fbradasc/RCTX/doc/PIC/328323-42266788.jpg

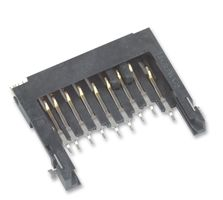
doc/PIC/328323-42266788.jpg
