fbradasc/RCTX/doc/EFR32M/Schematics/BRD4162A-A02-schematic.pdf

EFR32 Mighty Gecko Radio Board; 2.4 GHz 10 dBm, VDCDC to PAVDD

C | C
B | B
A | A
WSTK Connectors & Board ID | 4

# EFR32 Signal Assignments

Board Function | Page
| 1
| 2
| 3

# RF, Antenna & Power

# Title Page

# Revision History

Rev. | Description
A00 | Initial version.

# Updated EFR32 chip revision and 32 kHz

crystal part number.

A02 Fixing EFR32 pin names; Updated PCB revision.

A01

# Revision History

Rev. | Description
A00 | Initial version.

# Updated EFR32 chip revision and 32 kHz

crystal part number.

A02 Fixing EFR32 pin names; Updated PCB revision.

A01

# Revision History

Rev. | Description
A00 | Initial version.

# Updated EFR32 chip revision and 32 kHz

crystal part number.

A02 Fixing EFR32 pin names; Updated PCB revision.

A01

Size

Designed:

Revision

Sheet
of

Approved:

Sheet Created Date | Sheet Modified Date

## Document number

## Schematic Title

Design Created Date:

BOM Doc No:

## Page Title

BRD4162A | A02
Friday, January 20, 2017 | 1 | 4

A3

TAB | <OrgAddr2>

# EFR32MG12 2.4 GHz Radio Board

### <Cage Code>

Monday, April 02, 2012 | Monday, April 02, 2012

# SCHEMATIC1

# <Schematic Path>

# Title Page

Designed:

Approved:

## Schematic Title

## Page Title

Friday, January 20, 2017 | 1 | 4
TAB | <OrgAddr2>

# EFR32MG12 2.4 GHz Radio Board

Monday, April 02, 2012 | Monday, April 02, 2012

# SCHEMATIC1

# <Schematic Path>

# Title Page

Designed:

Approved:

## Schematic Title

## Page Title

Friday, January 20, 2017 | 1 | 4
TAB | <OrgAddr2>

# EFR32MG12 2.4 GHz Radio Board

Monday, April 02, 2012 | Monday, April 02, 2012

# SCHEMATIC1

# <Schematic Path>

# Title Page

PCB1

PCB4162A

# Antenna & Radio Interface

## High Frequency

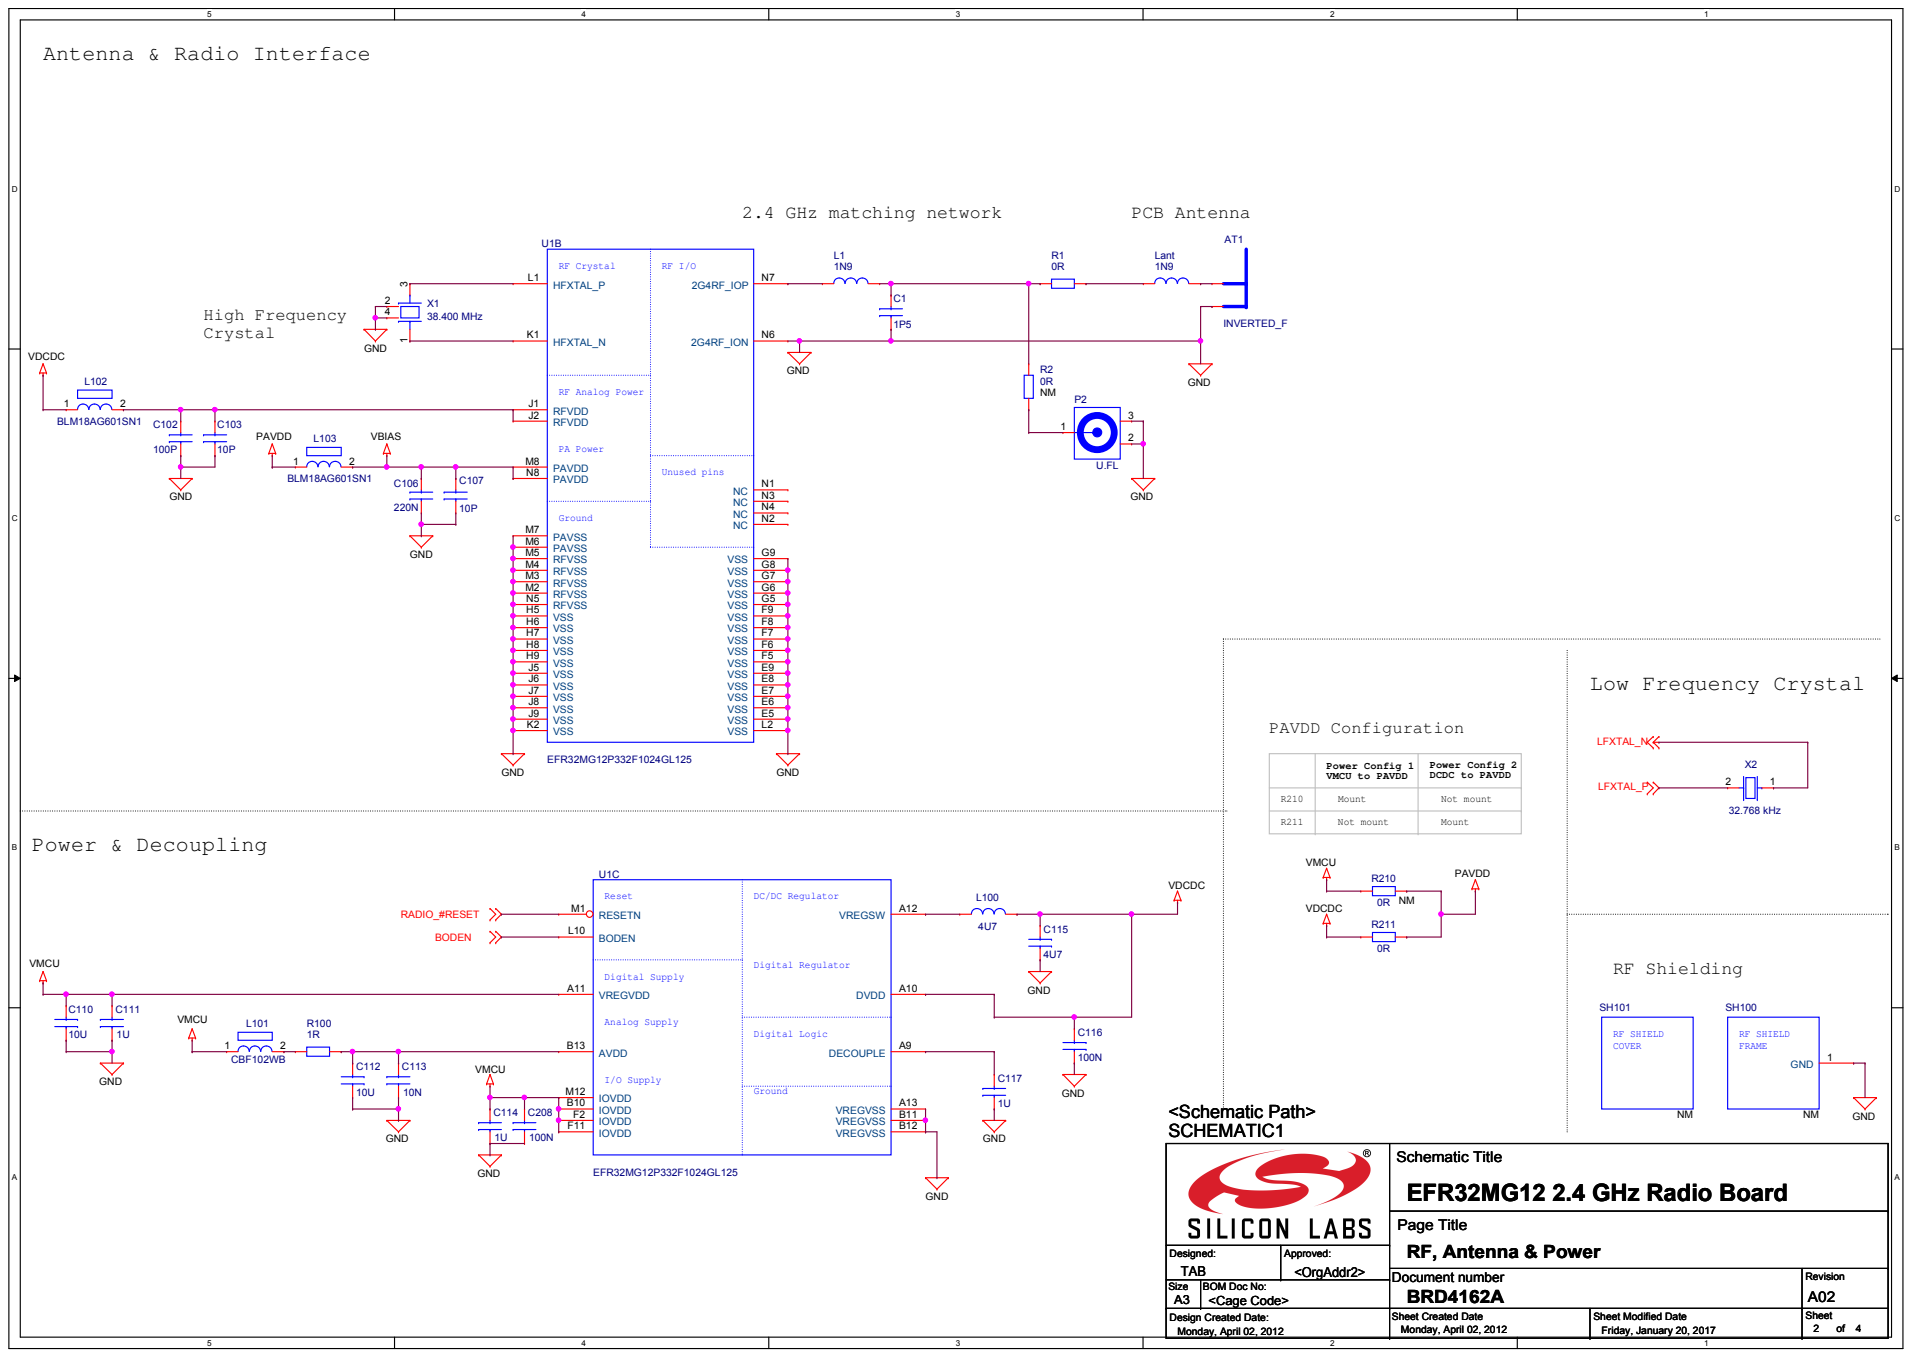
[picture p24: page 2]

# EFR32 I/O Port Pins EFR32 Pin Mapping

### EFR32 Pin EFR32 Peripheral

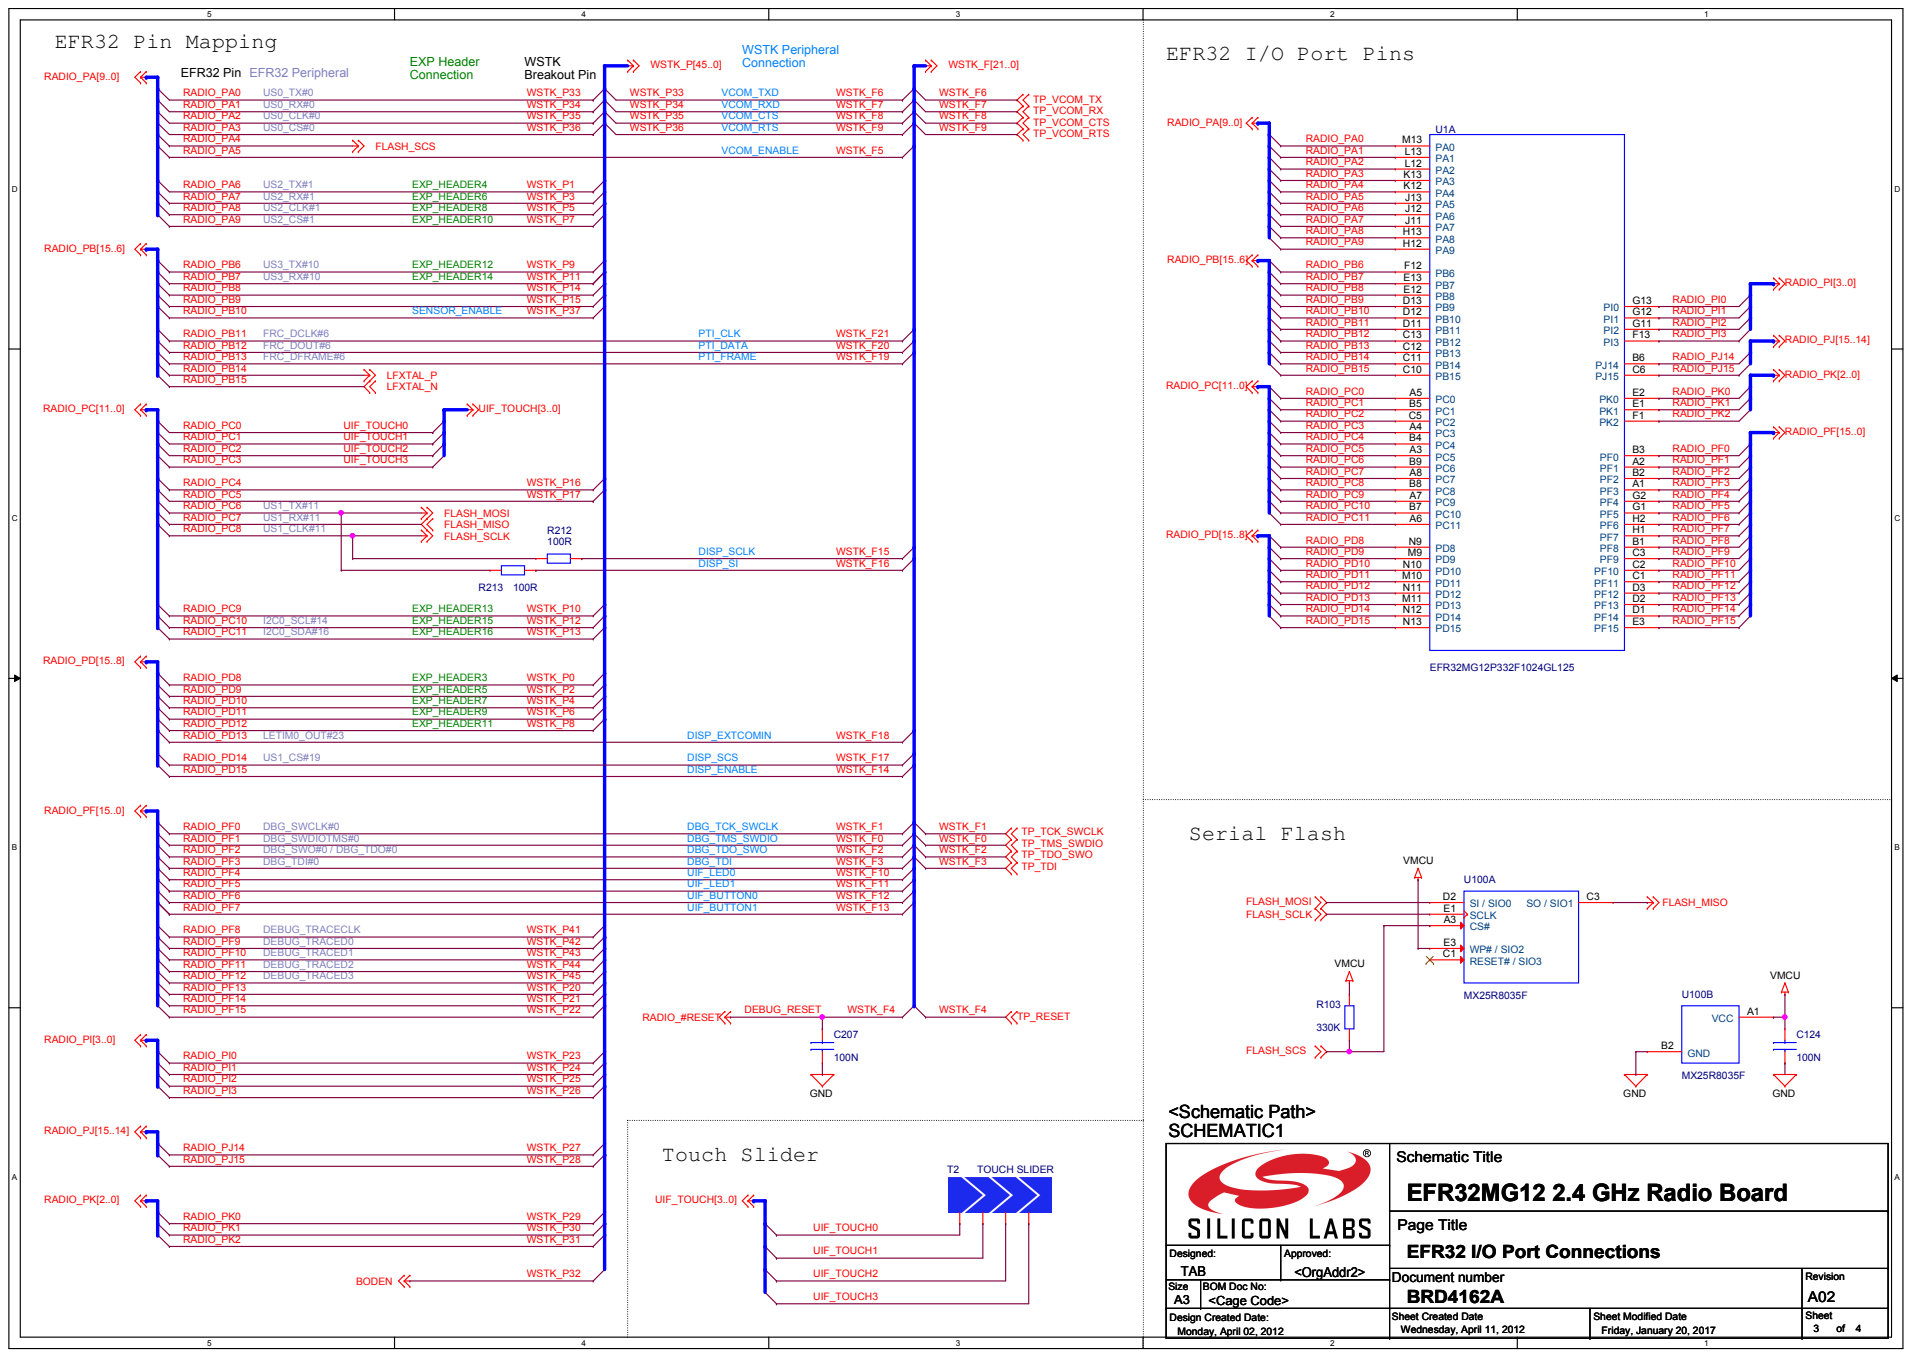
[picture p25: page 3]

# WSTK Connectors

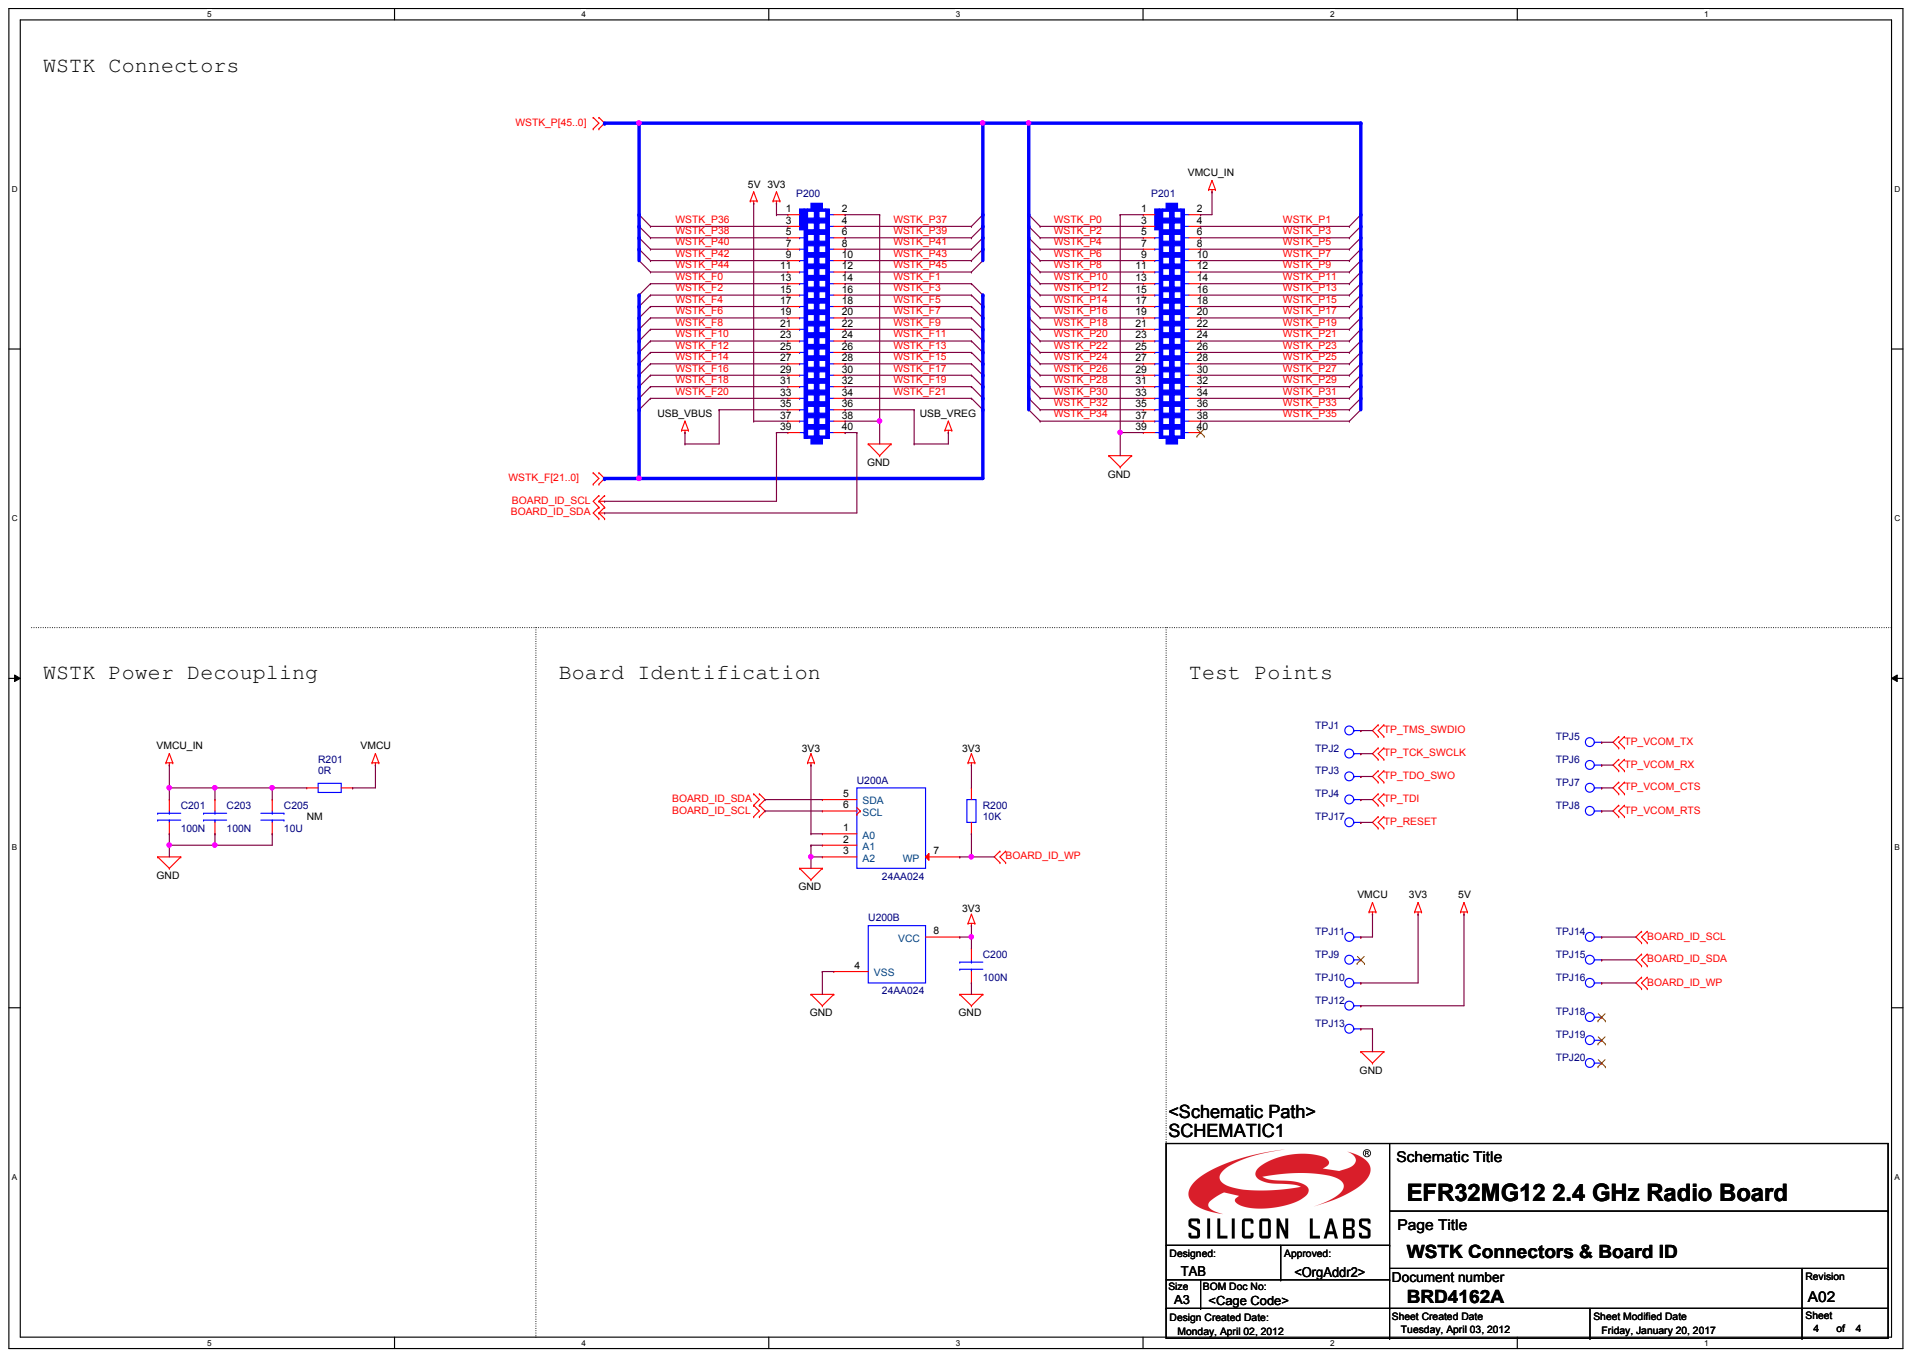
[picture p26: page 4]

Page Title
WSTK Connectors & Board ID
