fbradasc/RCTX/doc/EFR32M/Schematics/BRD4163A-A02-schematic.pdf

EFR32 Mighty Gecko Radio Board

C | C
B | B
A | A
WSTK Connectors & Board ID | 4

# EFR32 Signal Assignments

Board Function | Page
| 1
| 2
| 3

# RF, Antenna & Power

# Title Page

# Revision History

Rev. | Description
A00 | Initial version.

# Updated EFR32 chip revision and 32 kHz

crystal part number.

A02 Fixing EFR32 pin names; Updated PCB revision.

A01

# Revision History

Rev. | Description
A00 | Initial version.

# Updated EFR32 chip revision and 32 kHz

crystal part number.

A02 Fixing EFR32 pin names; Updated PCB revision.

A01

# Revision History

Rev. | Description
A00 | Initial version.

# Updated EFR32 chip revision and 32 kHz

crystal part number.

A02 Fixing EFR32 pin names; Updated PCB revision.

A01

# 2.4 GHz / 868 MHz 10 dBm, VDCDC to PAVDD

Size

Designed:

Revision

Sheet
of

Approved:

Sheet Created Date | Sheet Modified Date

## Document number

## Schematic Title

Design Created Date:

BOM Doc No:

## Page Title

BRD4163A | A02
Friday, January 20, 2017 | 1 | 4

A3

TAB | <OrgAddr2>

# EFR32MG12 Dual Band 2400/868 MHz Radio Board

### <Cage Code>

Monday, April 02, 2012 | Monday, April 02, 2012

# SCHEMATIC1

# <Schematic Path>

# Title Page

Designed:

Approved:

## Schematic Title

## Page Title

Friday, January 20, 2017 | 1 | 4
TAB | <OrgAddr2>

# EFR32MG12 Dual Band 2400/868 MHz Radio Board

Monday, April 02, 2012 | Monday, April 02, 2012

# SCHEMATIC1

# <Schematic Path>

# Title Page

Designed:

Approved:

## Schematic Title

## Page Title

Friday, January 20, 2017 | 1 | 4
TAB | <OrgAddr2>

# EFR32MG12 Dual Band 2400/868 MHz Radio Board

Monday, April 02, 2012 | Monday, April 02, 2012

# SCHEMATIC1

# <Schematic Path>

# Title Page

PCB1

PCB4163A

# Antenna & Radio Interface

## High Frequency

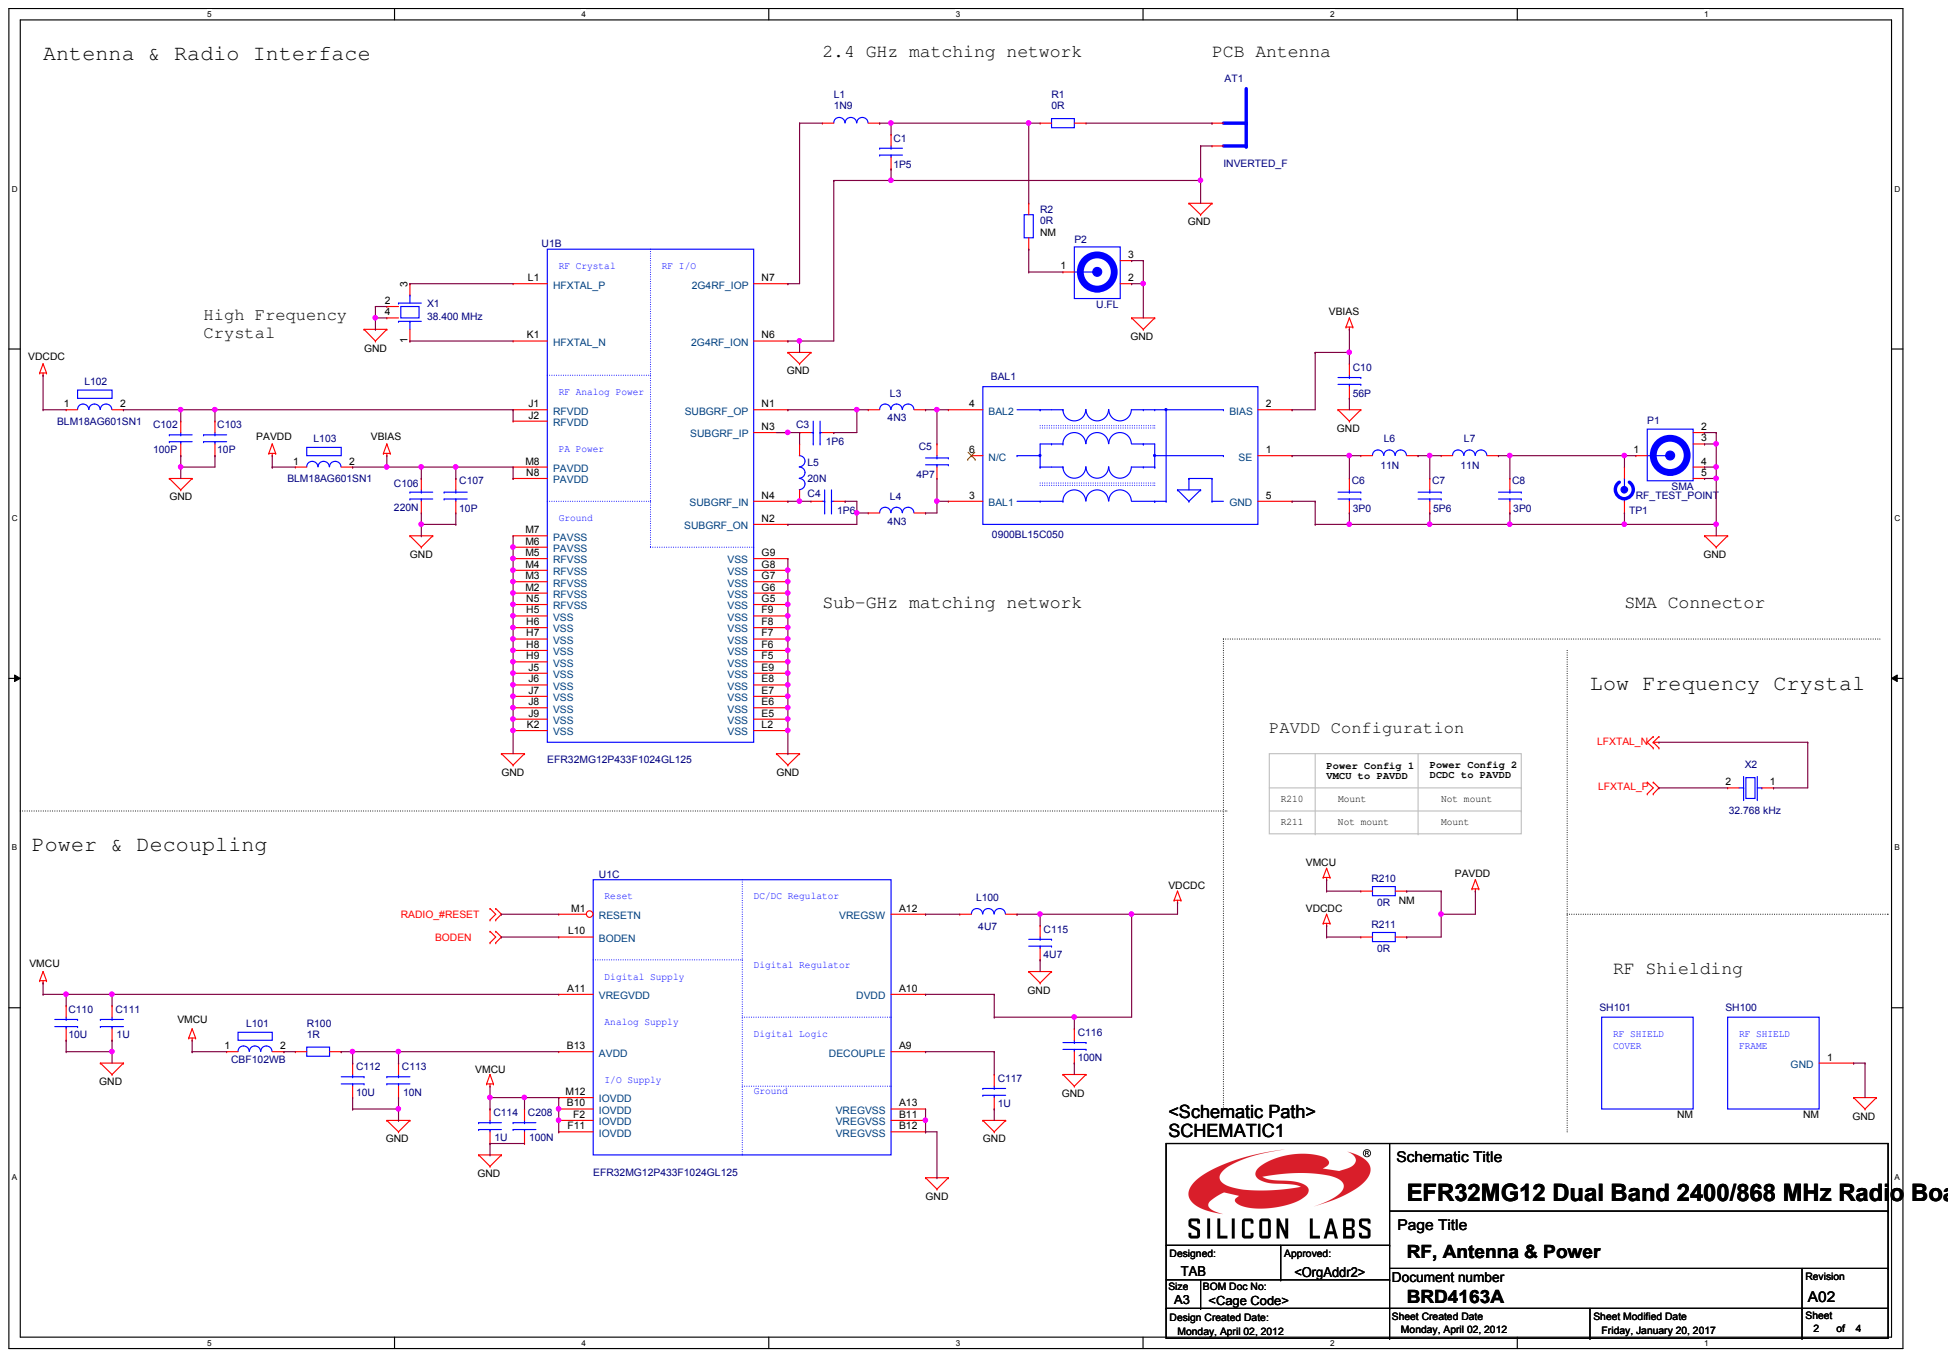
[picture p37: page 2]

Sub-GHz matching network

Schematic Title
EFR32MG12 Dual Band 2400/868 MHz Radio Board

# EFR32 I/O Port Pins EFR32 Pin Mapping

### EFR32 Pin EFR32 Peripheral

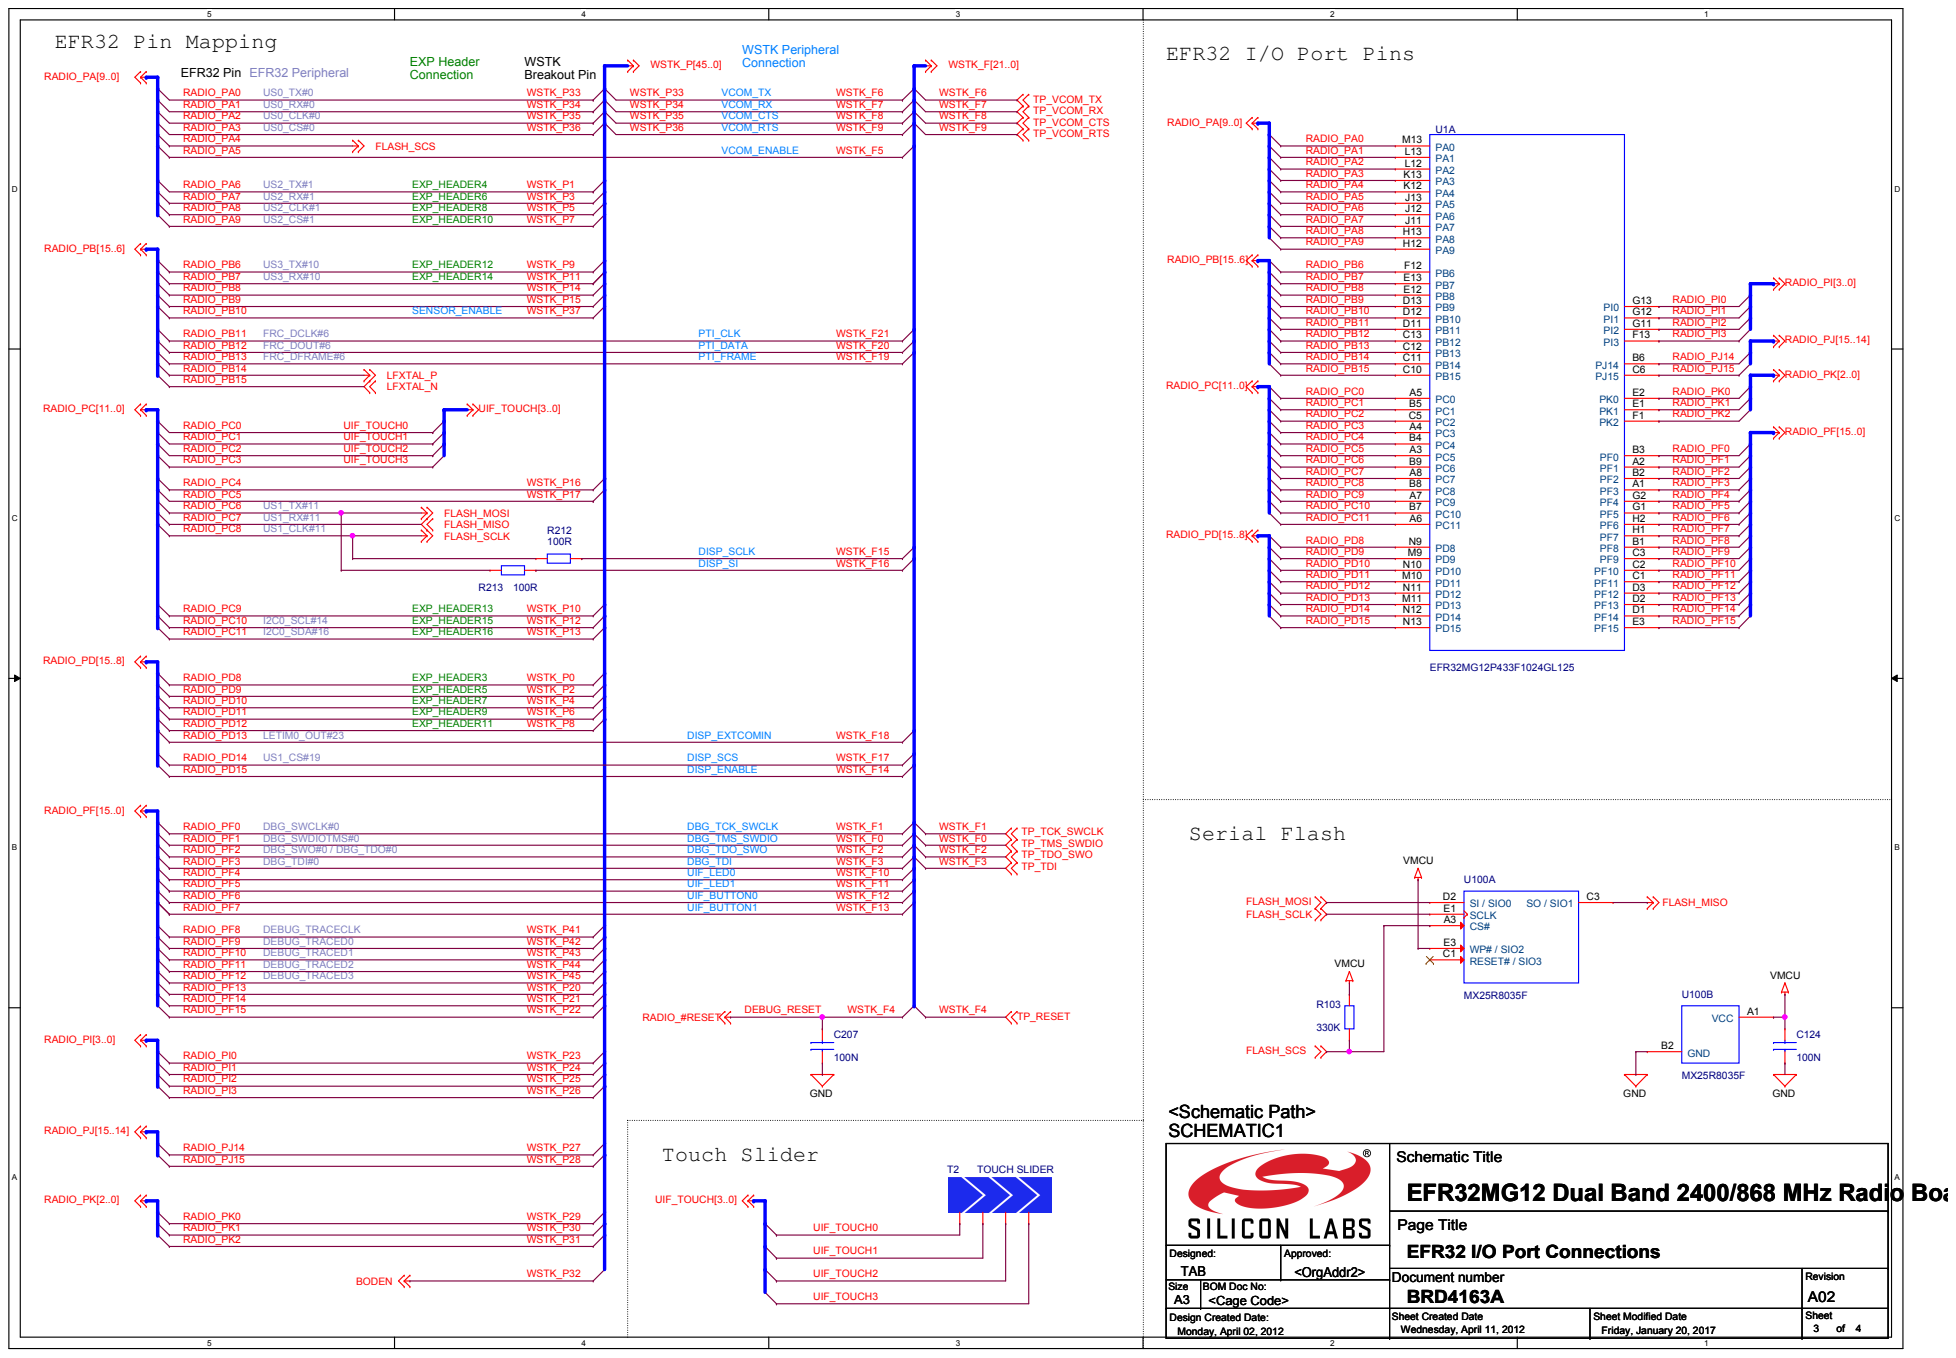
[picture p38: page 3]

Schematic Title
EFR32MG12 Dual Band 2400/868 MHz Radio Board

# WSTK Connectors

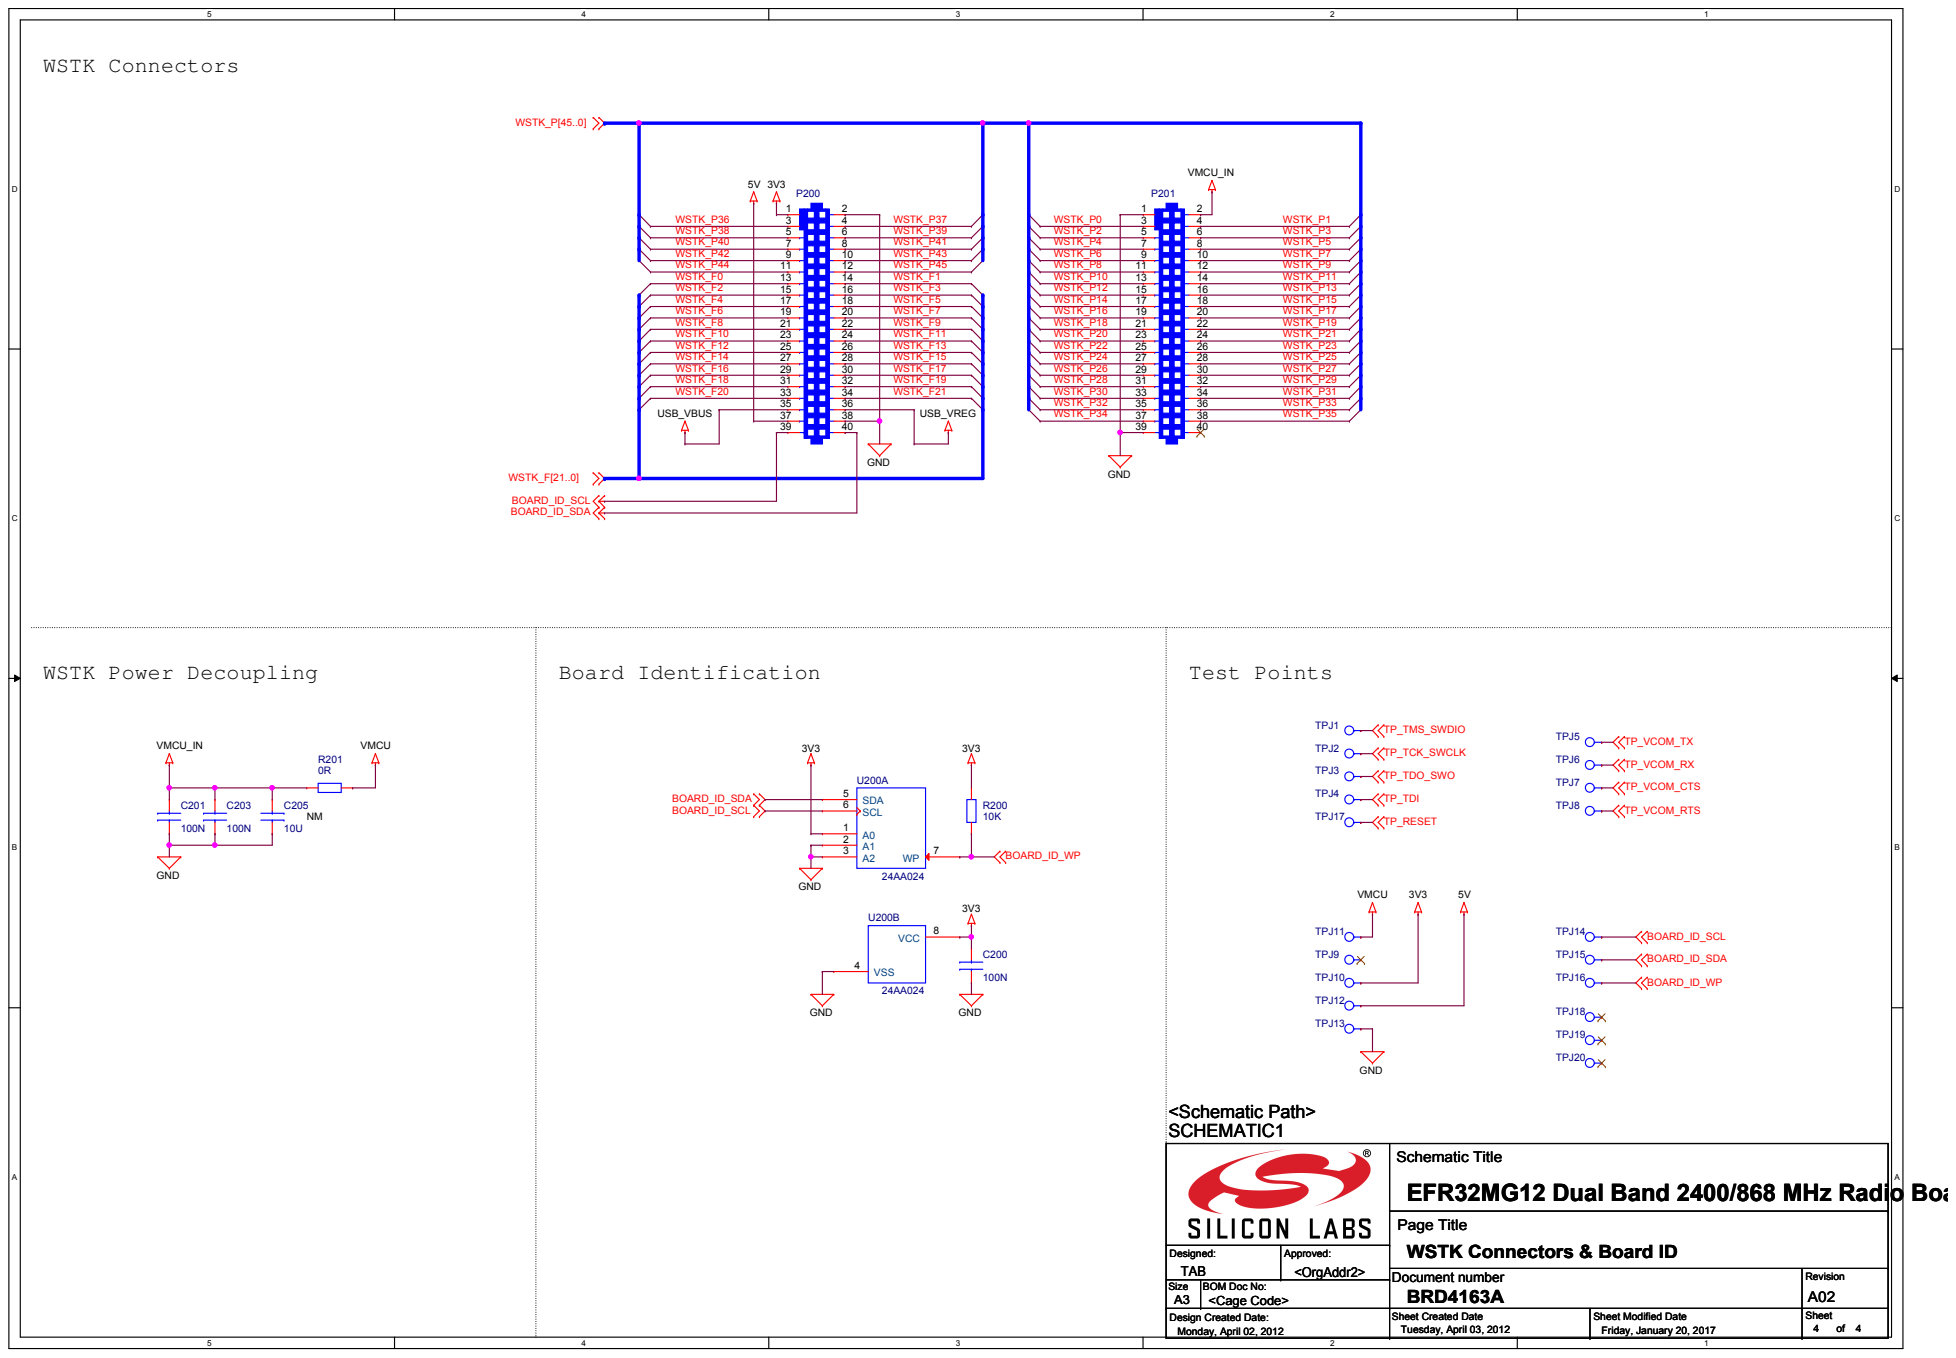
[picture p39: page 4]

Schematic Title
EFR32MG12 Dual Band 2400/868 MHz Radio Board

Page Title
WSTK Connectors & Board ID
