fbradasc/RCTX/doc/EFR32M/Schematics/BRD4164A-A01-schematic.pdf

EFR32 Mighty Gecko Radio Board; 2.4 GHz / 915 MHz 19 dBm, VMCU to PAVDD

C | C
B | B
A | A
WSTK Connectors & Board ID | 4

# EFR32 Signal Assignments

Board Function | Page
| 1
| 2
| 3

# RF, Antenna & Power

# Title Page

# Revision History

Rev. | Description
A00 | Initial version.
A01 | Fixing EFR part number.

# Revision History

Rev. | Description
A00 | Initial version.
A01 | Fixing EFR part number.

# Revision History

Rev. | Description
A00 | Initial version.
A01 | Fixing EFR part number.

Size

Designed:

Revision

Sheet
of

Approved:

Sheet Created Date | Sheet Modified Date

## Document number

## Schematic Title

Design Created Date:

BOM Doc No:

## Page Title

BRD4164A | A01
Tuesday, October 25, 2016 | 1 | 4

A3

TAB | <OrgAddr2>

# EFR32MG12 Dual Band 2400/915 MHz Radio Board

### <Cage Code>

Monday, April 02, 2012 | Monday, April 02, 2012

# SCHEMATIC1

# <Schematic Path>

# Title Page

Designed:

Approved:

## Schematic Title

## Page Title

Tuesday, October 25, 2016 | 1 | 4
TAB | <OrgAddr2>

# EFR32MG12 Dual Band 2400/915 MHz Radio Board

Monday, April 02, 2012 | Monday, April 02, 2012

# SCHEMATIC1

# <Schematic Path>

# Title Page

Designed:

Approved:

## Schematic Title

## Page Title

Tuesday, October 25, 2016 | 1 | 4
TAB | <OrgAddr2>

# EFR32MG12 Dual Band 2400/915 MHz Radio Board

Monday, April 02, 2012 | Monday, April 02, 2012

# SCHEMATIC1

# <Schematic Path>

# Title Page

PCB1

PCB4164A

# Antenna & Radio Interface

## High Frequency

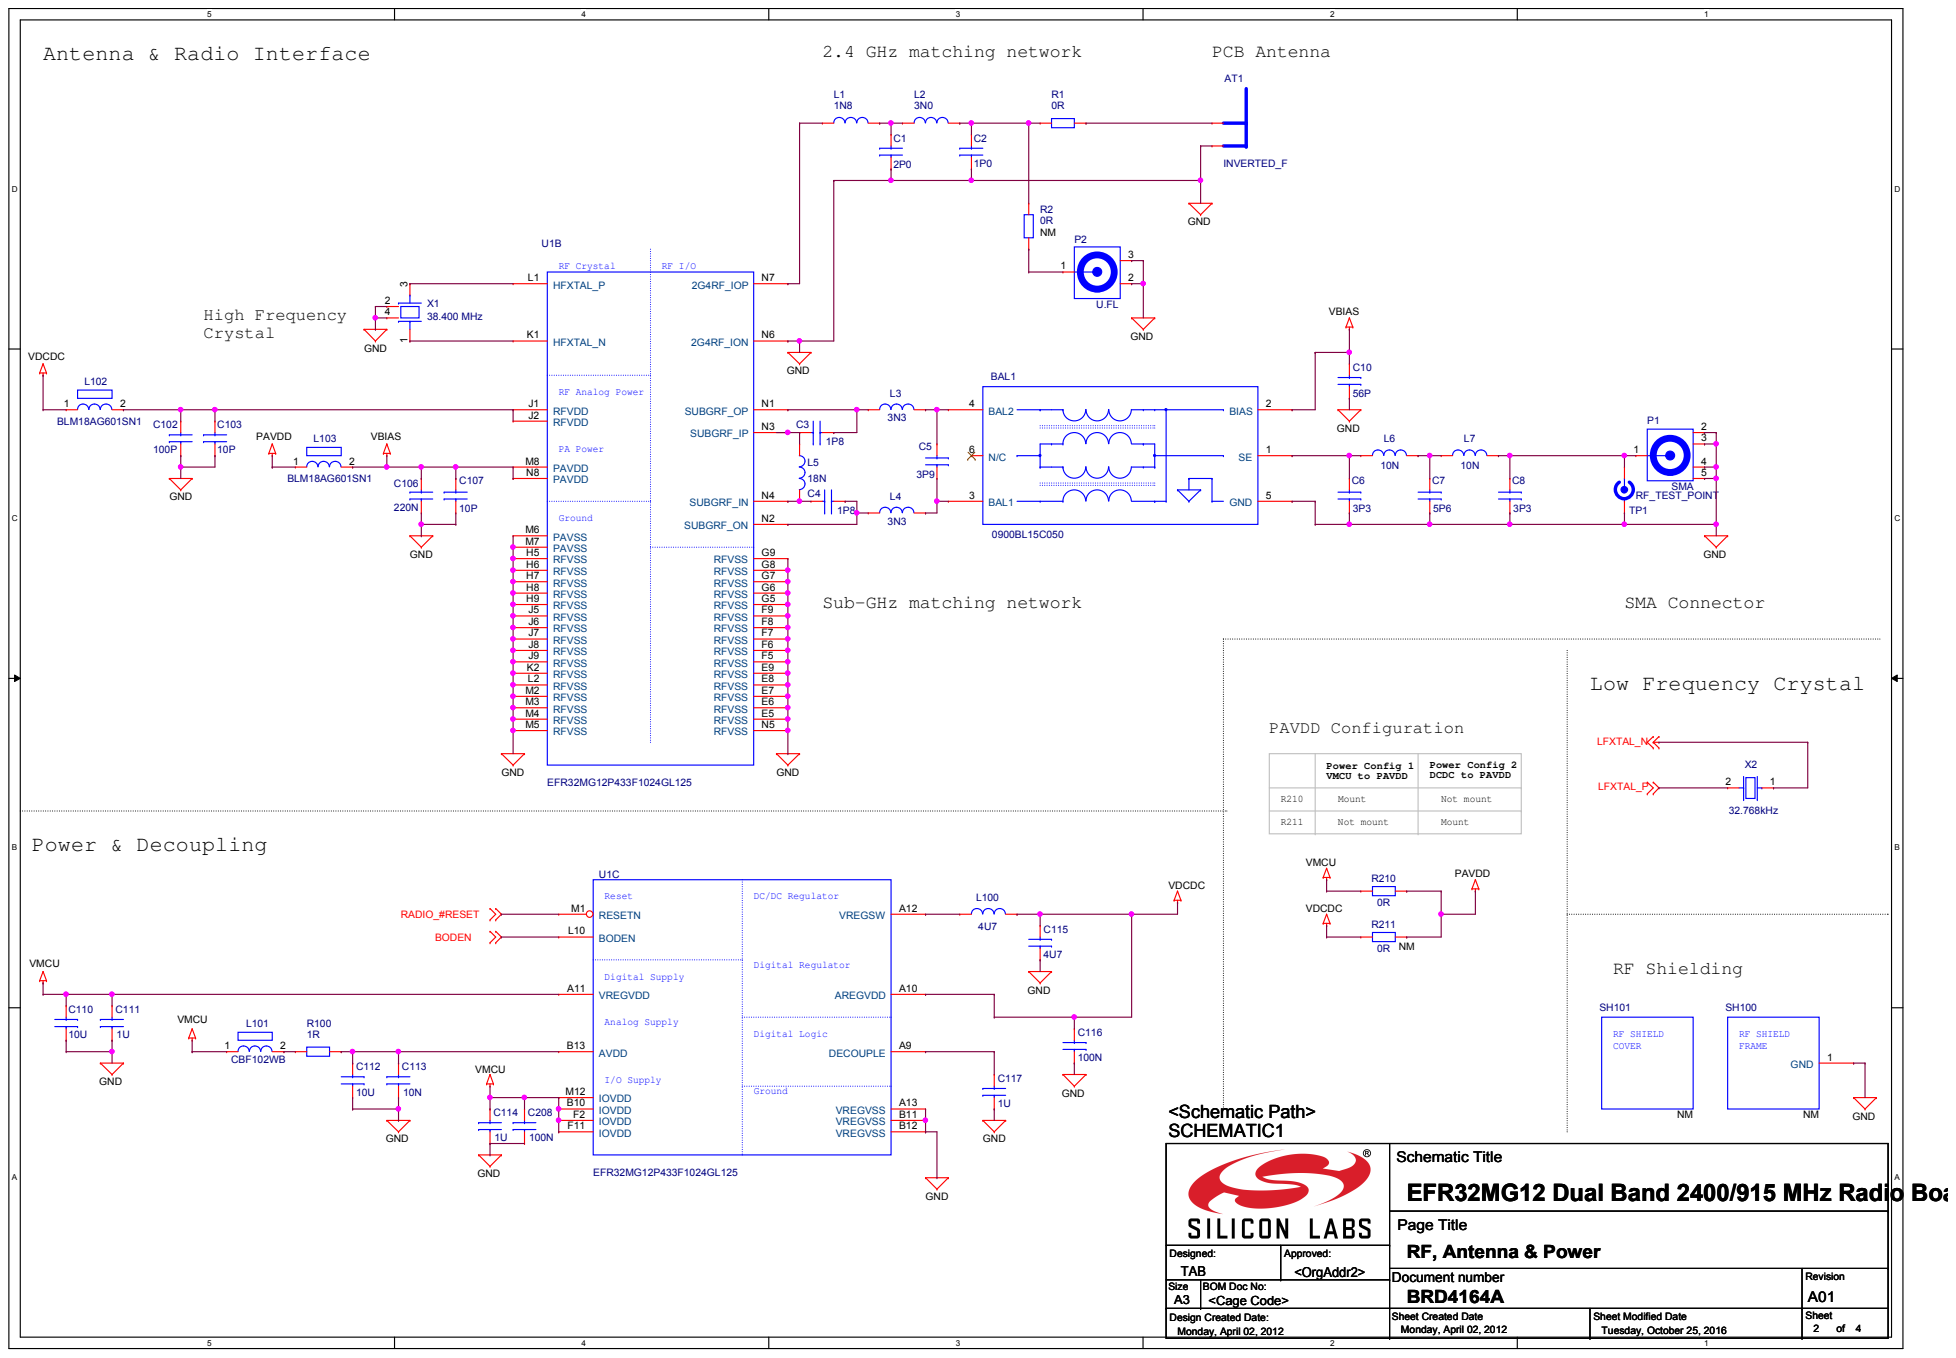
[picture p47: page 2]

Sub-GHz matching network

Schematic Title
EFR32MG12 Dual Band 2400/915 MHz Radio Board

# EFR32 I/O Port Pins EFR32 Pin Mapping

### EFR32 Pin EFR32 Peripheral

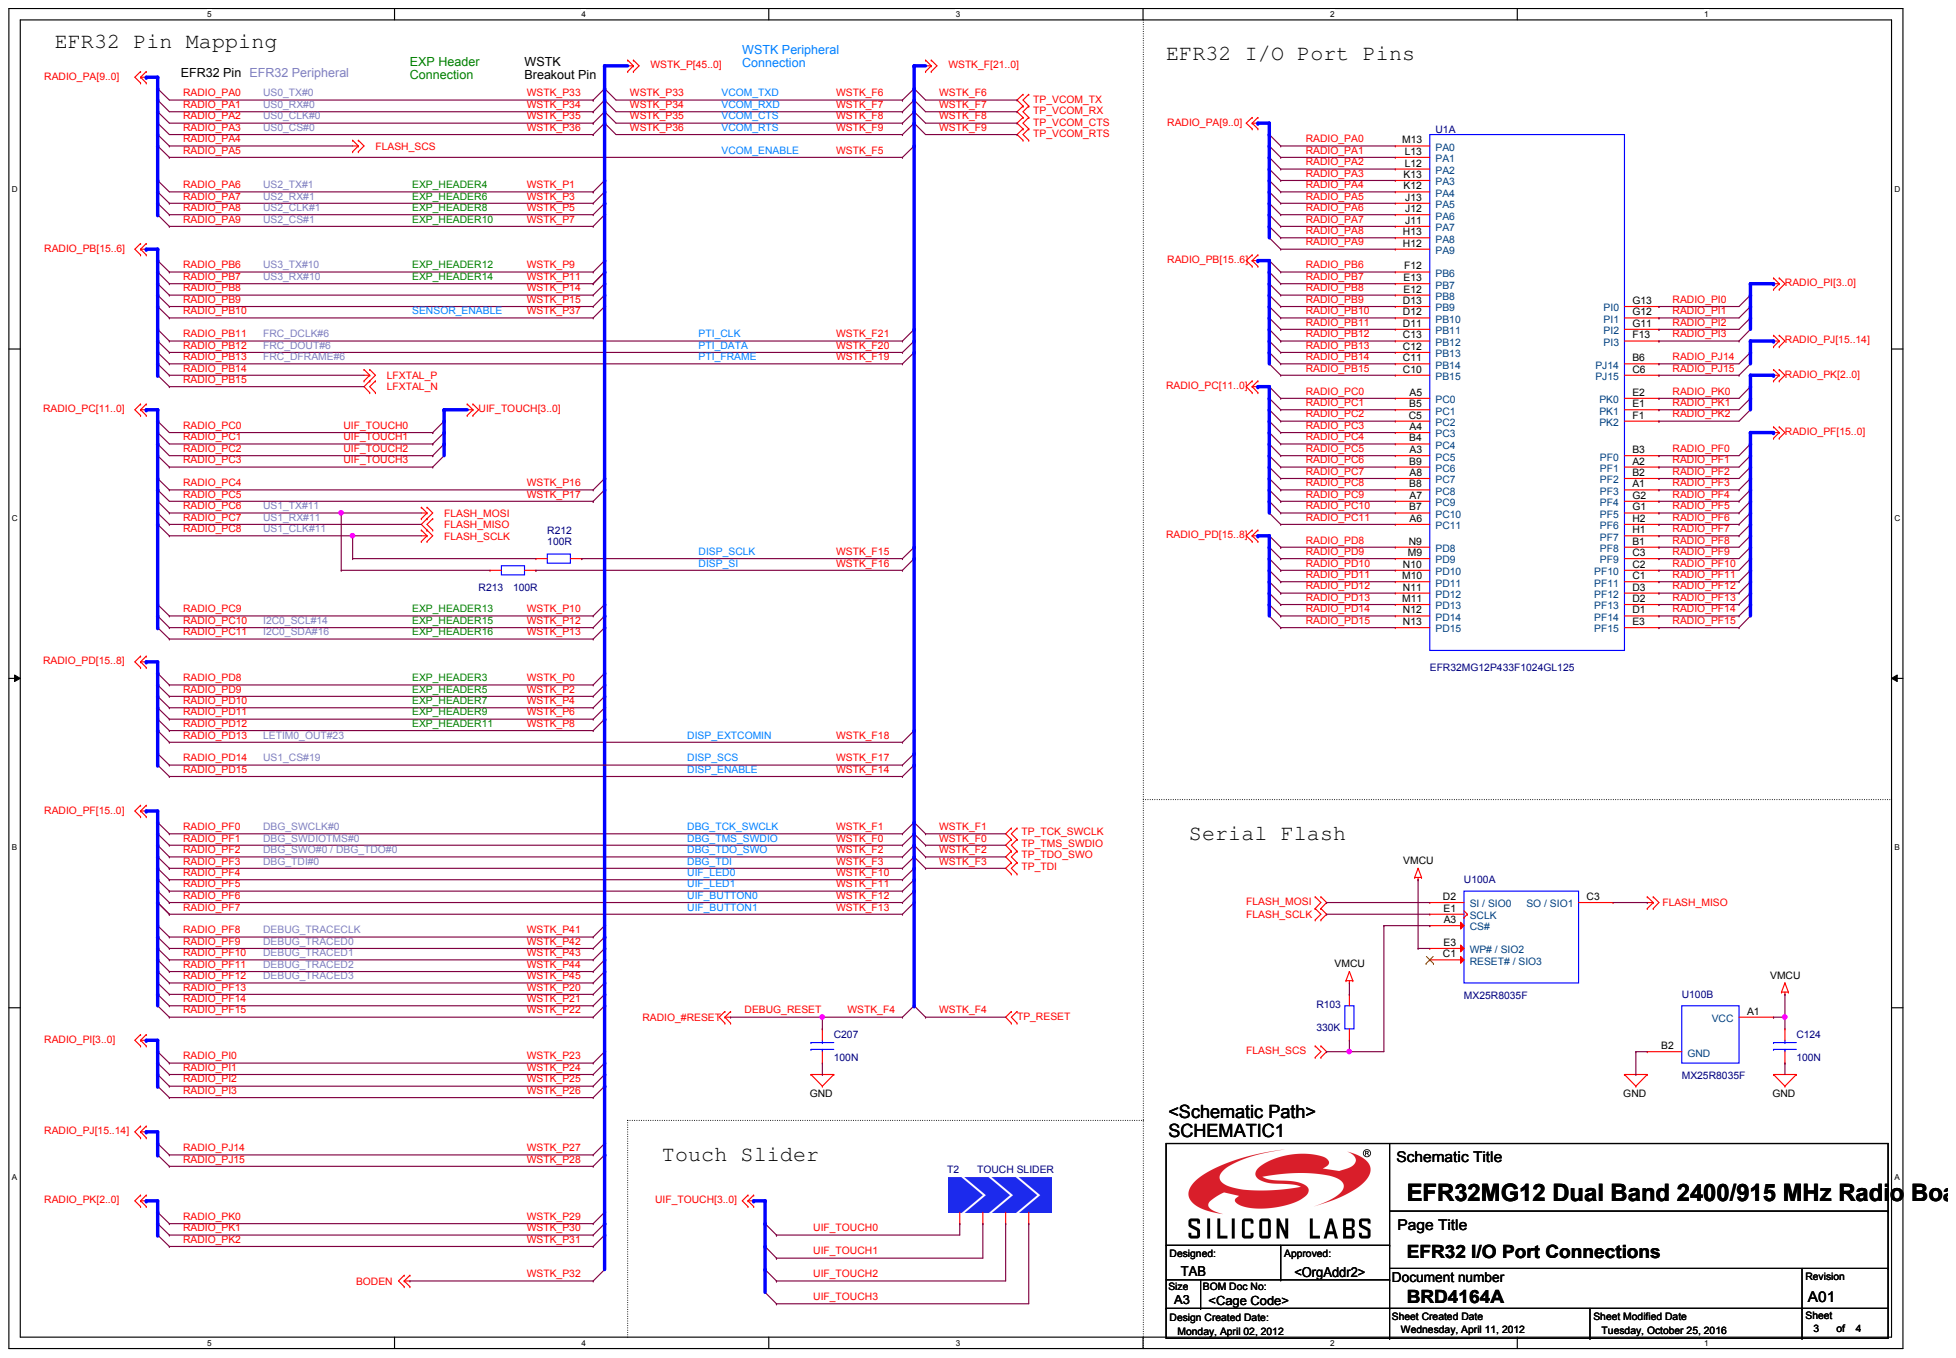
[picture p48: page 3]

Schematic Title
EFR32MG12 Dual Band 2400/915 MHz Radio Board

# WSTK Connectors

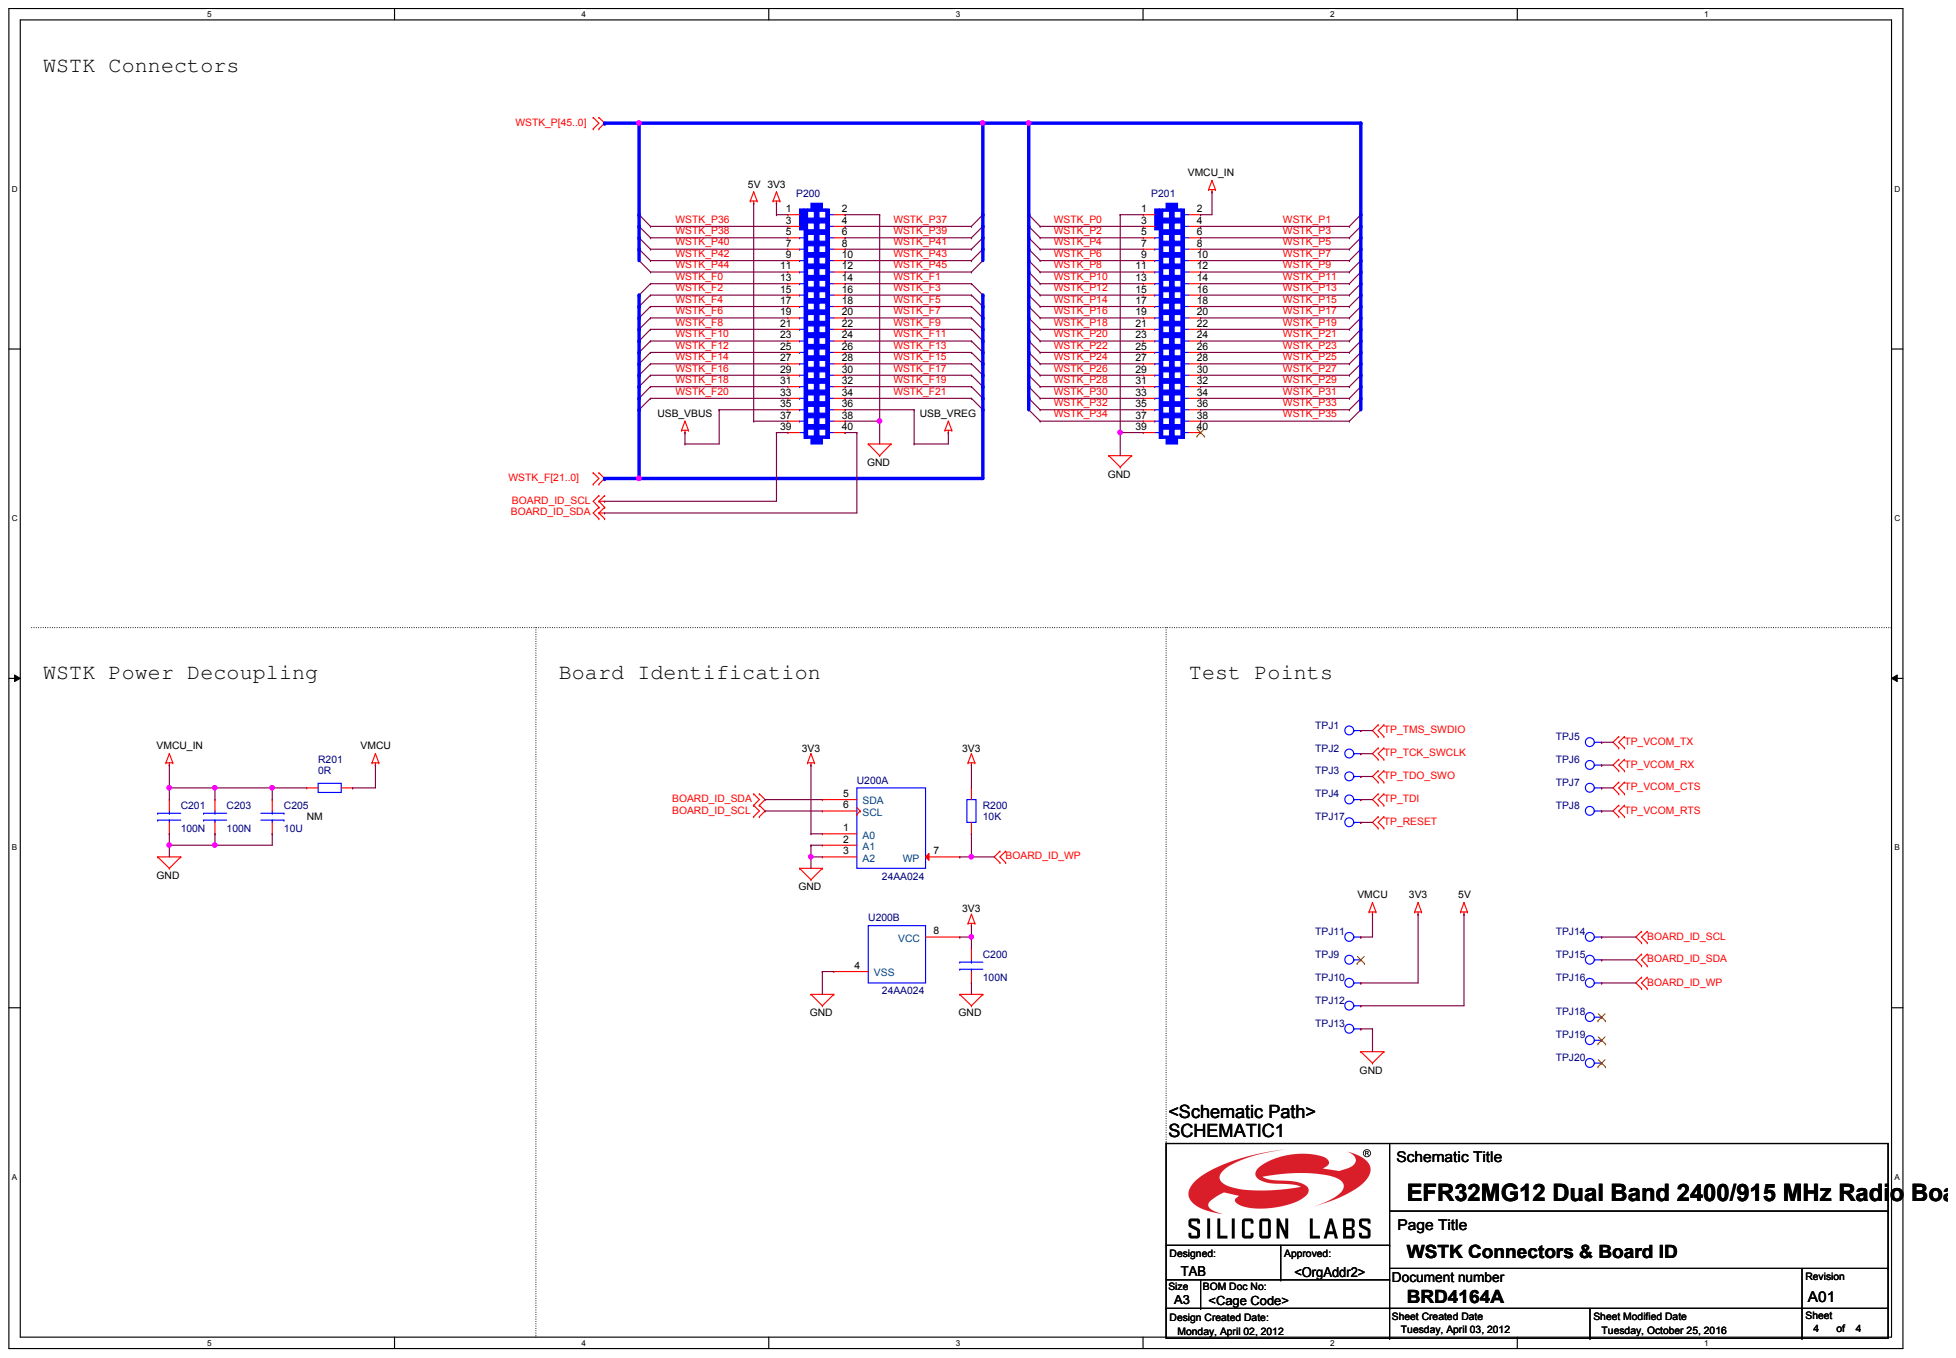
[picture p49: page 4]

Schematic Title
EFR32MG12 Dual Band 2400/915 MHz Radio Board

Page Title
WSTK Connectors & Board ID
