fbradasc/RCTX/doc/EFR32M/Schematics/BRD4166A-D00-schematic.pdf

Thunderboard Sense

C | C
B | B
A | A
Board Function | Page
| 1
| 2
| 3

# EFR32 RF, Power & IO

# Title Page

MEMS Microphone & RGB LEDs | 4

# EFR32 connections & interfaces

# Rev. Description

# Revision History

SPI & I2C Sensors | 5
Debug MCU | 6
Debug Misc. & Power | 7

# EFR32MG12P332F1024GL125

A00 Initial prototype version.

# Updated EFR32 and debugger IC

revisions.

# Replaced analog microphone with an

I2S-based digital one.

B00

# Changed microphone to Knowles SPH0645LM4H-B

B01

# Updated microphone and SPI Flash pinout. Changed to Invensense

microphone and 9-axis IMU.

C00

C01 | Updated hall effect sensor (Si7210) revision.
D00 | Changed back to Invensense 6-axis IMU.

Size

Designed:

Revision

Sheet
of

Approved:

Sheet Created Date | Sheet Modified Date

## Document number

## Schematic Title

Design Created Date:

BOM Doc No:

## Page Title

BRD4166A | D00
Monday, September 25, 2017 | 1 | 7

A3

DDB | JNO

# Thunderboard Sense

### <Cage Code>

Wednesday, November 30, 2016 | Wednesday, November 30, 2016

# SCHEMATIC1

# Title Page

Designed:
Approved:

## Schematic Title

## Page Title

Monday, September 25, 2017 | 1 | 7
DDB | JNO

# Thunderboard Sense

# SCHEMATIC1

# Title Page

Designed:
Approved:

## Schematic Title

## Page Title

Monday, September 25, 2017 | 1 | 7
DDB | JNO

# Thunderboard Sense

# SCHEMATIC1

# Title Page

PCB1

PCB4166

## 2.4 GHz matching network

# RF Section

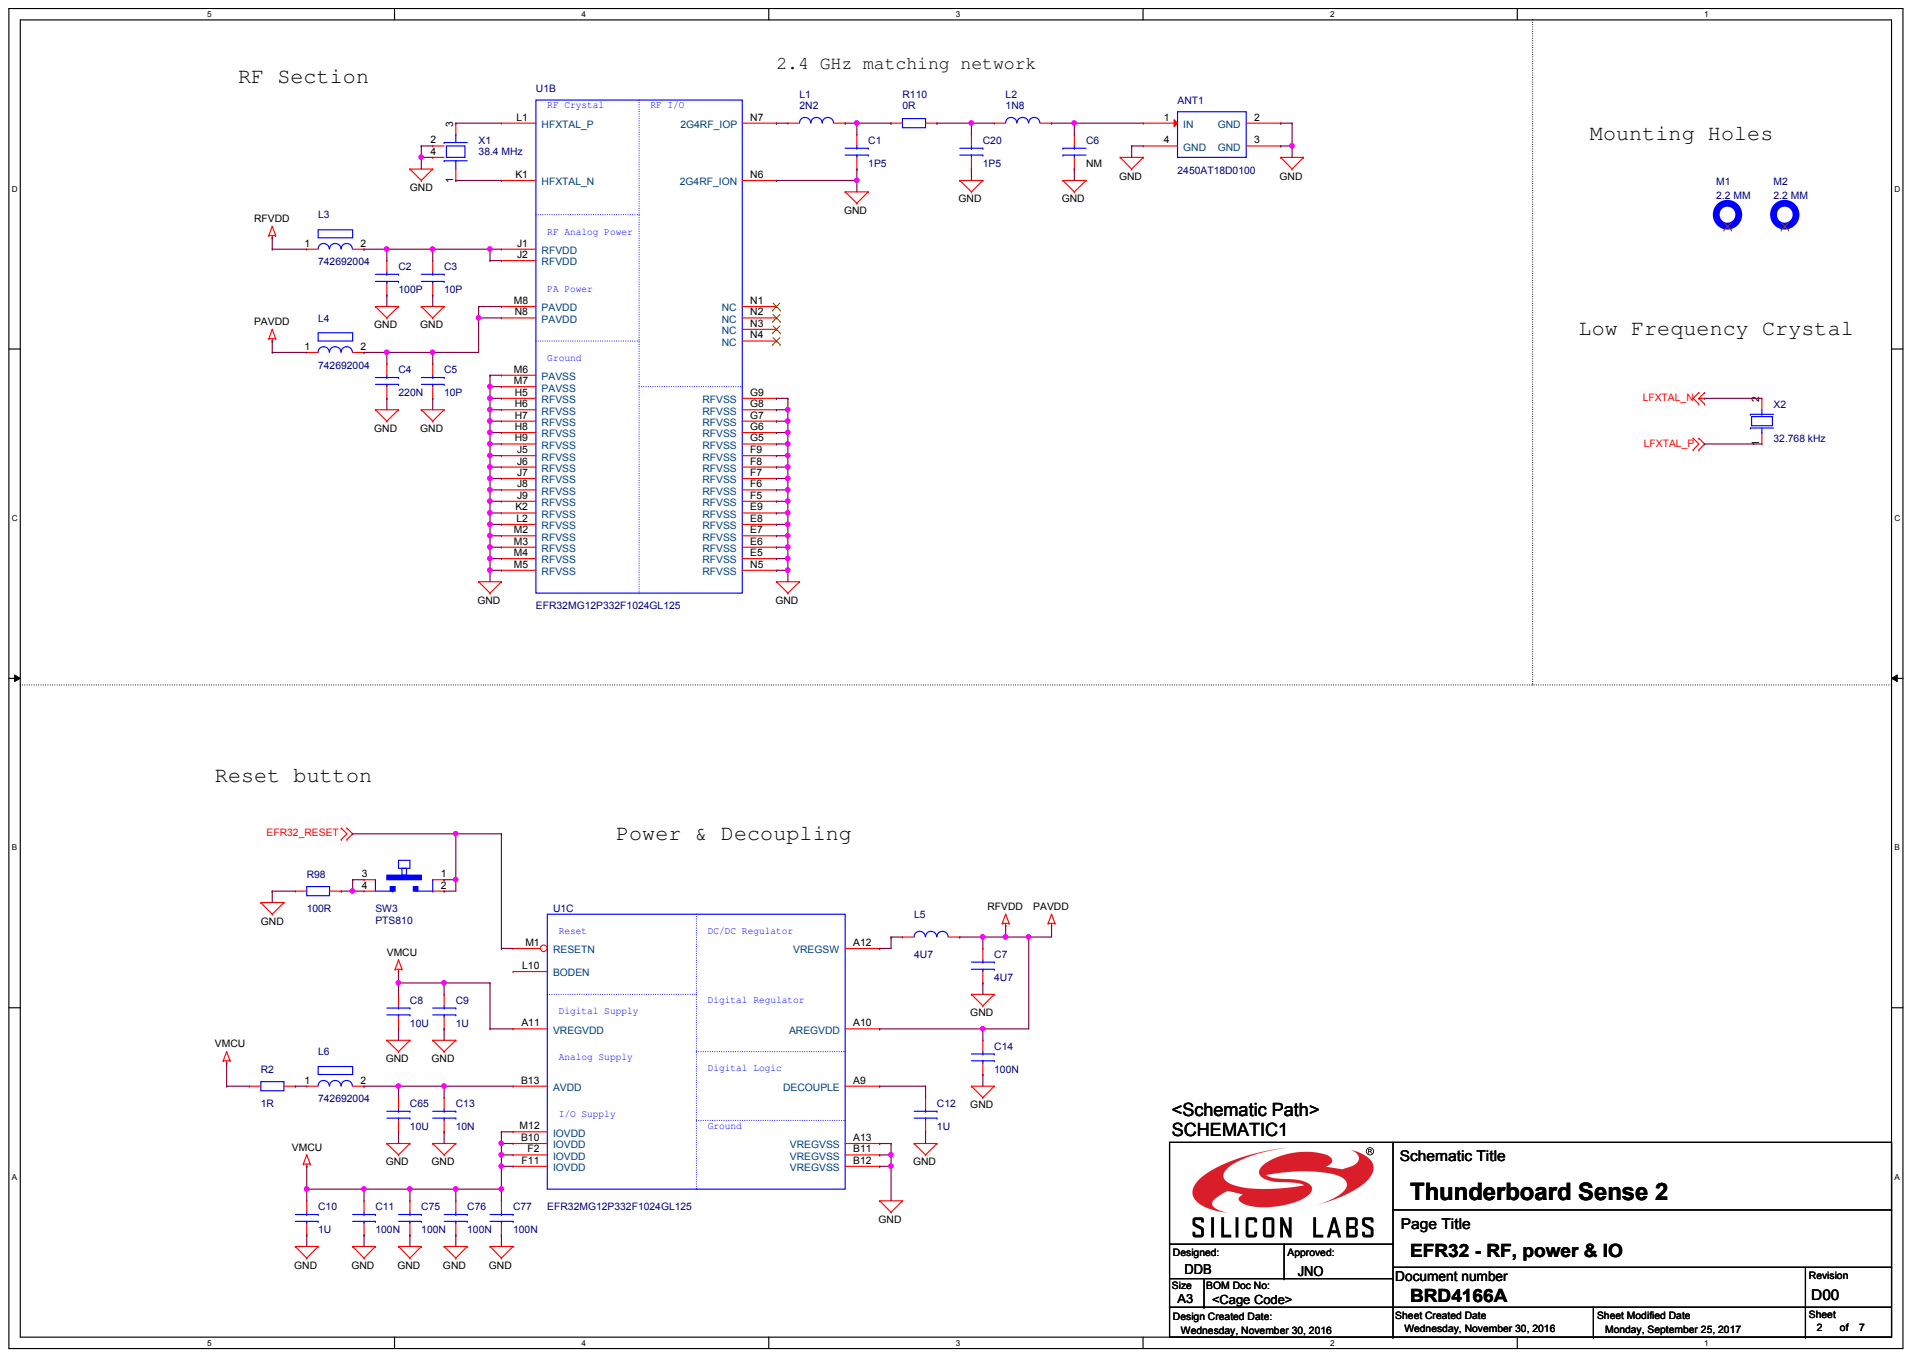
[picture p88: page 2]

# Breakout Pads - EXP Header

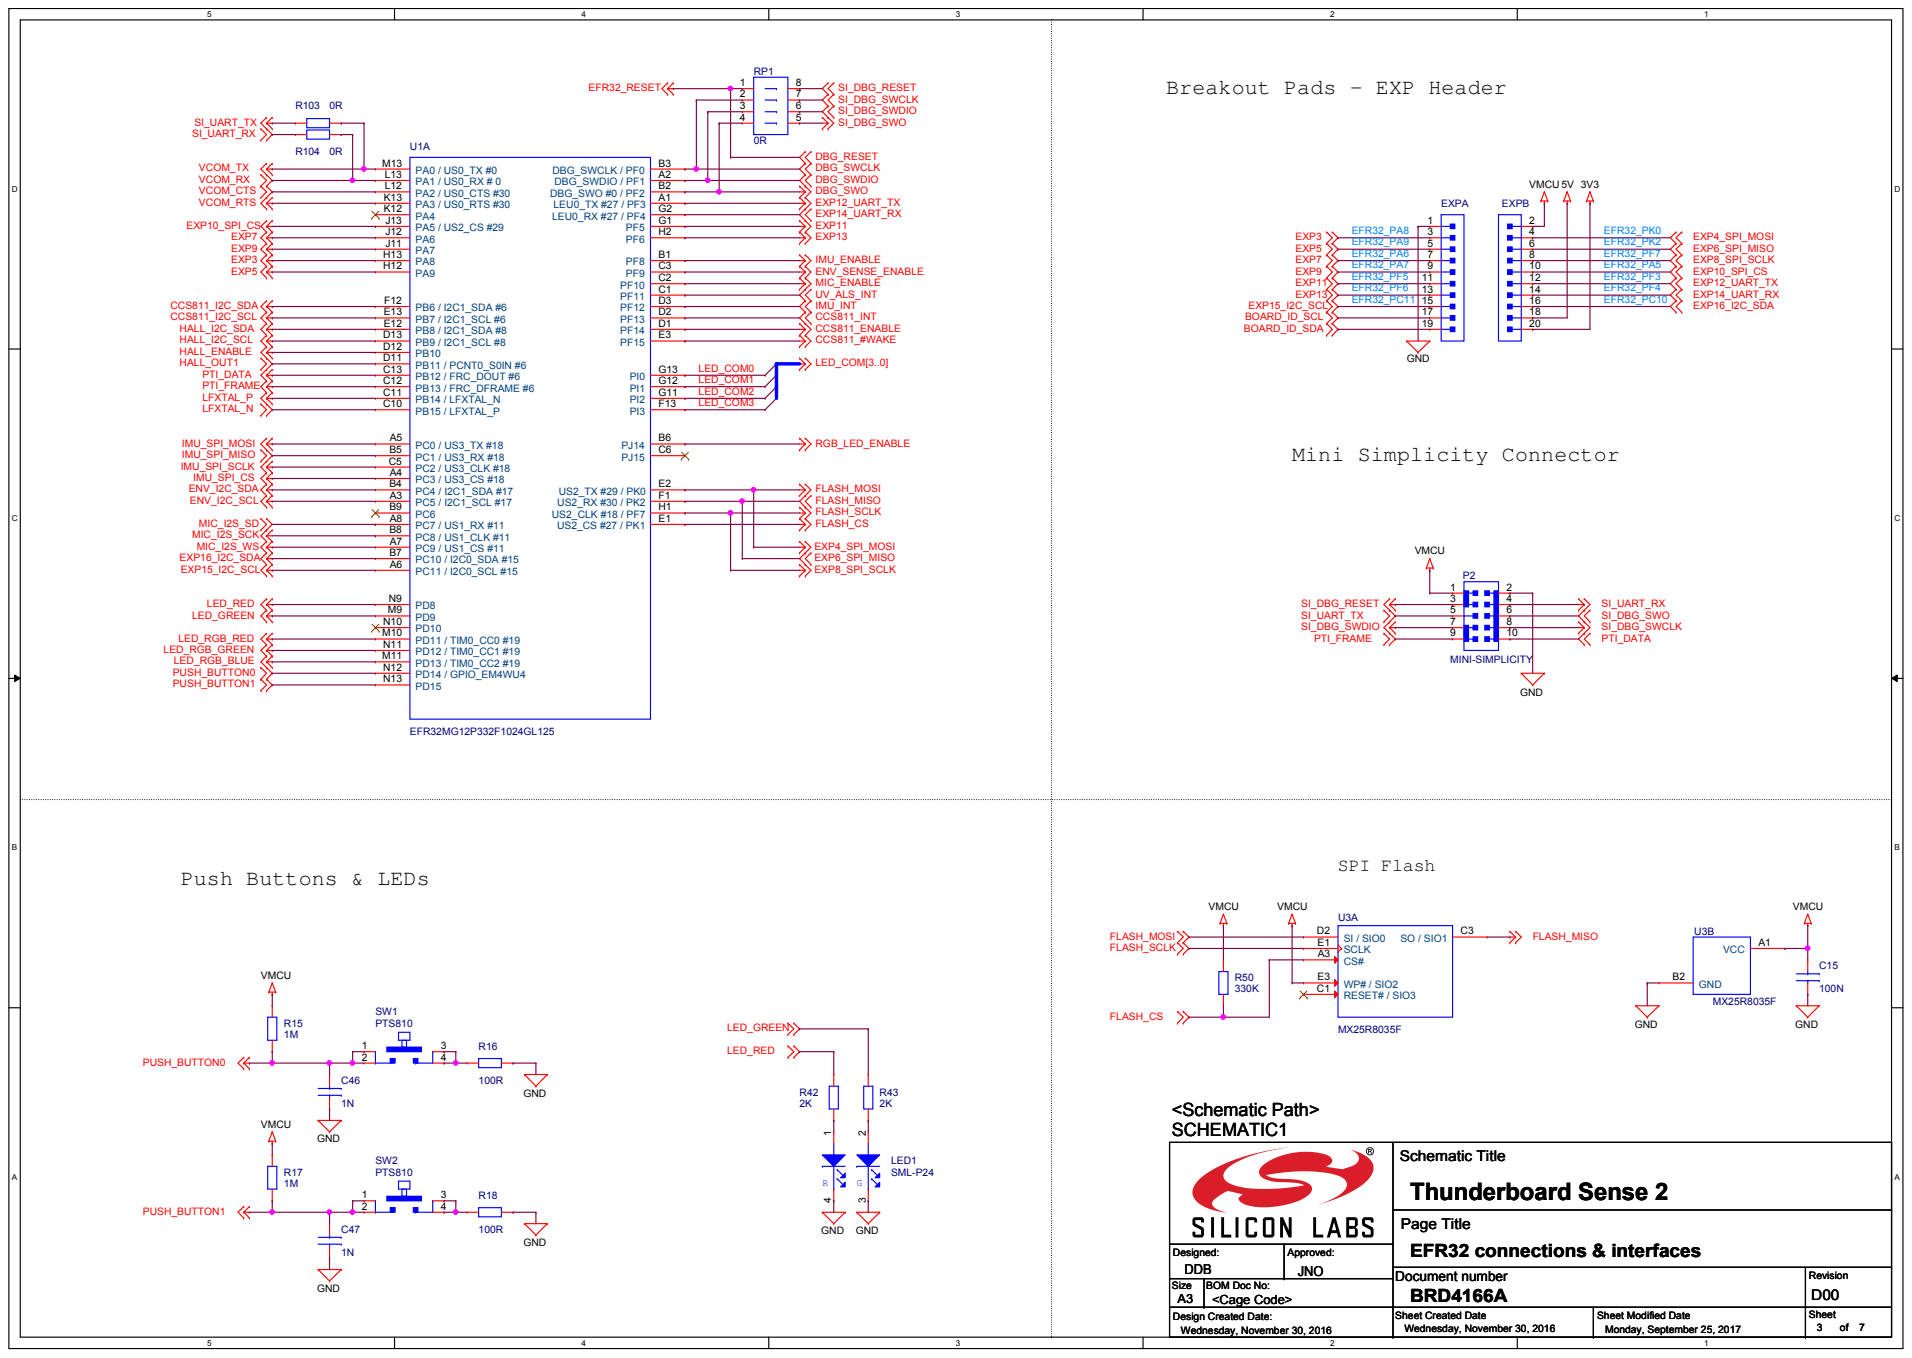
[picture p89: page 3]

B | GND | B

GND | GND

## MEMS Microphone

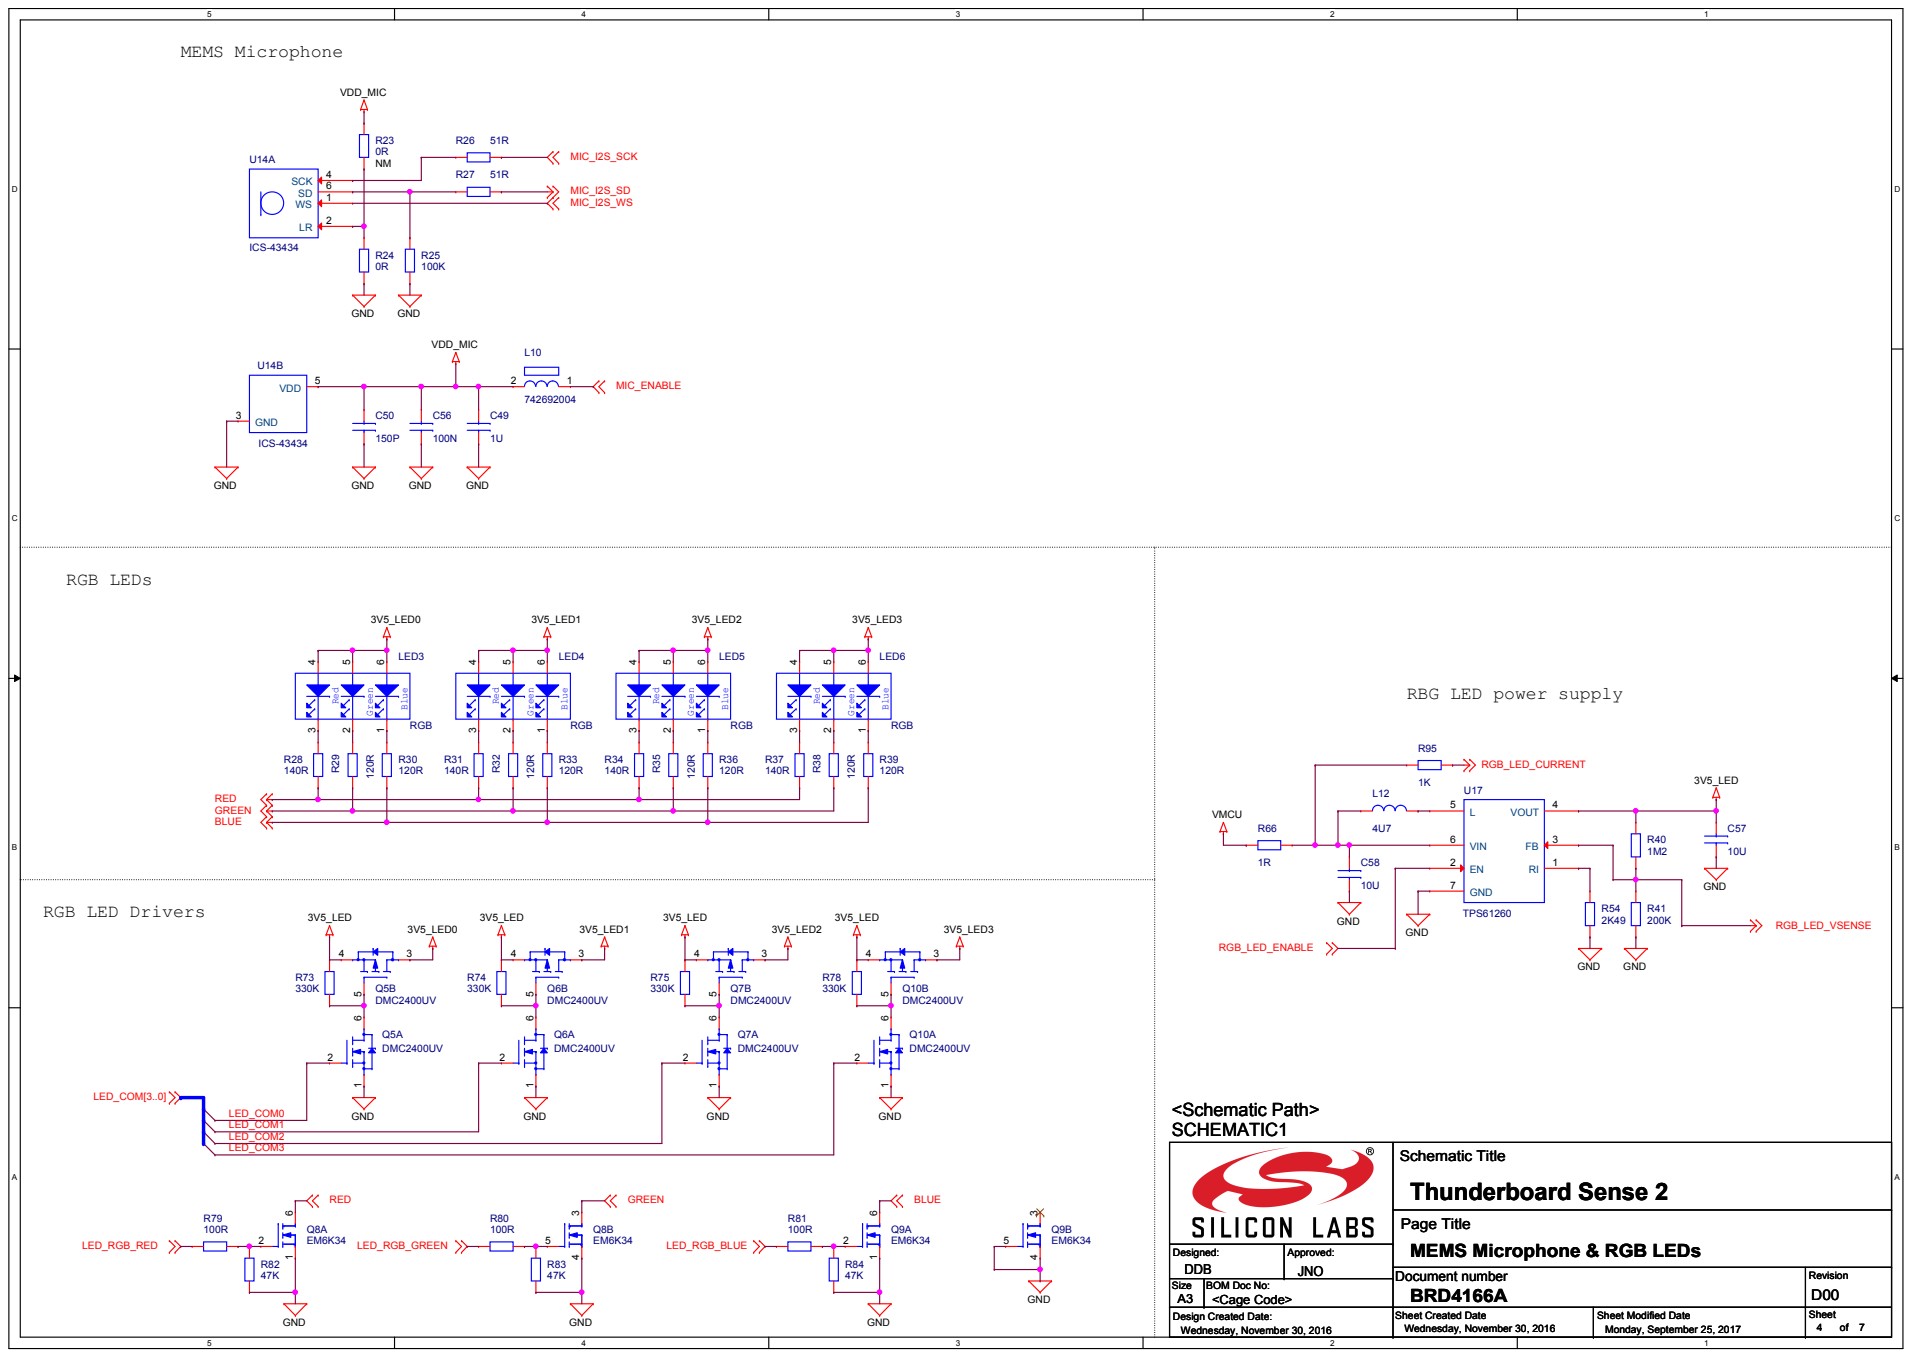
[picture p90: page 4]

RBG LED power supply

Page Title
MEMS Microphone & RGB LEDs

# Hall-effect Sensor

## RH/Temp Sensor

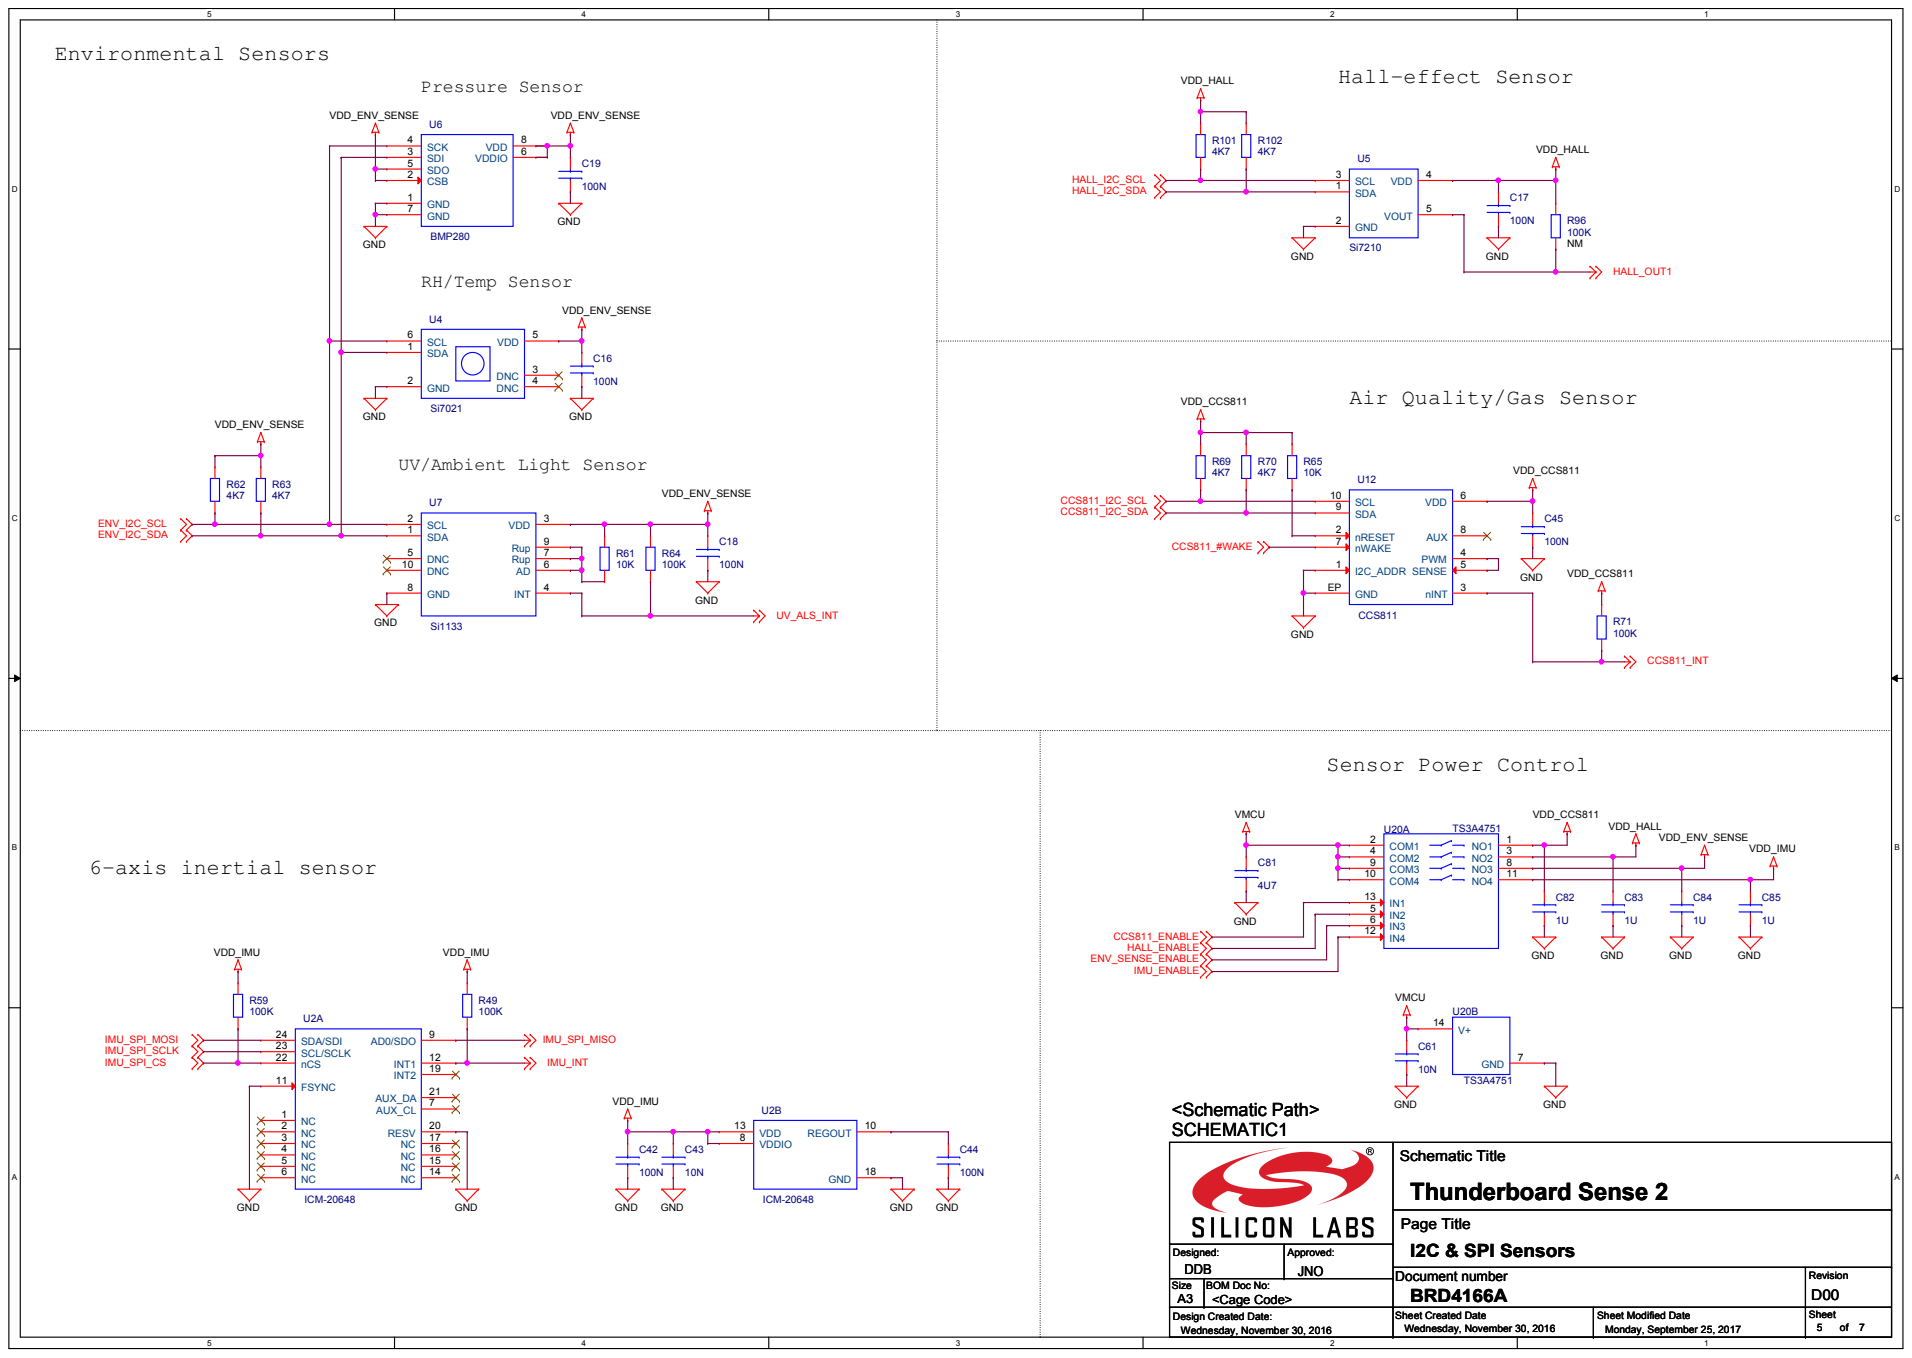
[picture p91: page 5]

Air Quality/Gas Sensor

UV/Ambient Light Sensor

## Debug MCU Connections

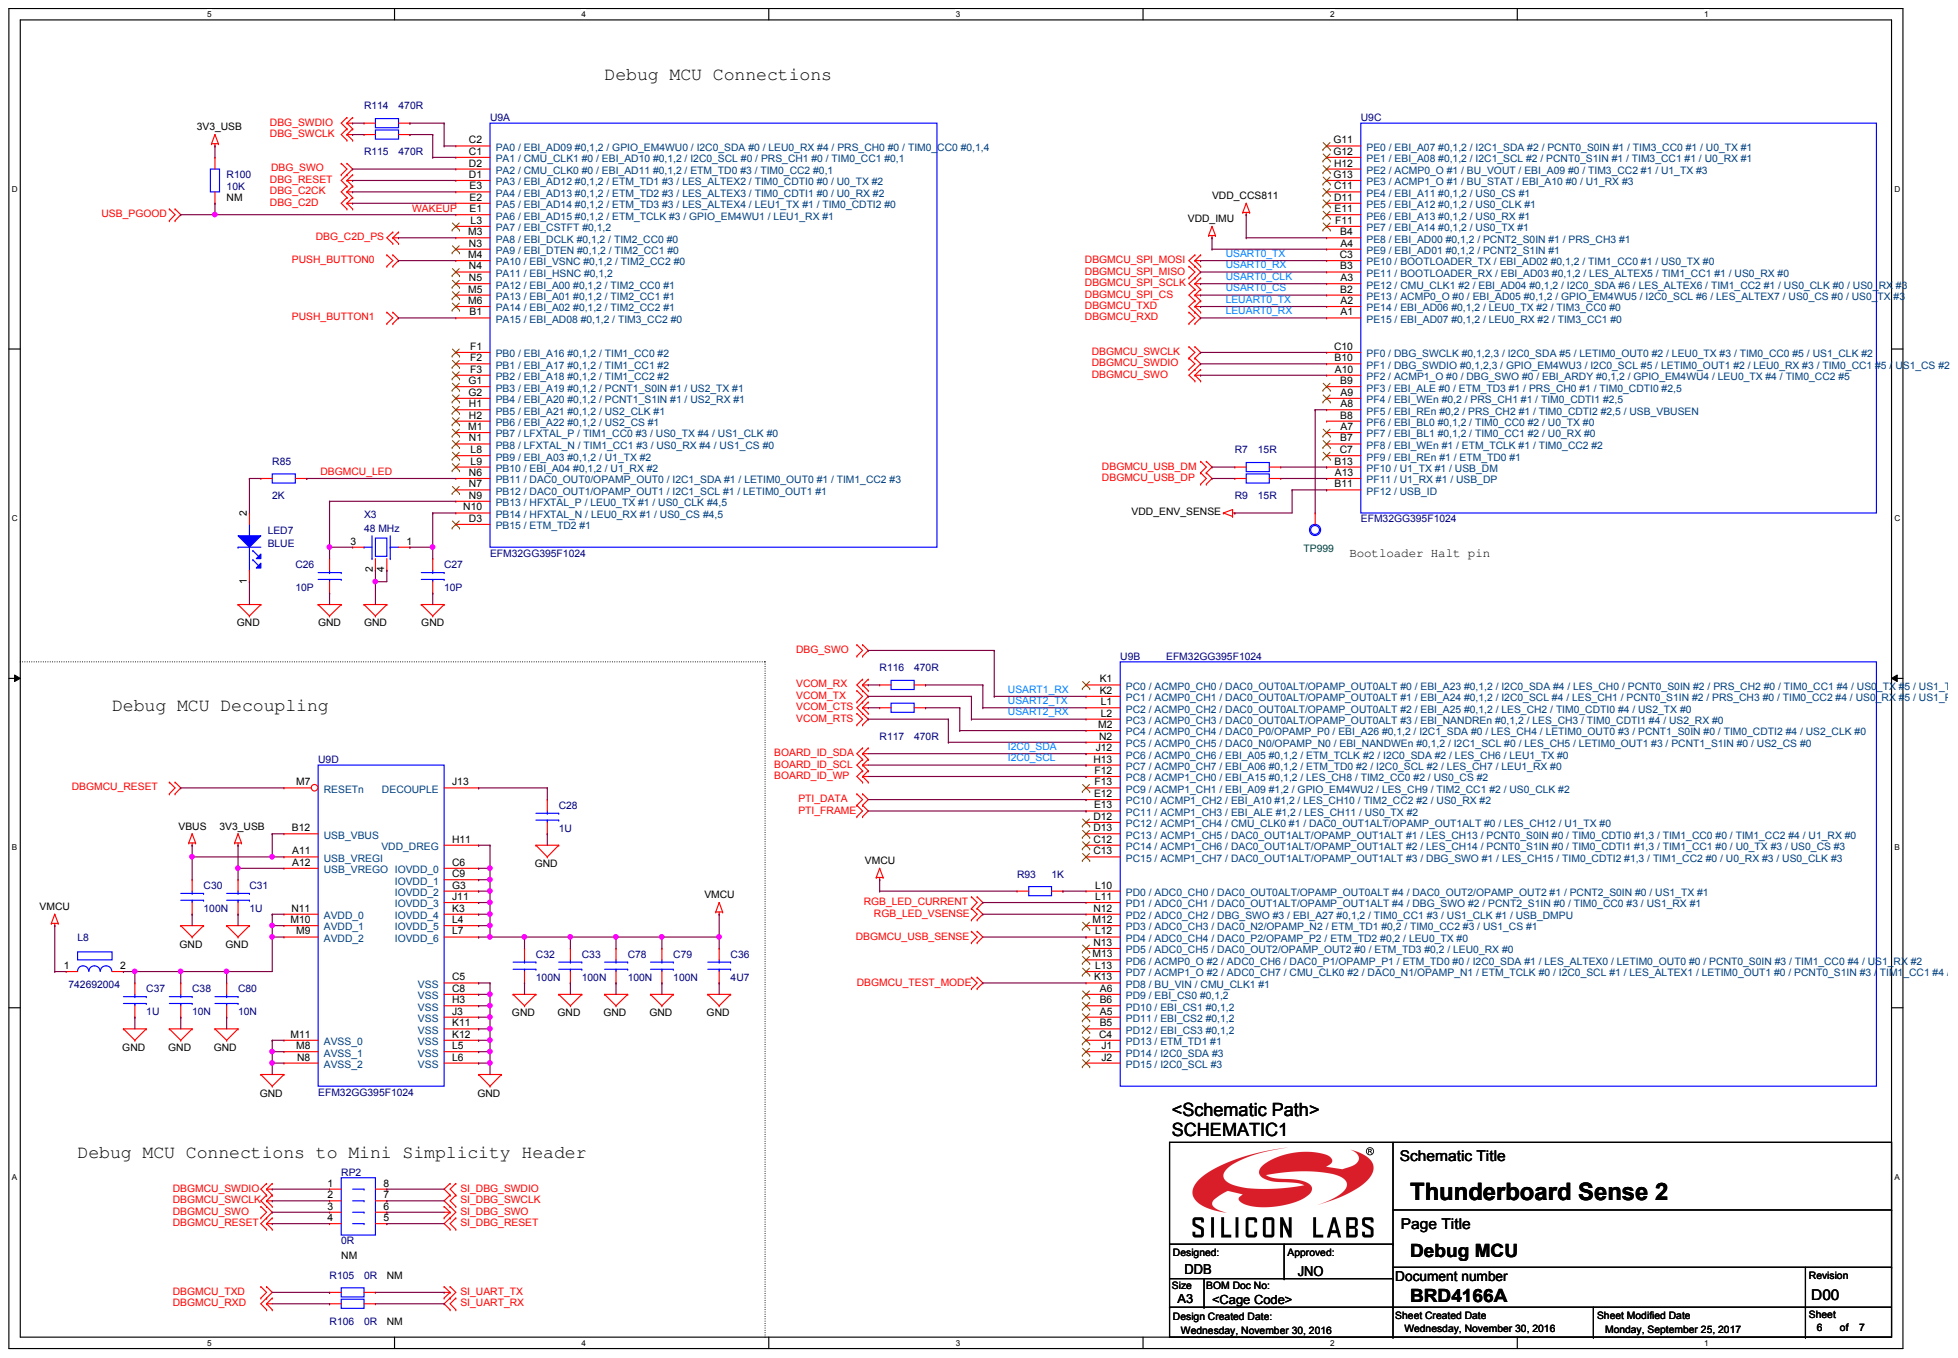
[picture p92: page 6]

Debug MCU Connections to Mini Simplicity Header

## USB Connector

### User can supply 3.6 - 5.5 on

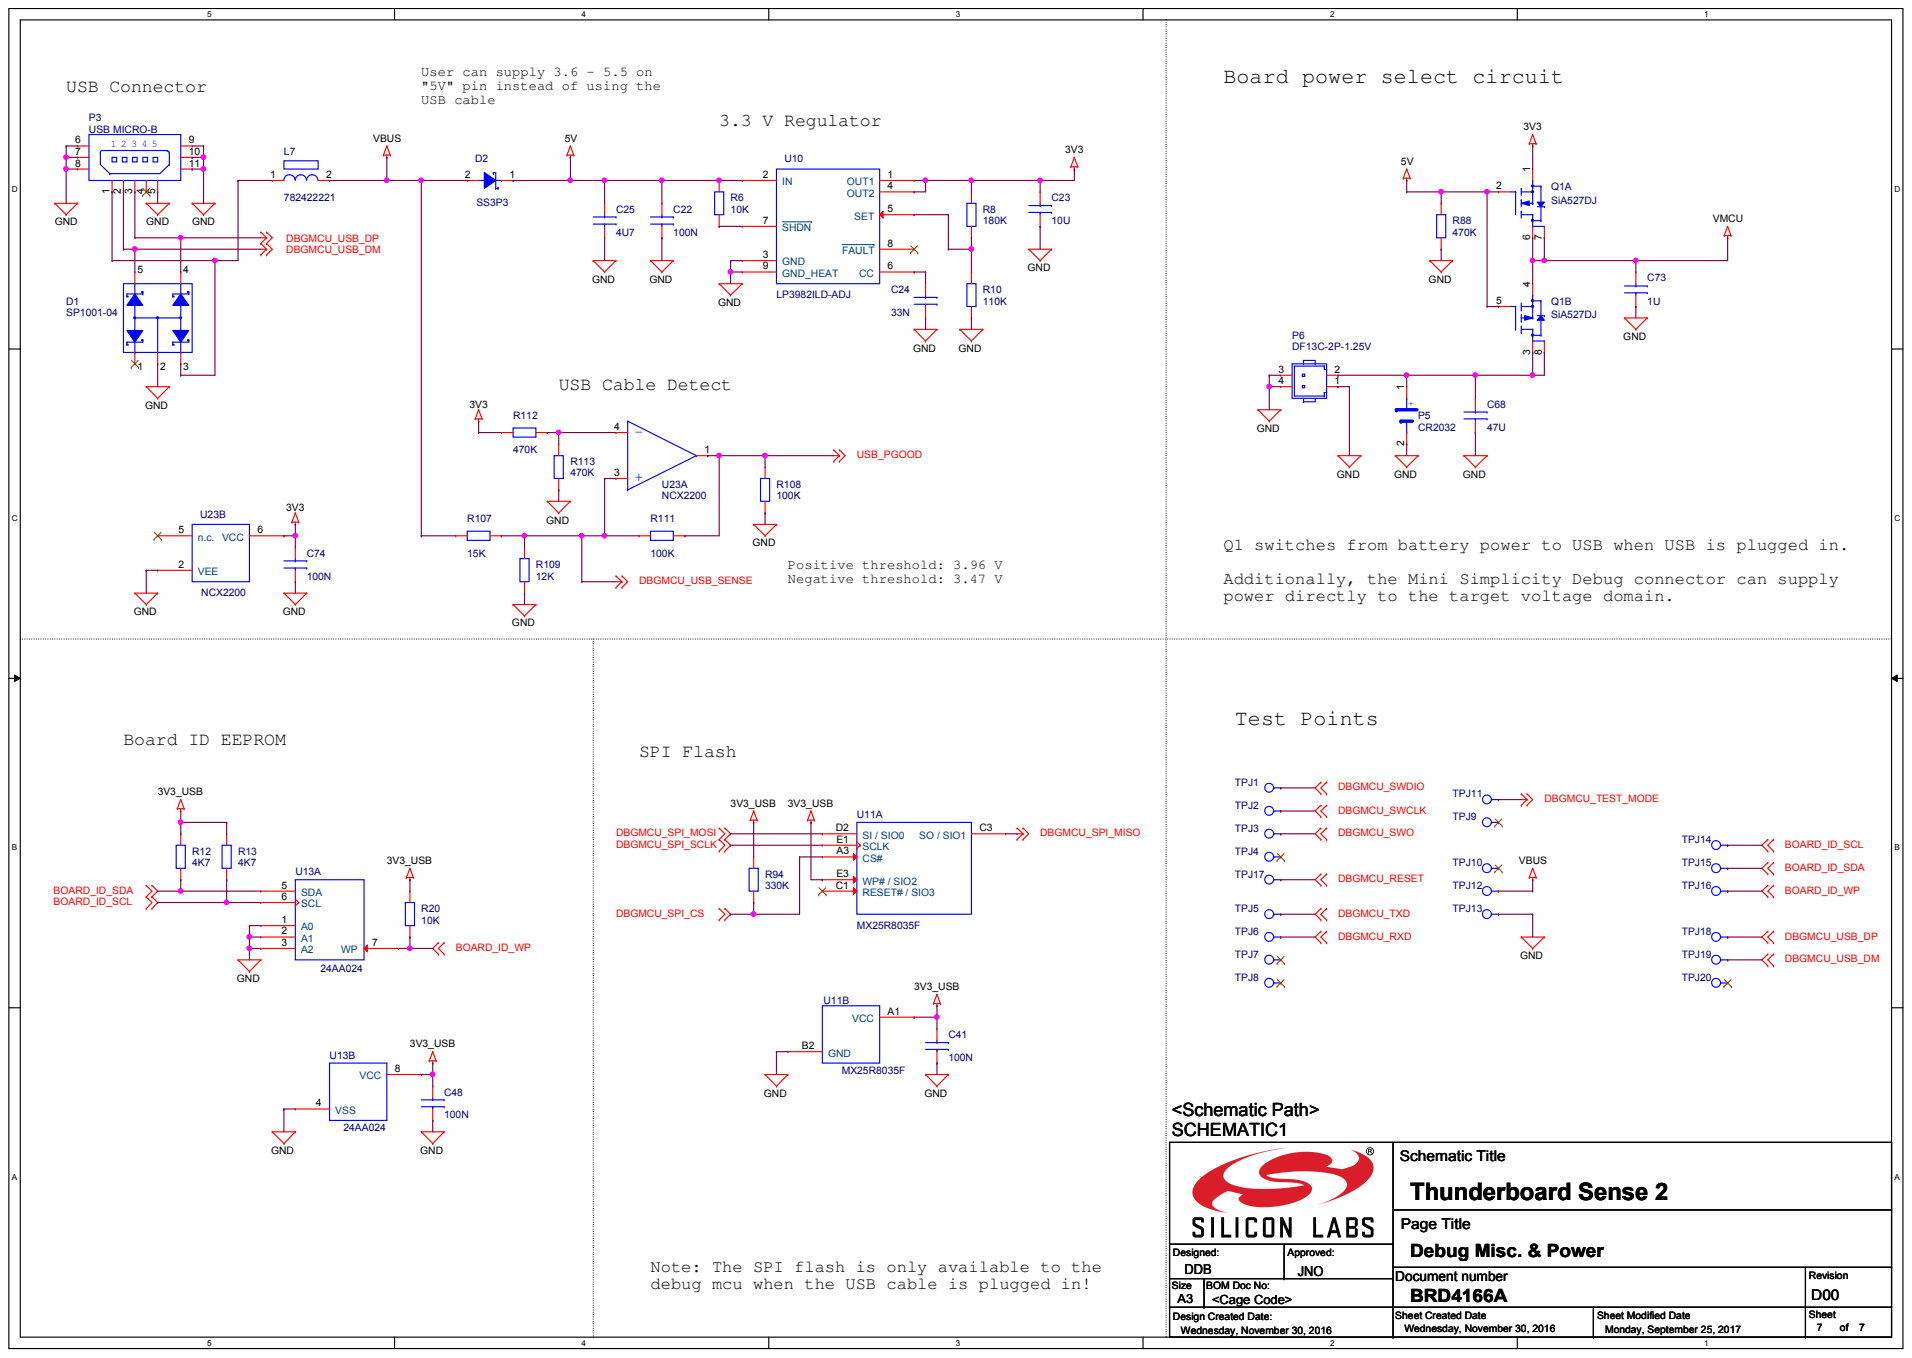
[picture p93: page 7]

"5V" pin instead of using the
USB cable

Board power select circuit

Q1 switches from battery power to USB when USB is plugged in.

Additionally, the Mini Simplicity Debug connector can supply
power directly to the target voltage domain.

Note: The SPI flash is only available to the
debug mcu when the USB cable is plugged in!
