fbradasc/RCTX/doc/EFR32M/Schematics/BRD4170A-A00-schematic.pdf

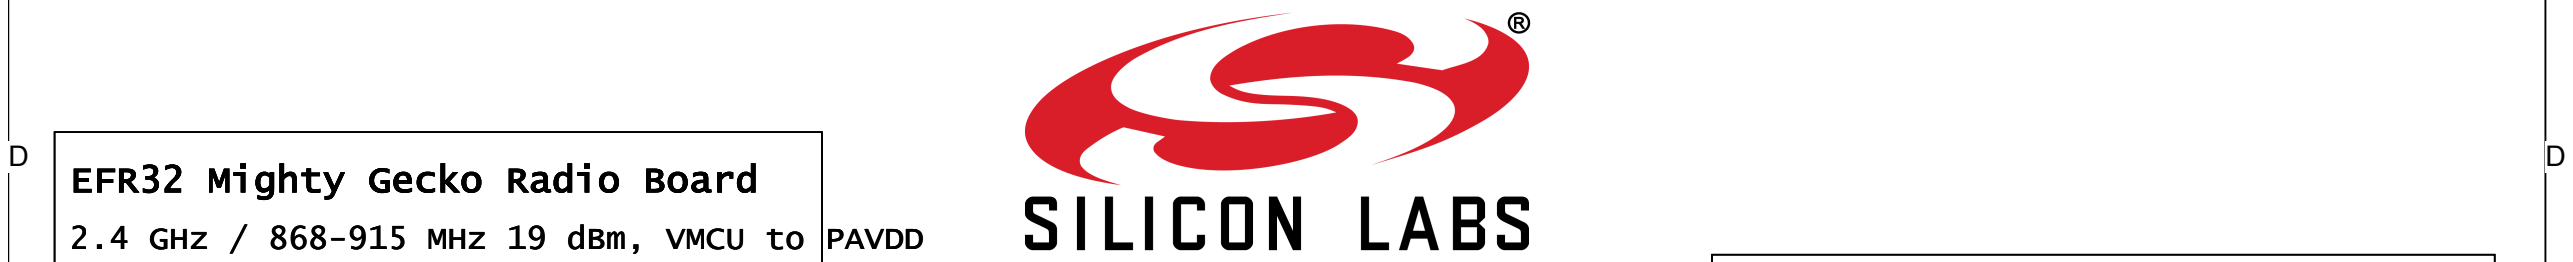
[picture p106: figure]
EFR32 Mighty Gecko Radio Board

C | C
B | B
A | A
WSTK Connectors & Board ID | 4

# EFR32 Signal Assignments

Board Function | Page
| 1
| 2
| 3

# RF, Antenna & Power

# Title Page

# Revision History

Rev. | Description
A00 | Initial revision.

# 2.4 GHz / 868-915 MHz 19 dBm, VMCU to PAVDD

Size

Designed:

Revision

Sheet
of

Approved:

Sheet Created Date | Sheet Modified Date

## Document number

## Schematic Title

Design Created Date:

BOM Doc No:

## Page Title

BRD4170A | A00
Friday, July 28, 2017 | 1 | 4

A3

TAB | DDB

# EFR32MG12 WSTK Radio Board

### <Cage Code>

Monday, April 02, 2012 | Monday, April 02, 2012

# SCHEMATIC1

# <Schematic Path>

# Title Page

Designed:

Approved:

## Schematic Title

## Page Title

Friday, July 28, 2017 | 1 | 4
TAB | DDB

# EFR32MG12 WSTK Radio Board

Monday, April 02, 2012 | Monday, April 02, 2012

# SCHEMATIC1

# <Schematic Path>

# Title Page

Designed:

Approved:

## Schematic Title

## Page Title

Friday, July 28, 2017 | 1 | 4
TAB | DDB

# EFR32MG12 WSTK Radio Board

Monday, April 02, 2012 | Monday, April 02, 2012

# SCHEMATIC1

# <Schematic Path>

# Title Page

PCB1

PCB4170A

# Antenna & Radio Interface

## High Frequency

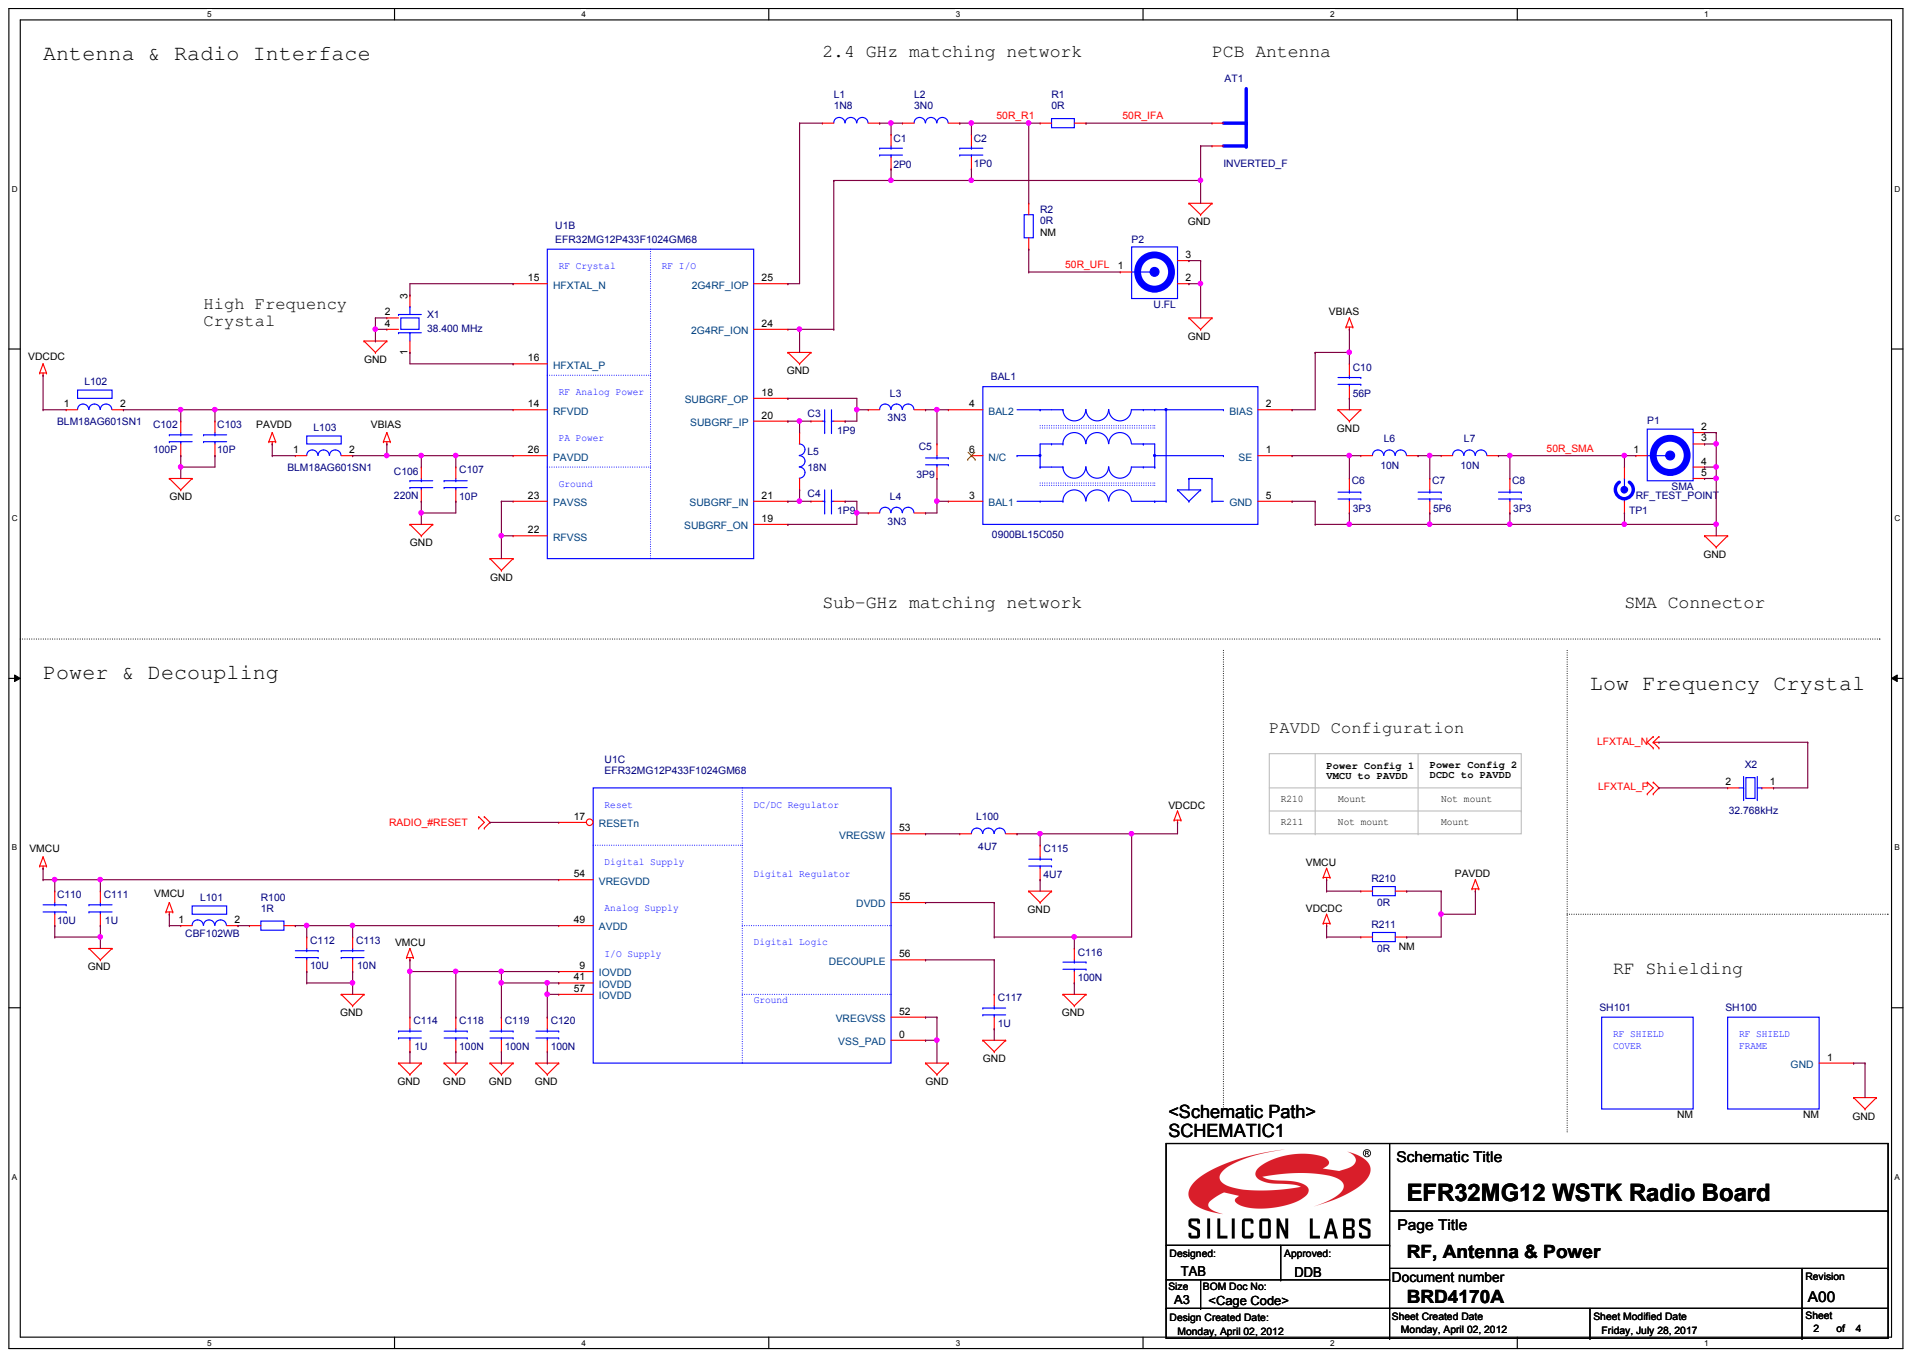
[picture p107: page 2]

Sub-GHz matching network

EFR32 Pin Mapping | EFR32 I/O Port Pins
EFR32 Pin | EFR32 Peripheral

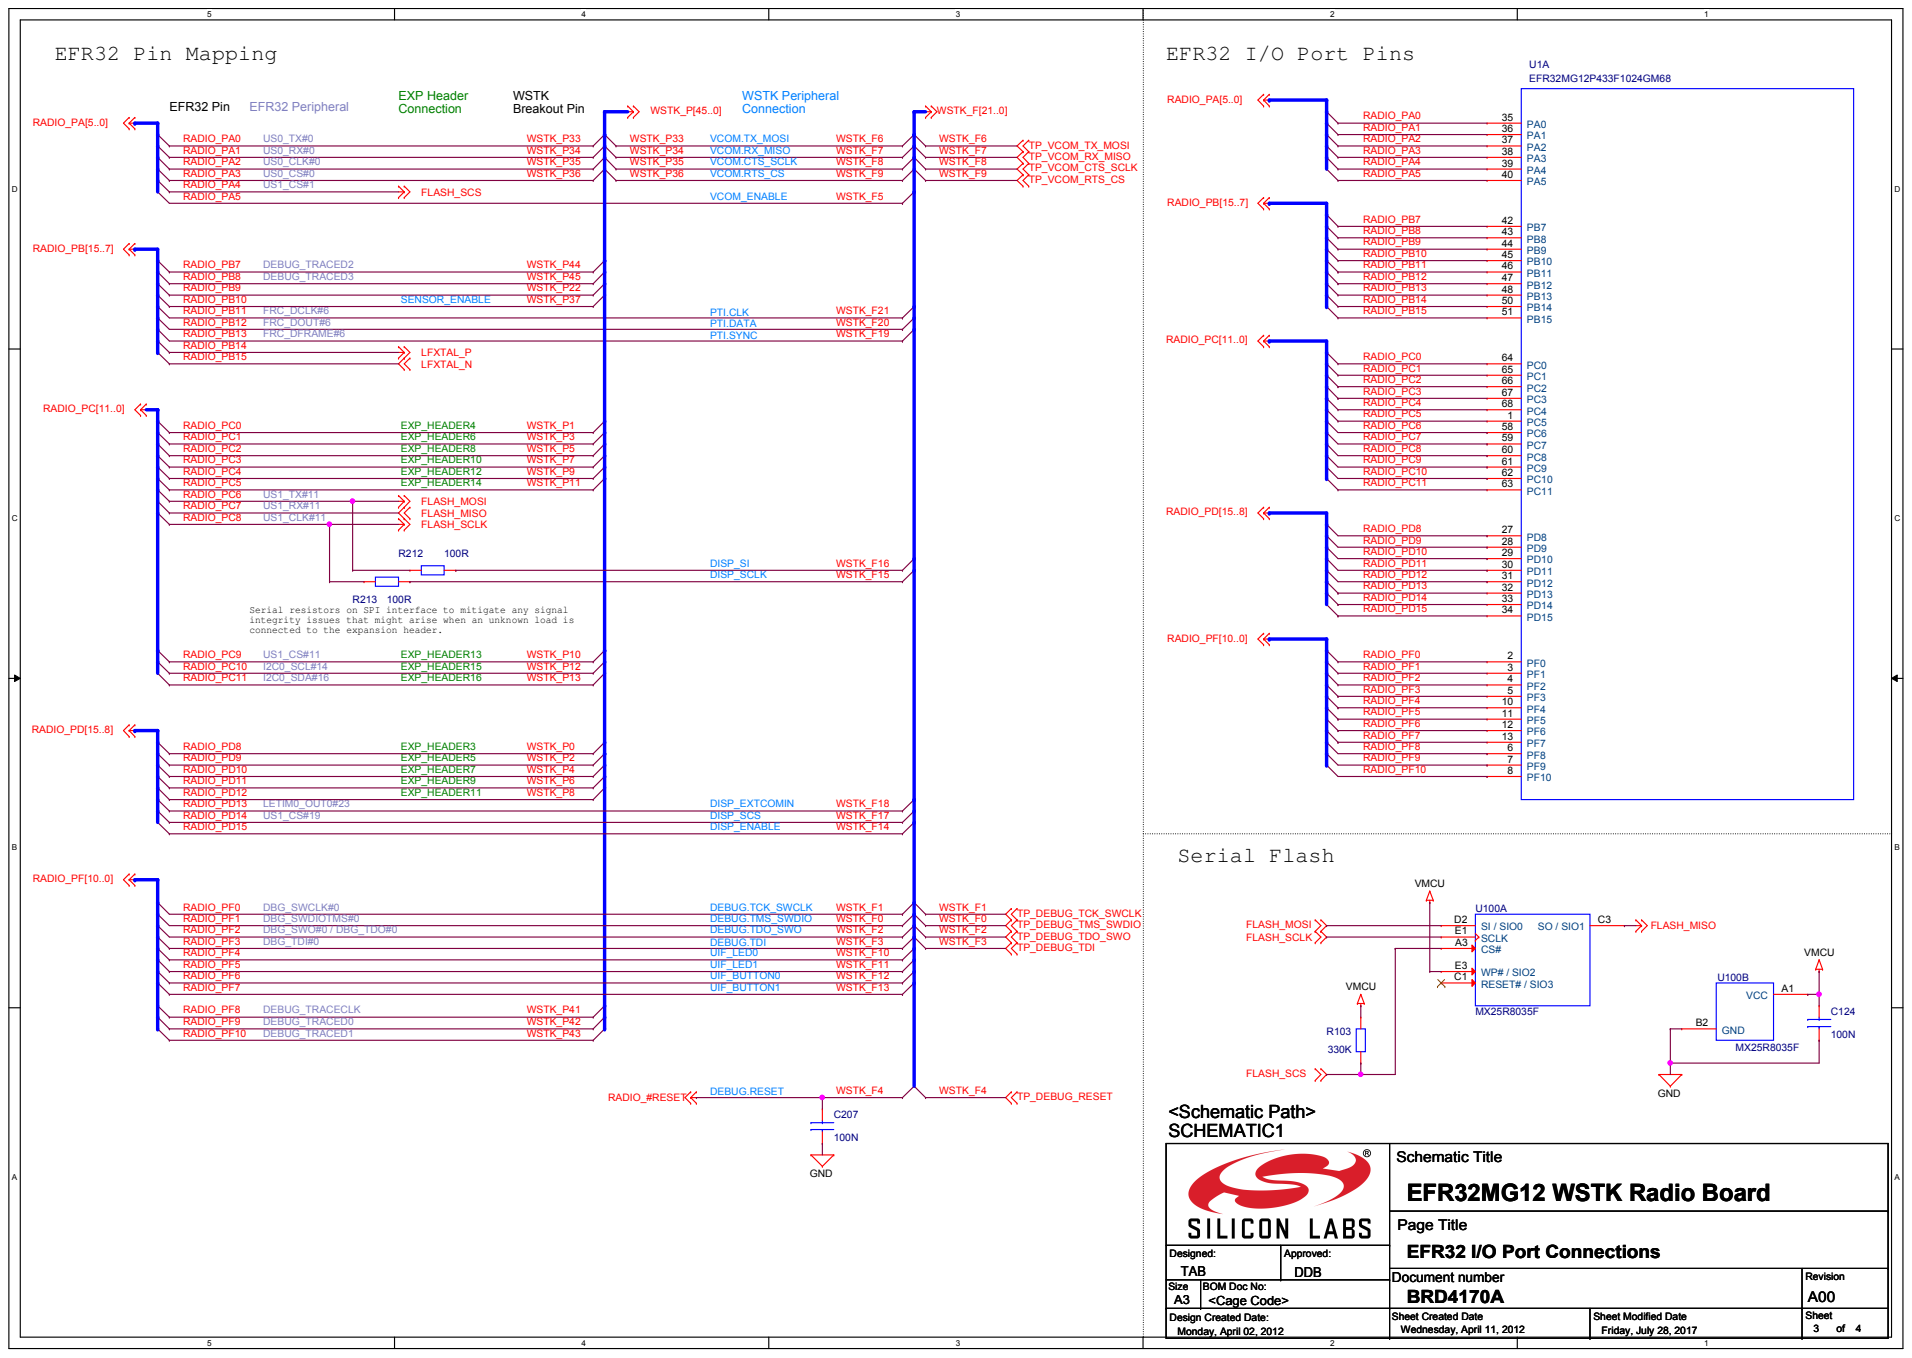
[picture p108: page 3]

Serial resistors on SPI interface to mitigate any signal
integrity issues that might arise when an unknown load is
connected to the expansion header.

# WSTK Connectors

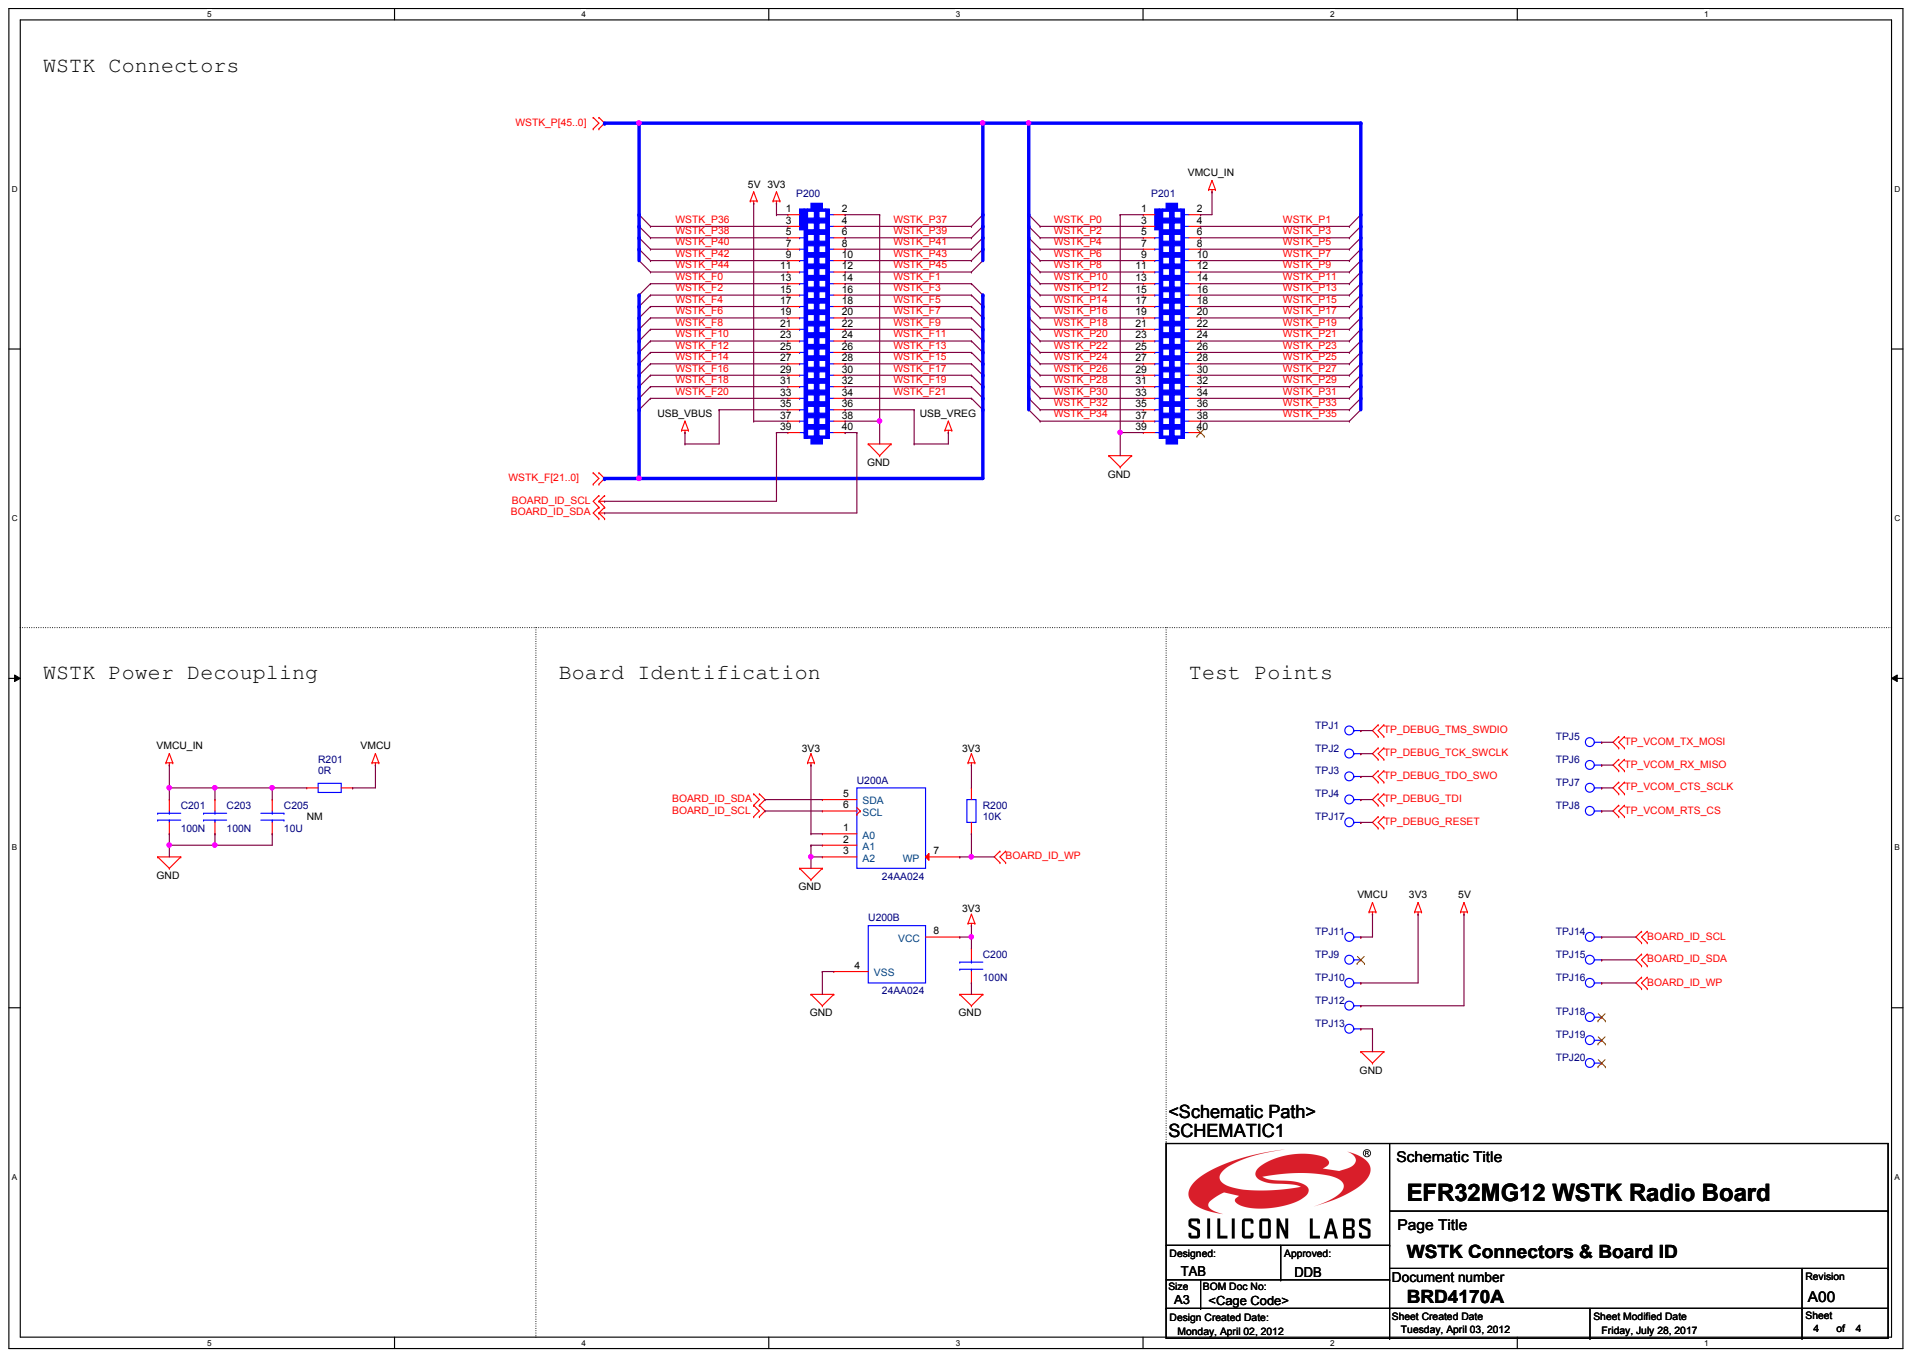
[picture p109: page 4]

Page Title
WSTK Connectors & Board ID
