fbradasc/RCTX/doc/EFR32M/Schematics/BRD4172B-A00-169MHz-schematic.pdf

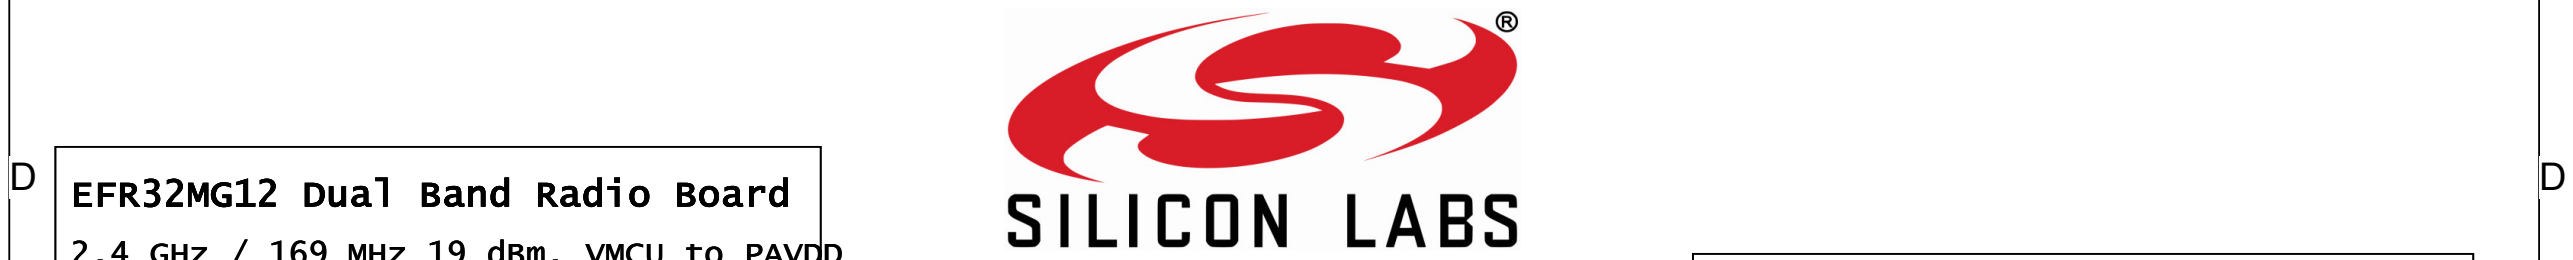
[picture p117: figure]
EFR32MG12 Dual Band Radio Board

C | C
B | B
A | A
WSTK Connectors & Board ID | 4

# EFR32 Signal Assignments

Board Function | Page
| 1
| 2
| 3

# RF, Antenna & Power

# Title Page

Size

Designed:

Revision

Sheet
of

Approved:

Sheet Created Date | Sheet Modified Date

## Document number

## Schematic Title

Design Created Date:

BOM Doc No:

## Page Title

BRD4172B | A00
Tuesday, March 13, 2018 | 1 | 4

A3

<OrgAddr1> | <OrgAddr2>

# EFR32MG12 Dual Band 2400/169 MHz Radio Board

### <Cage Code>

Friday, November 03, 2017 | Friday, November 03, 2017

# SCHEMATIC1

# Title Page

Designed:

Approved:

## Schematic Title

## Page Title

Tuesday, March 13, 2018 | 1 | 4
<OrgAddr1> | <OrgAddr2>

# EFR32MG12 Dual Band 2400/169 MHz Radio Board

# SCHEMATIC1

# Title Page

Designed:

Approved:

## Schematic Title

## Page Title

Tuesday, March 13, 2018 | 1 | 4
<OrgAddr1> | <OrgAddr2>

# EFR32MG12 Dual Band 2400/169 MHz Radio Board

# SCHEMATIC1

# Title Page

# 2.4 GHz / 169 MHz 19 dBm, VMCU to PAVDD

# Revision History

Rev. | Description
A00 | Initial revision.

PCB1

PCB4172B

# Antenna & Radio Interface

## High Frequency

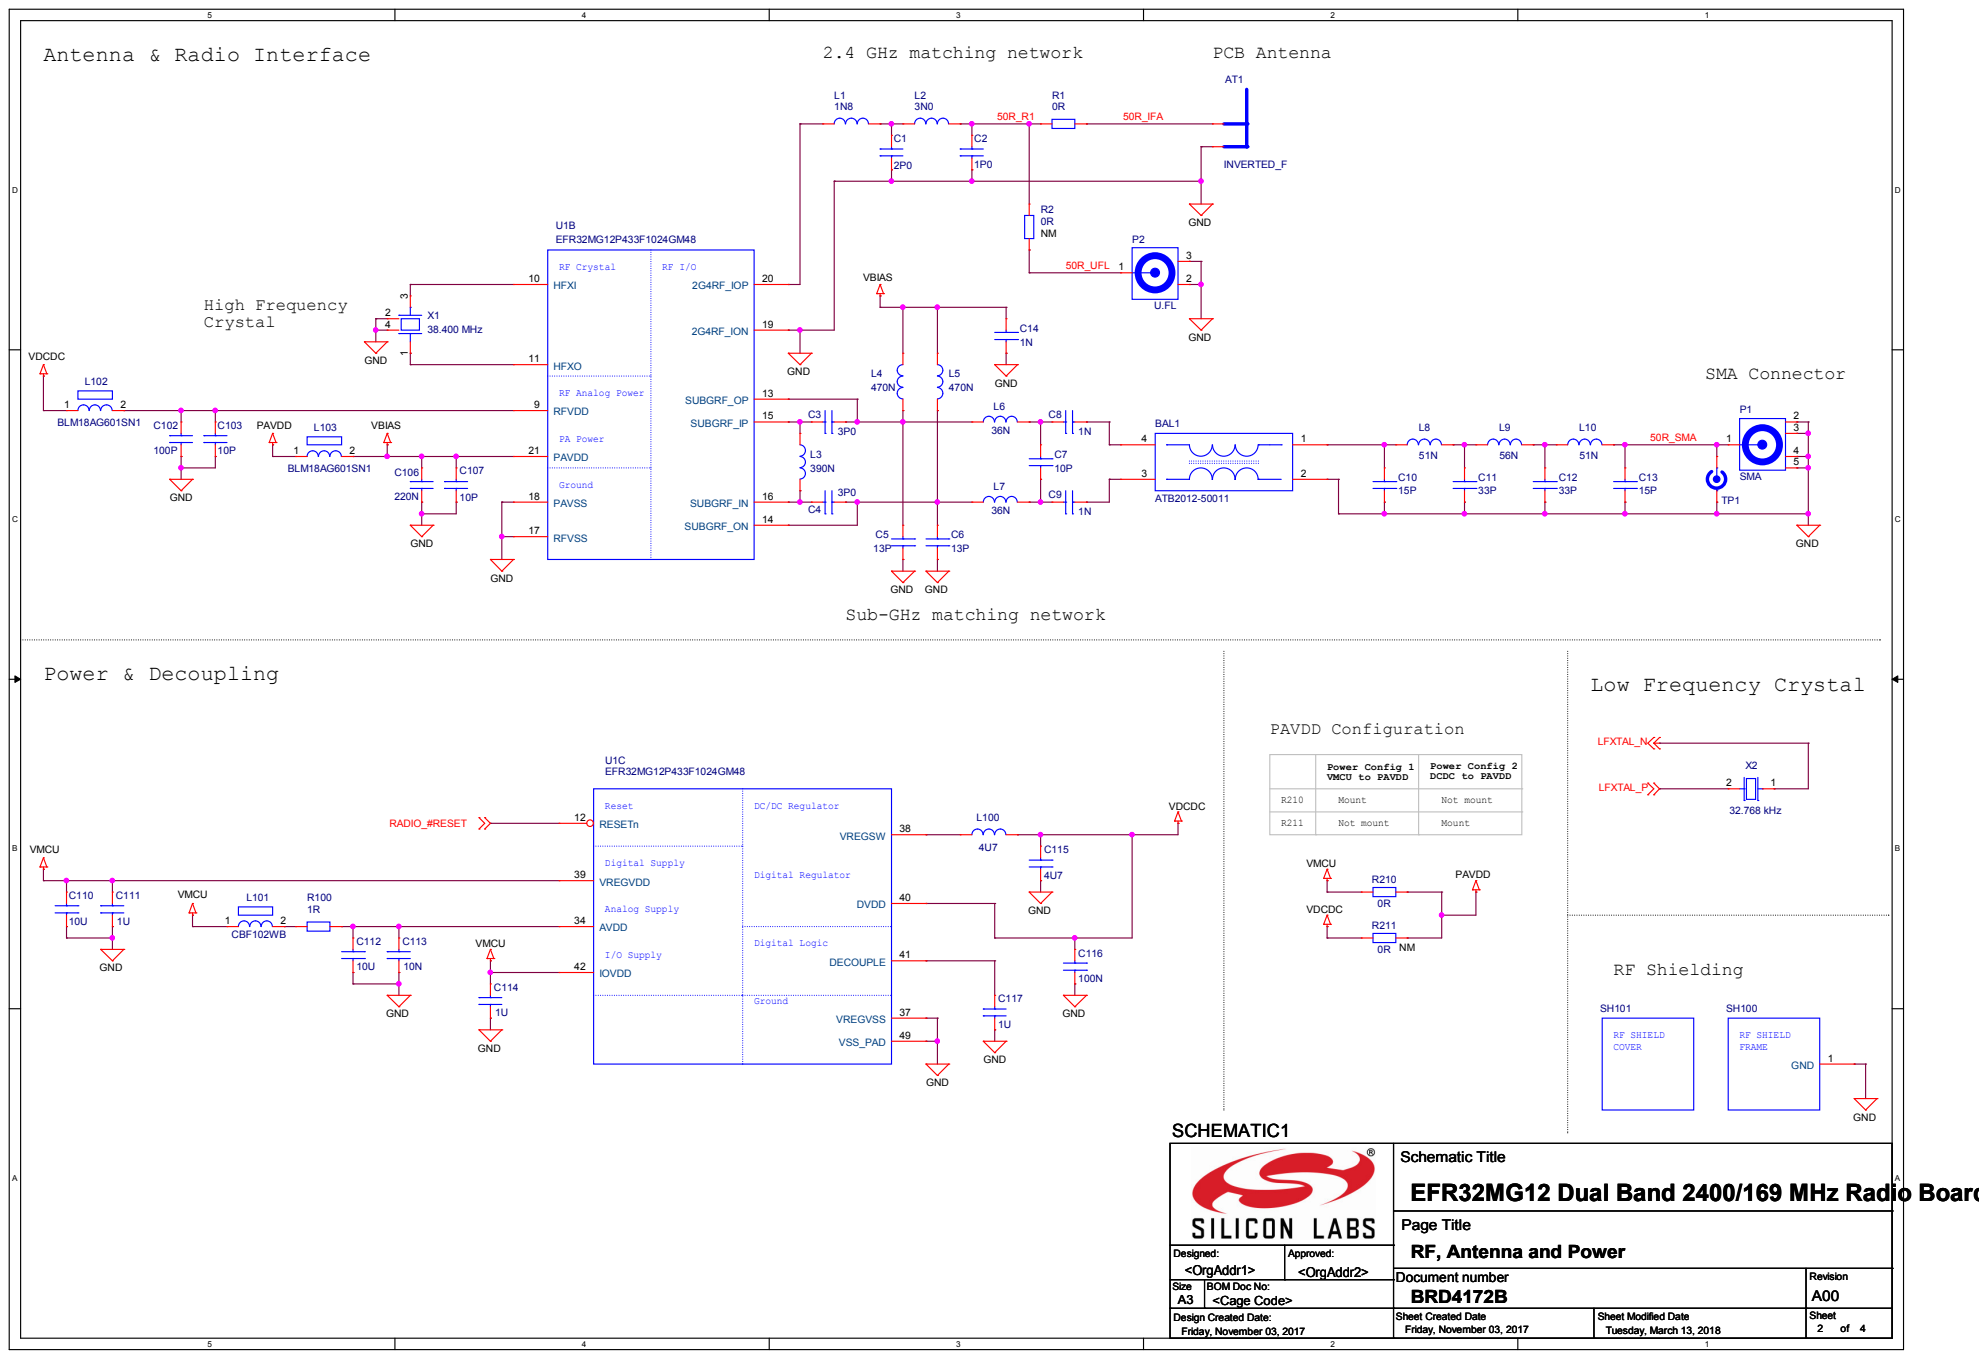
[picture p118: page 2]

Sub-GHz matching network

Schematic Title
EFR32MG12 Dual Band 2400/169 MHz Radio Board

Page Title
RF, Antenna and Power

# Pin Mapping

# I/O Port Pins

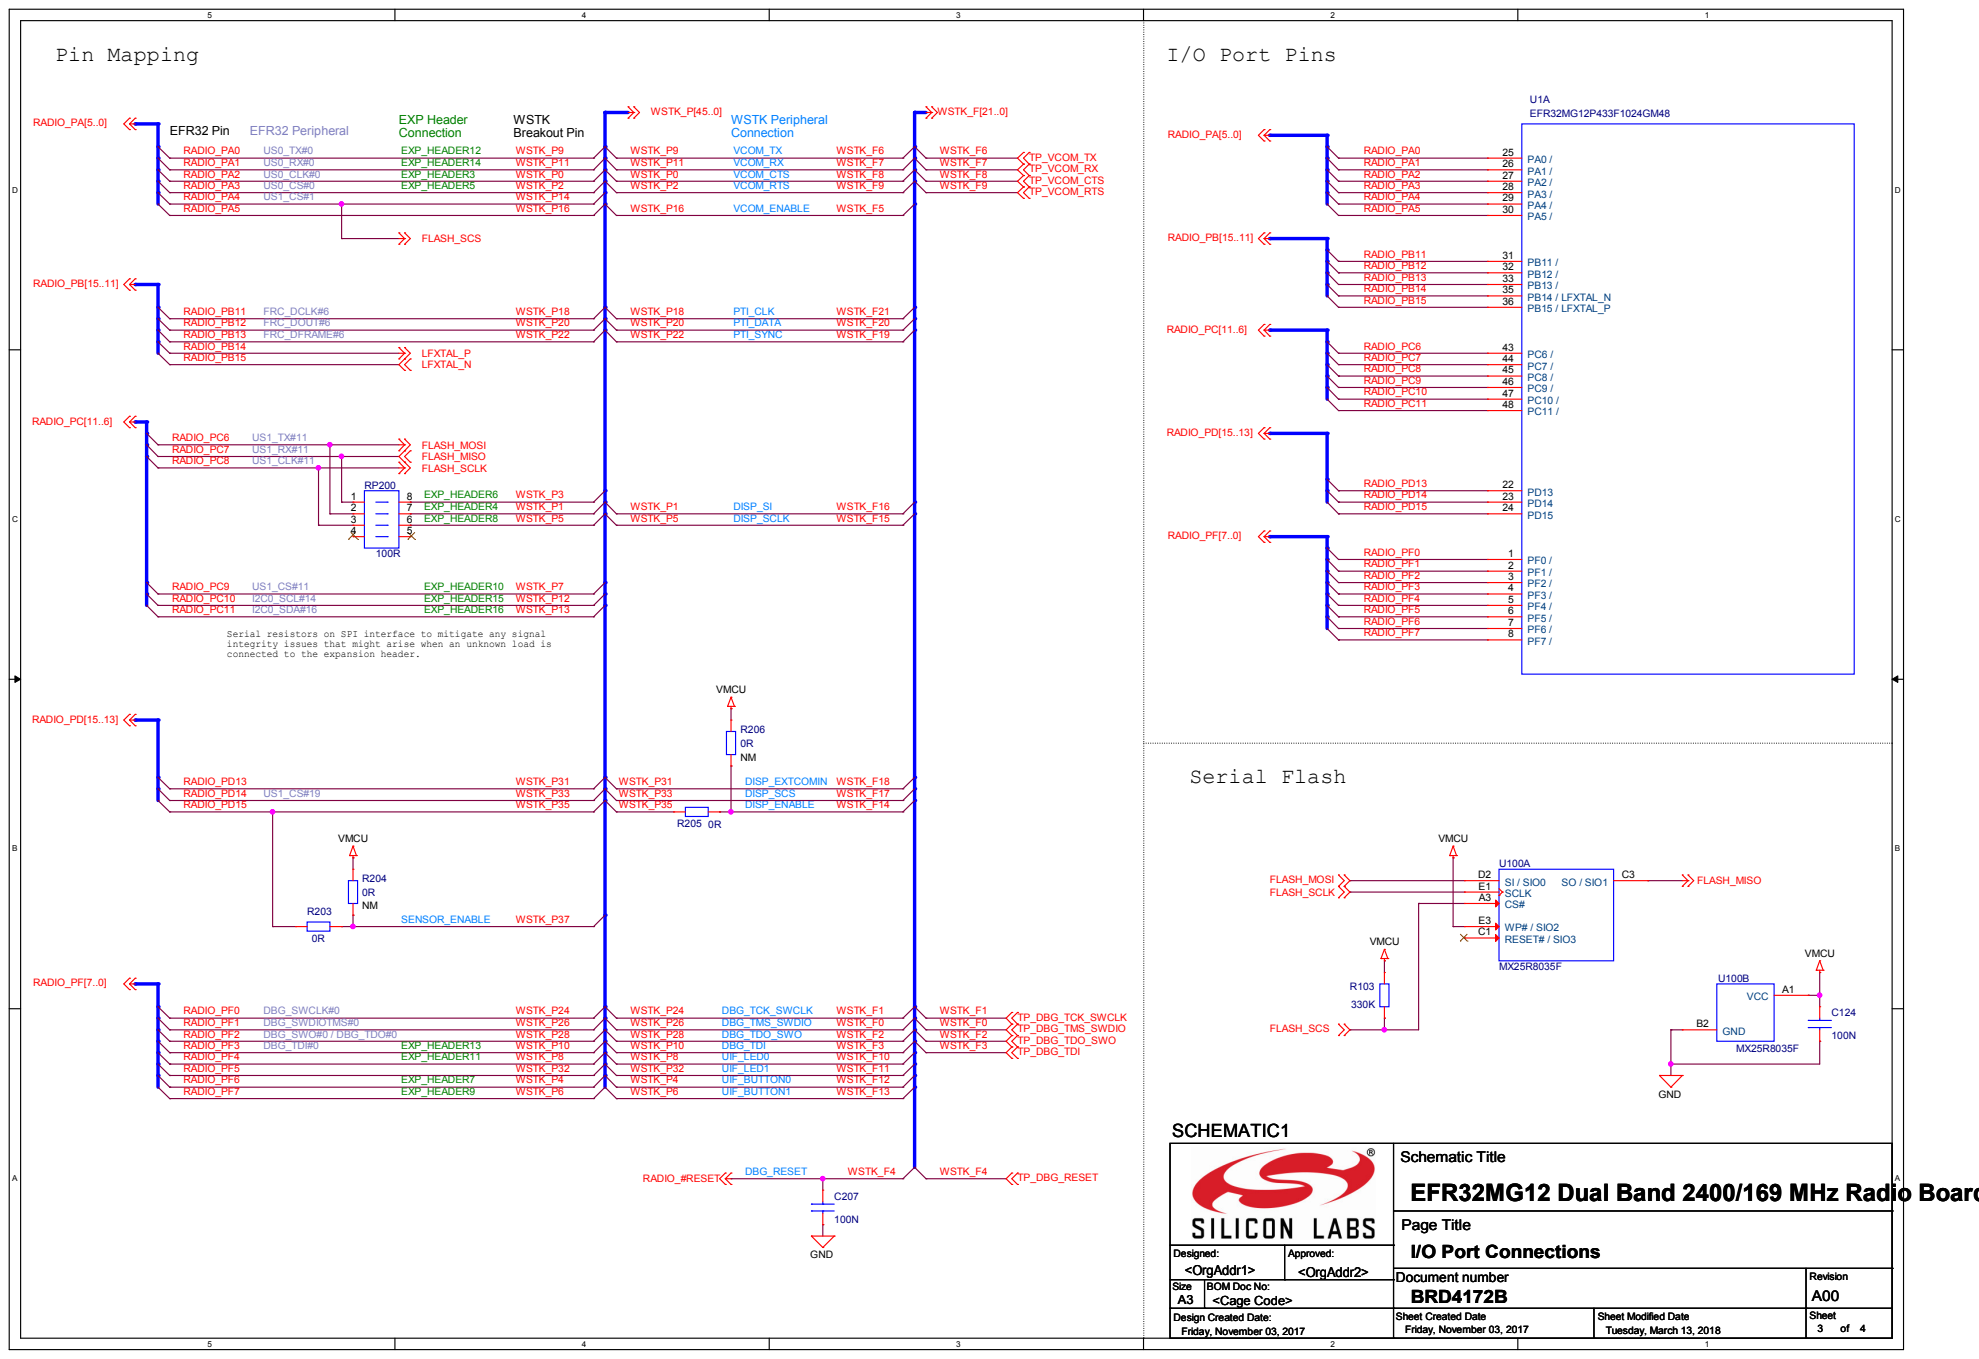
[picture p119: page 3]

Serial resistors on SPI interface to mitigate any signal
integrity issues that might arise when an unknown load is
connected to the expansion header.

Schematic Title
EFR32MG12 Dual Band 2400/169 MHz Radio Board

# WSTK Connectors

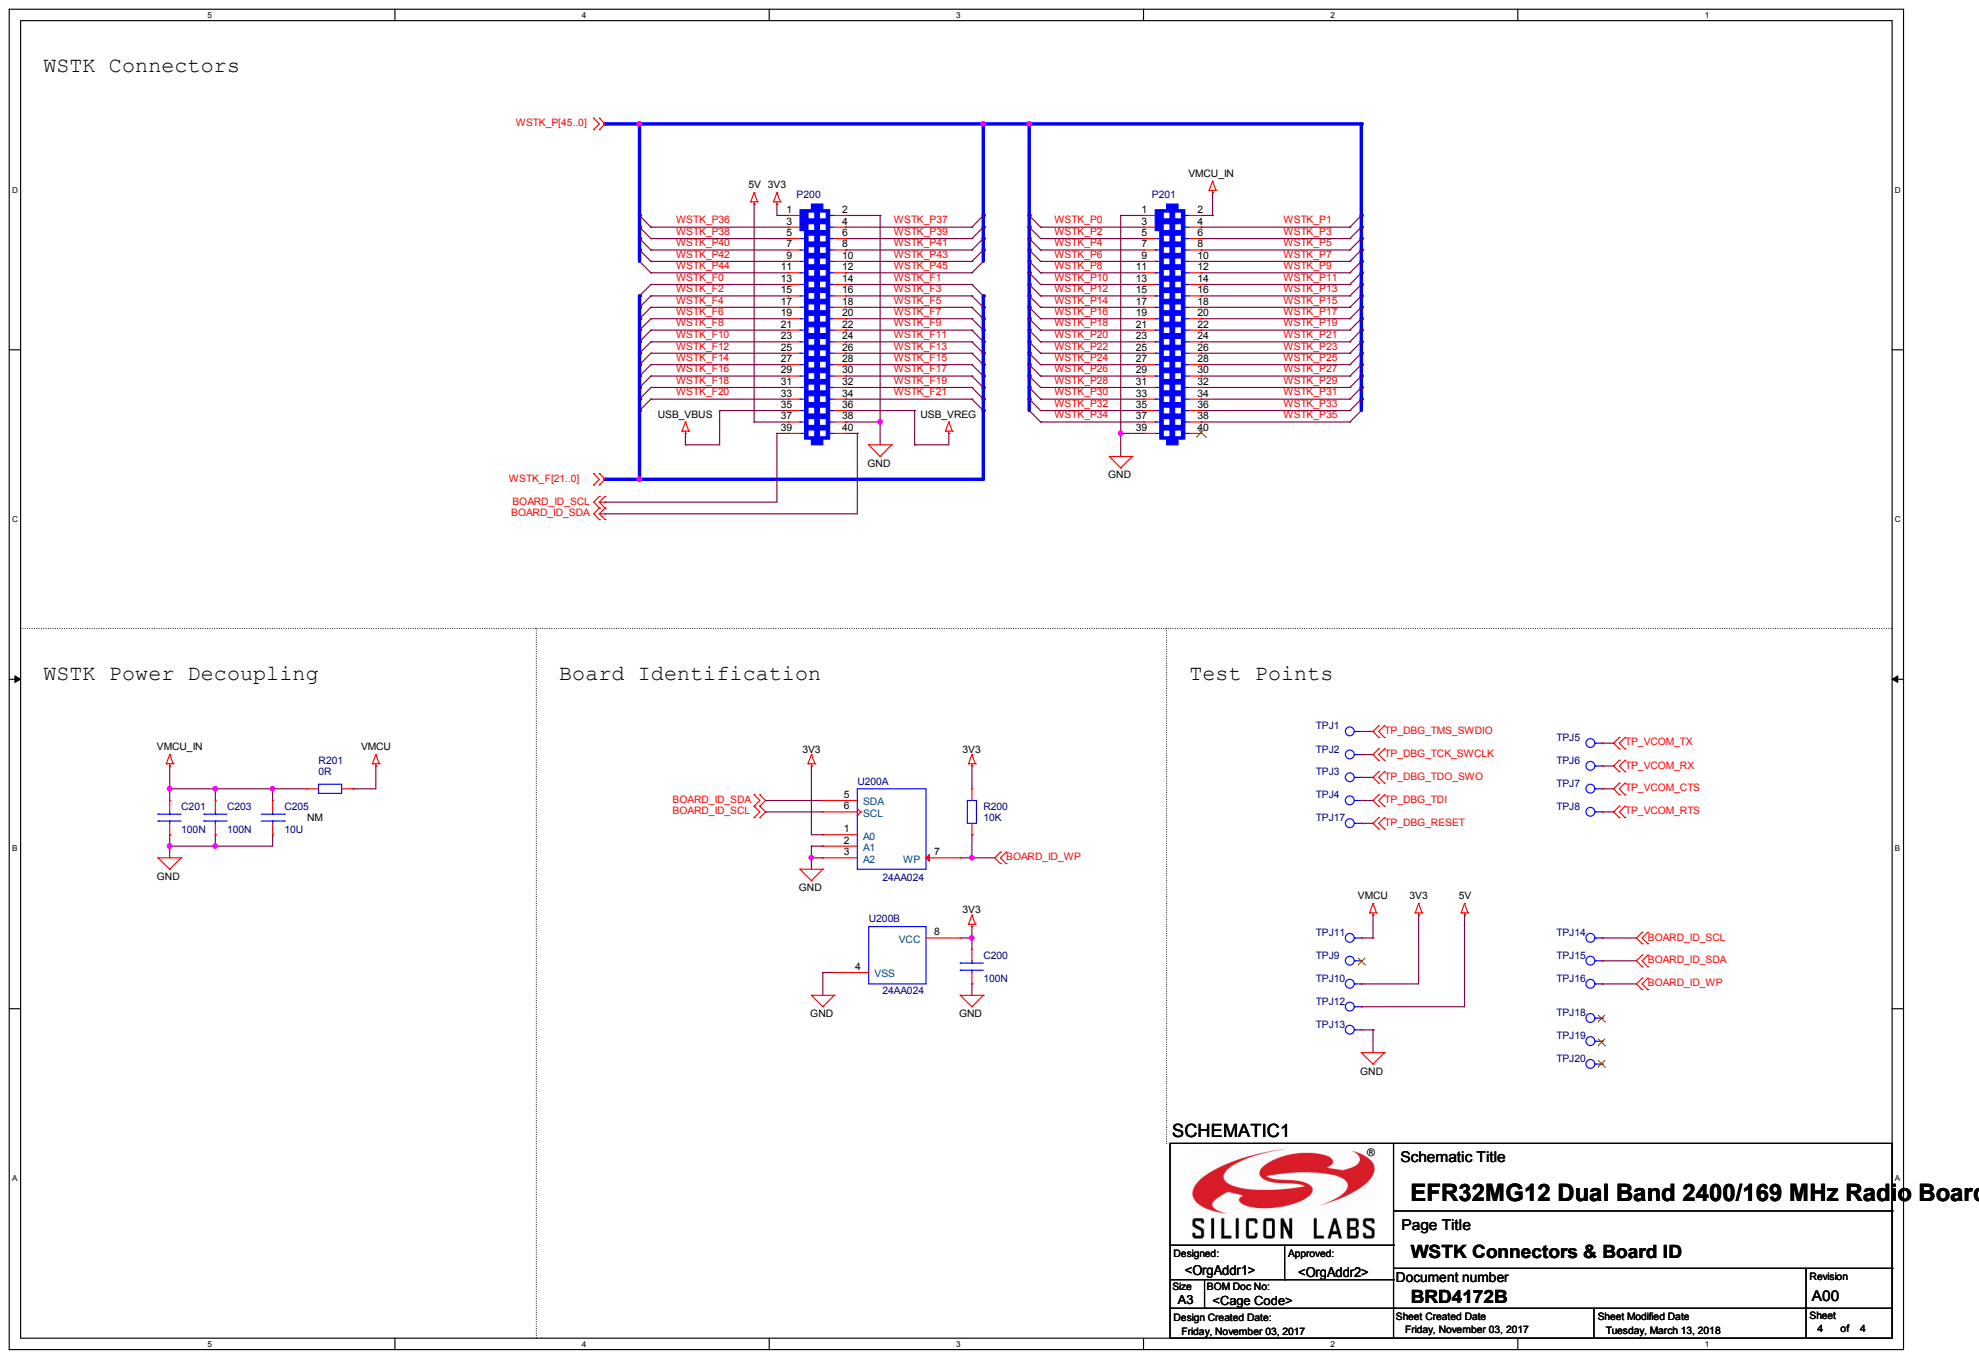
[picture p120: page 4]

Schematic Title
EFR32MG12 Dual Band 2400/169 MHz Radio Board

Page Title
WSTK Connectors & Board ID
