fbradasc/RCTX/doc/EFR32M/Schematics/BRD4304A-A00-schematic.pdf

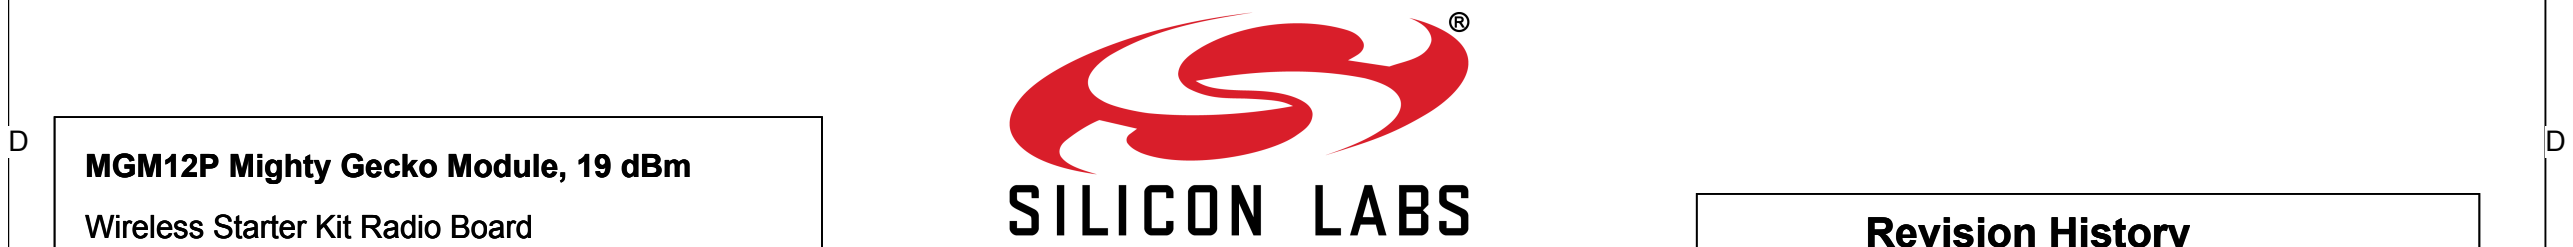
[picture p125: figure]
MGM12P Mighty Gecko Module, 19 dBm

C | C
B | B
A | A
WSTK Connectors & Board ID | 3
Board Function | Page
| 1
Module | 2

# Title Page

Size

Designed:

Revision

Sheet
of

Approved:

Sheet Created Date | Sheet Modified Date

## Document number

## Schematic Title

Design Created Date:

BOM Doc No:

## Page Title

BRD4304A | A00
Wednesday, January 11, 2017 | 1 | 3

A3

DDB | JNO

# MGM12P Module Carrier Board

### <Cage Code>

Monday, April 02, 2012 | Monday, April 02, 2012

# SCHEMATIC1

# <Schematic Path>

# Title Page

Designed:

Approved:

## Schematic Title

## Page Title

Wednesday, January 11, 2017 | 1 | 3
DDB | JNO

# MGM12P Module Carrier Board

Monday, April 02, 2012 | Monday, April 02, 2012

# SCHEMATIC1

# <Schematic Path>

# Title Page

Designed:

Approved:

## Schematic Title

## Page Title

Wednesday, January 11, 2017 | 1 | 3
DDB | JNO

# MGM12P Module Carrier Board

Monday, April 02, 2012 | Monday, April 02, 2012

# SCHEMATIC1

# <Schematic Path>

# Title Page

Wireless Starter Kit Radio Board | Revision History
Rev. | Description
A00 | Initial release.

PCB1

PCB4304A

# Module Footprint

Additional Connections | Reset input from mainboard

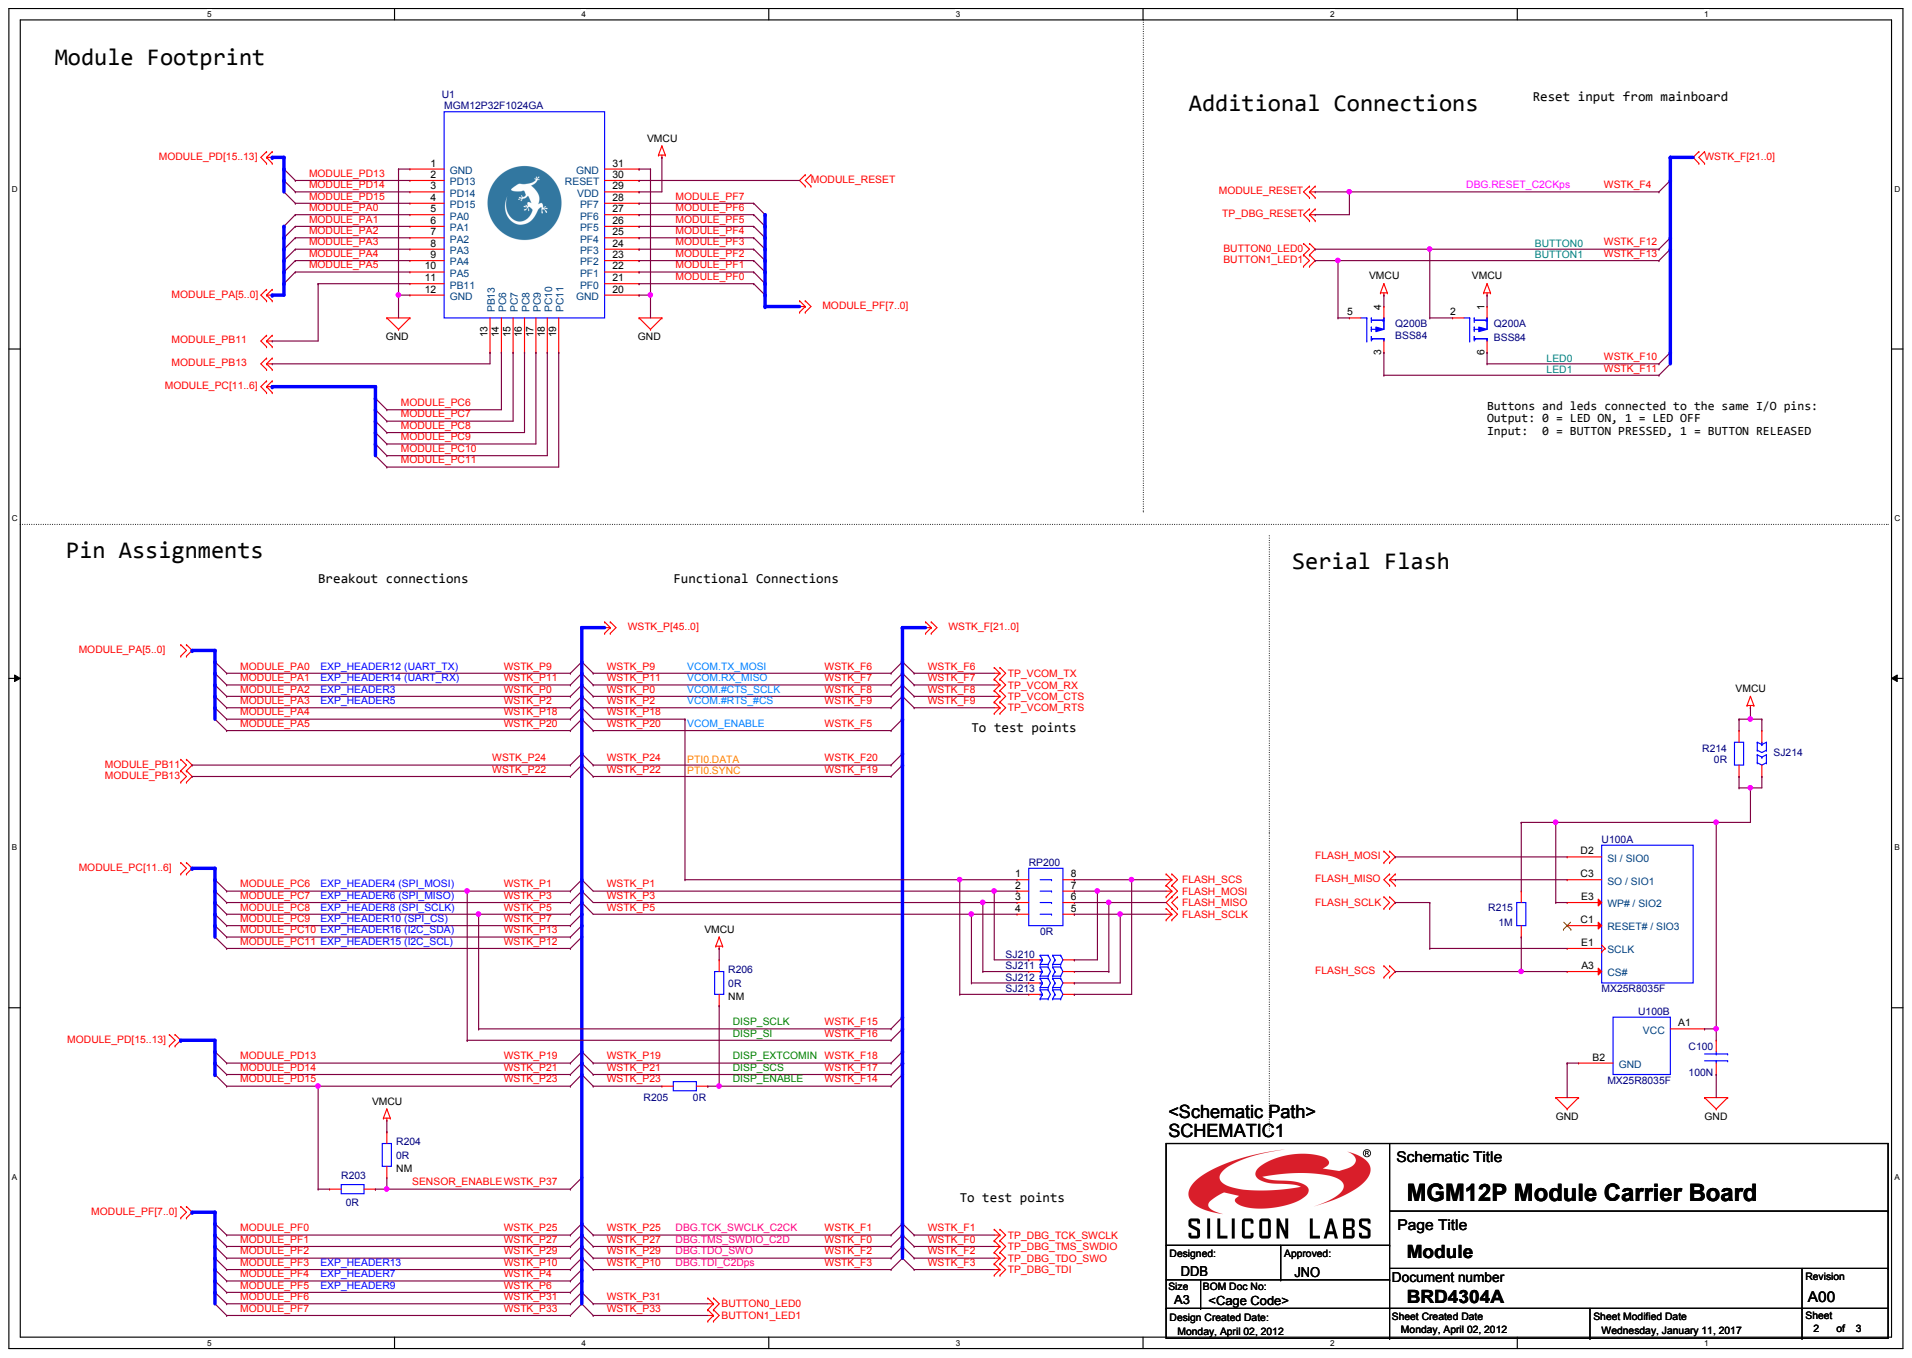
[picture p126: page 2]

Buttons and leds connected to the same I/O pins:
Output: 0 = LED ON, 1 = LED OFF

# WSTK Connectors

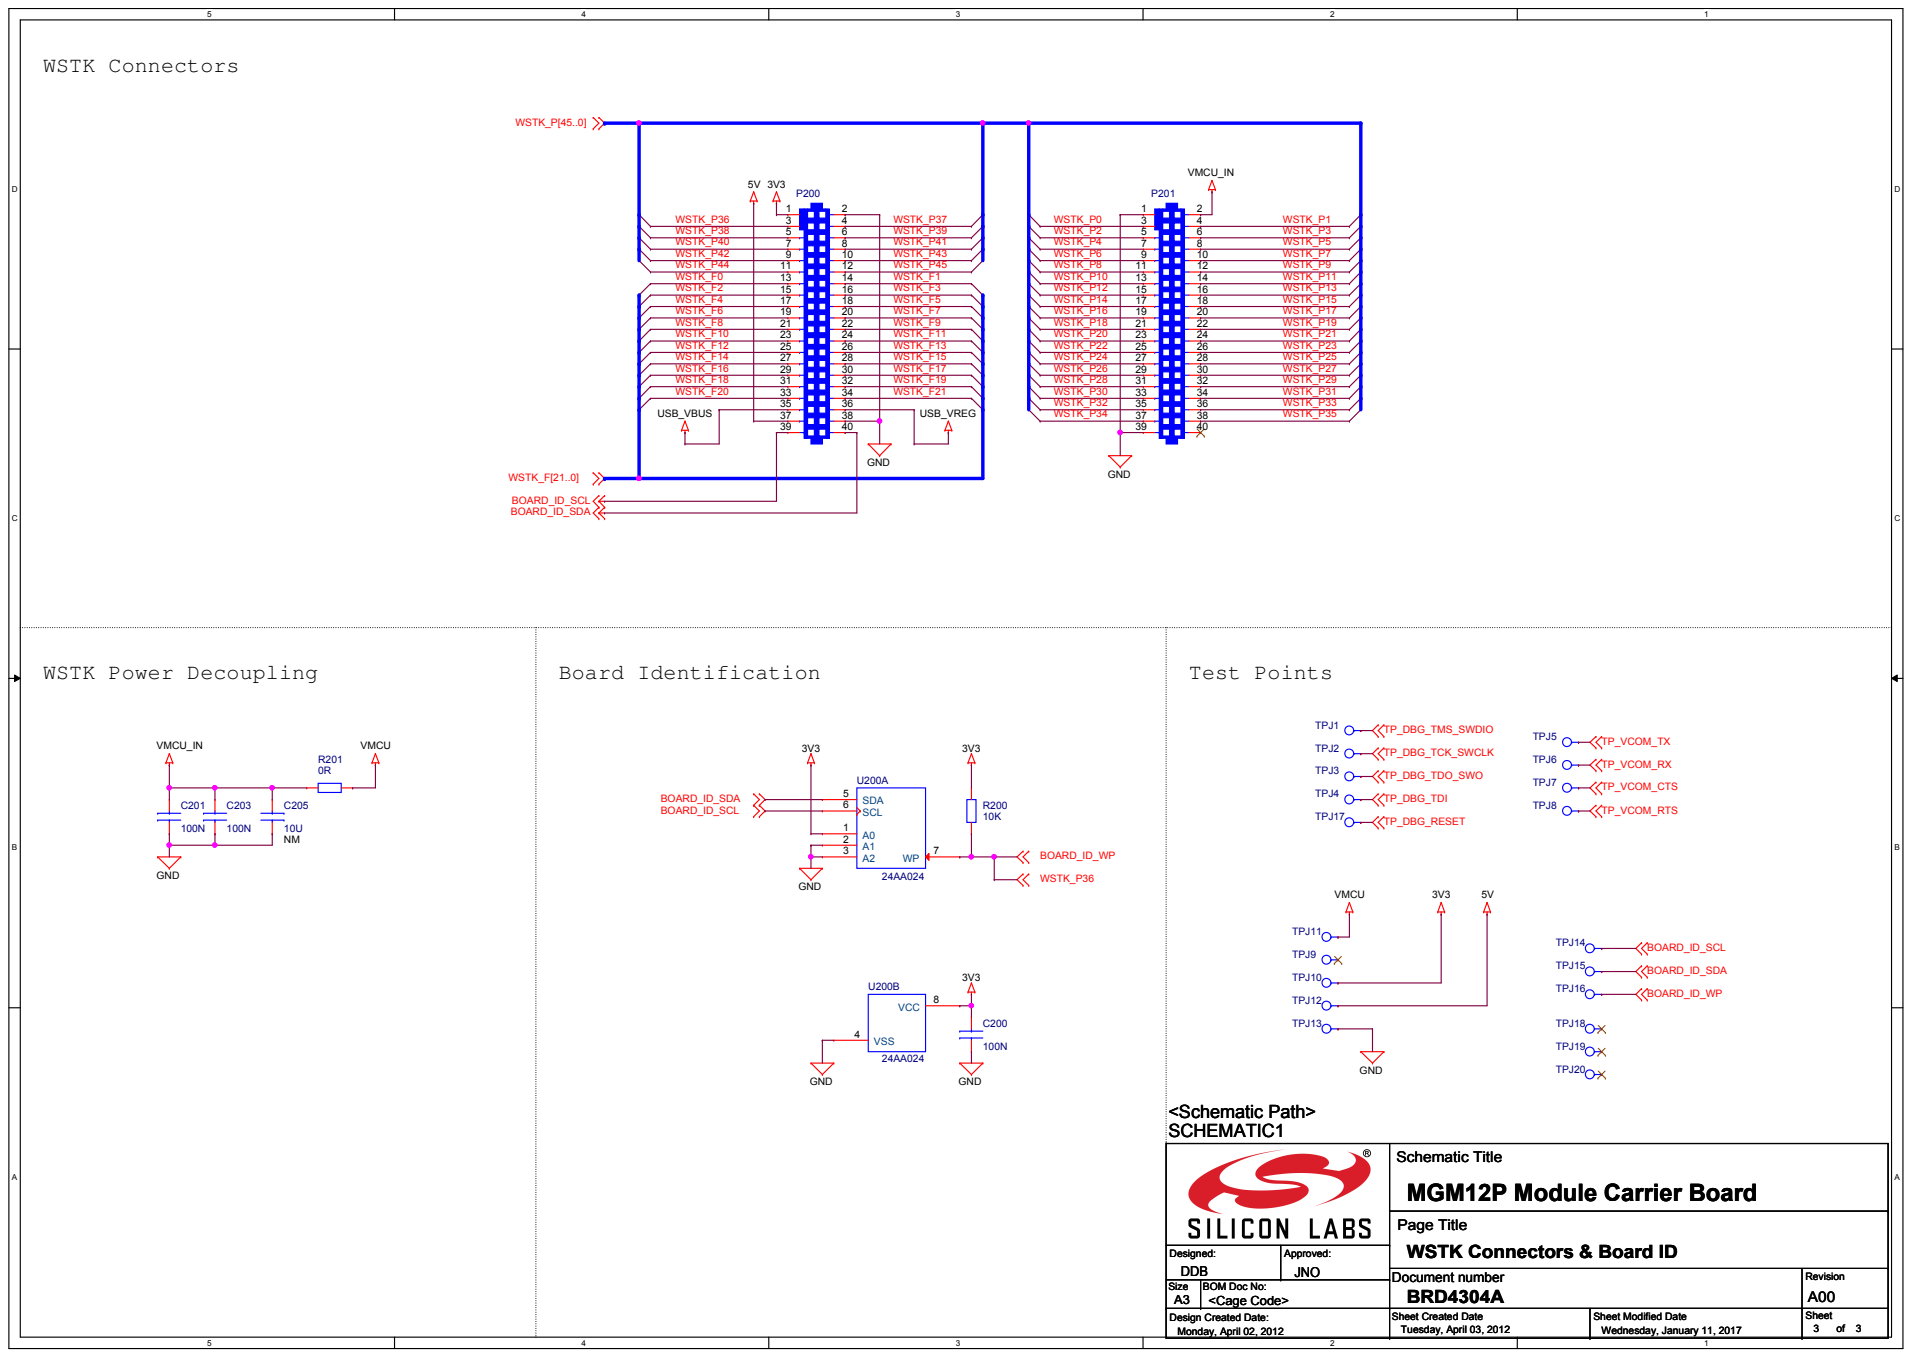
[picture p127: page 3]

Page Title
WSTK Connectors & Board ID
