fbradasc/RCTX/doc/EFR32M/Schematics/Lighting-IST-A0050-assy-draw.pdf

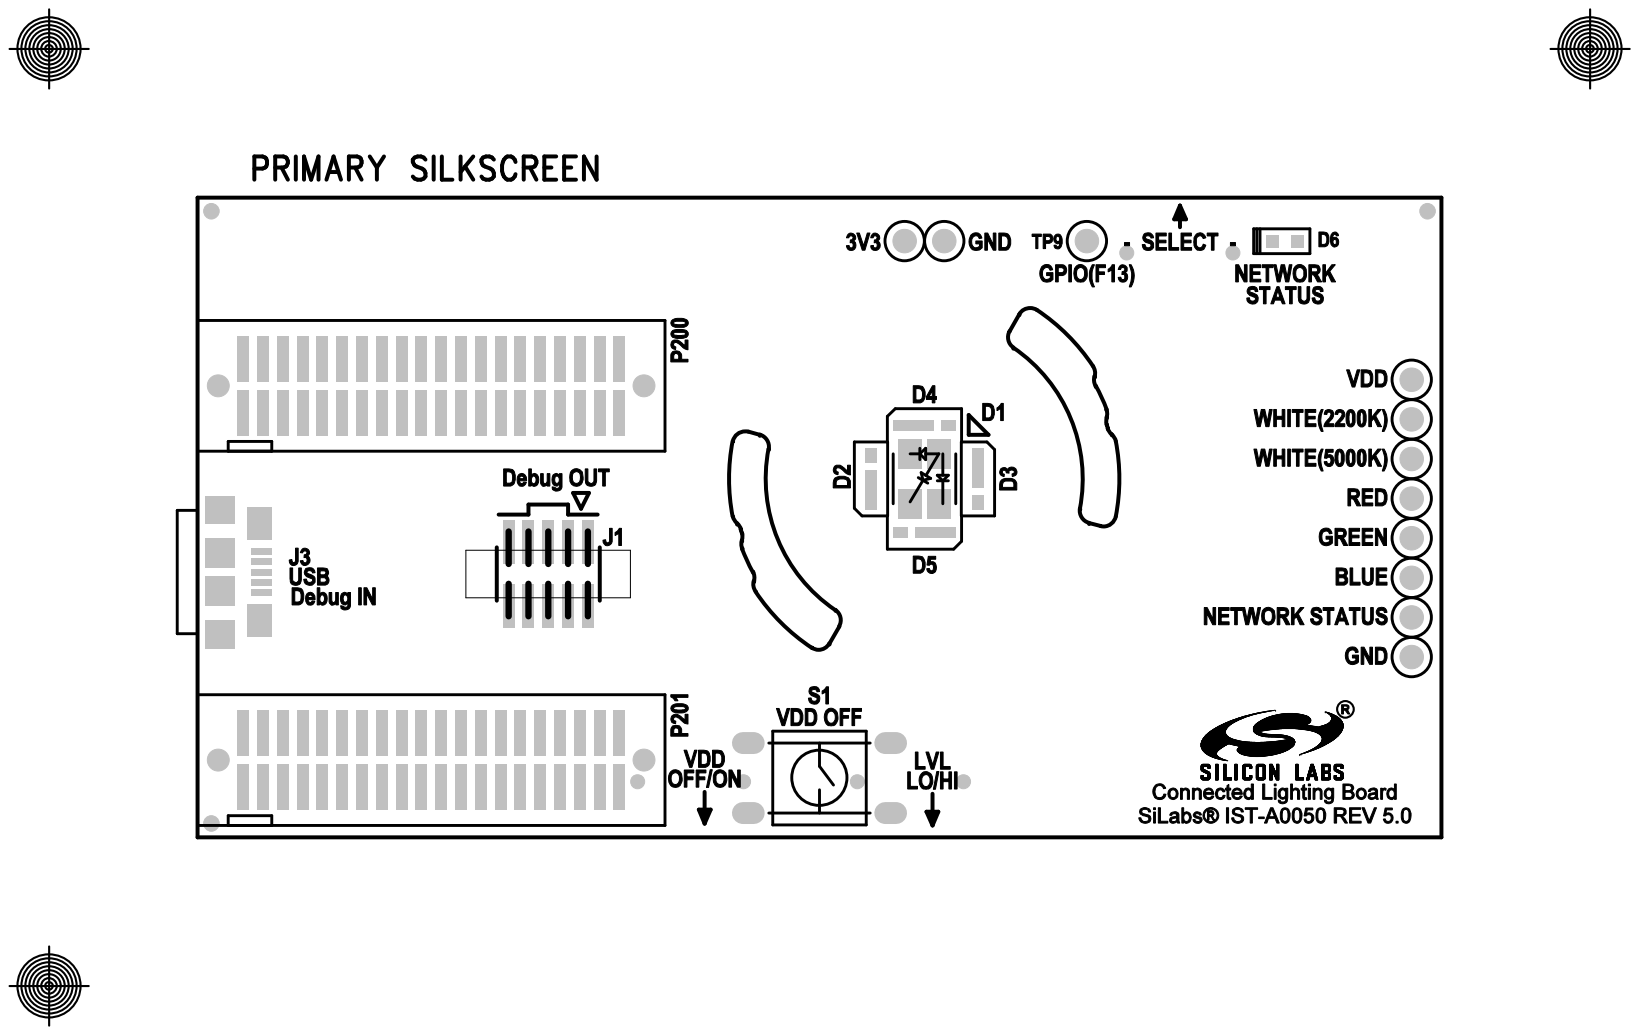
[picture p133: page 1]

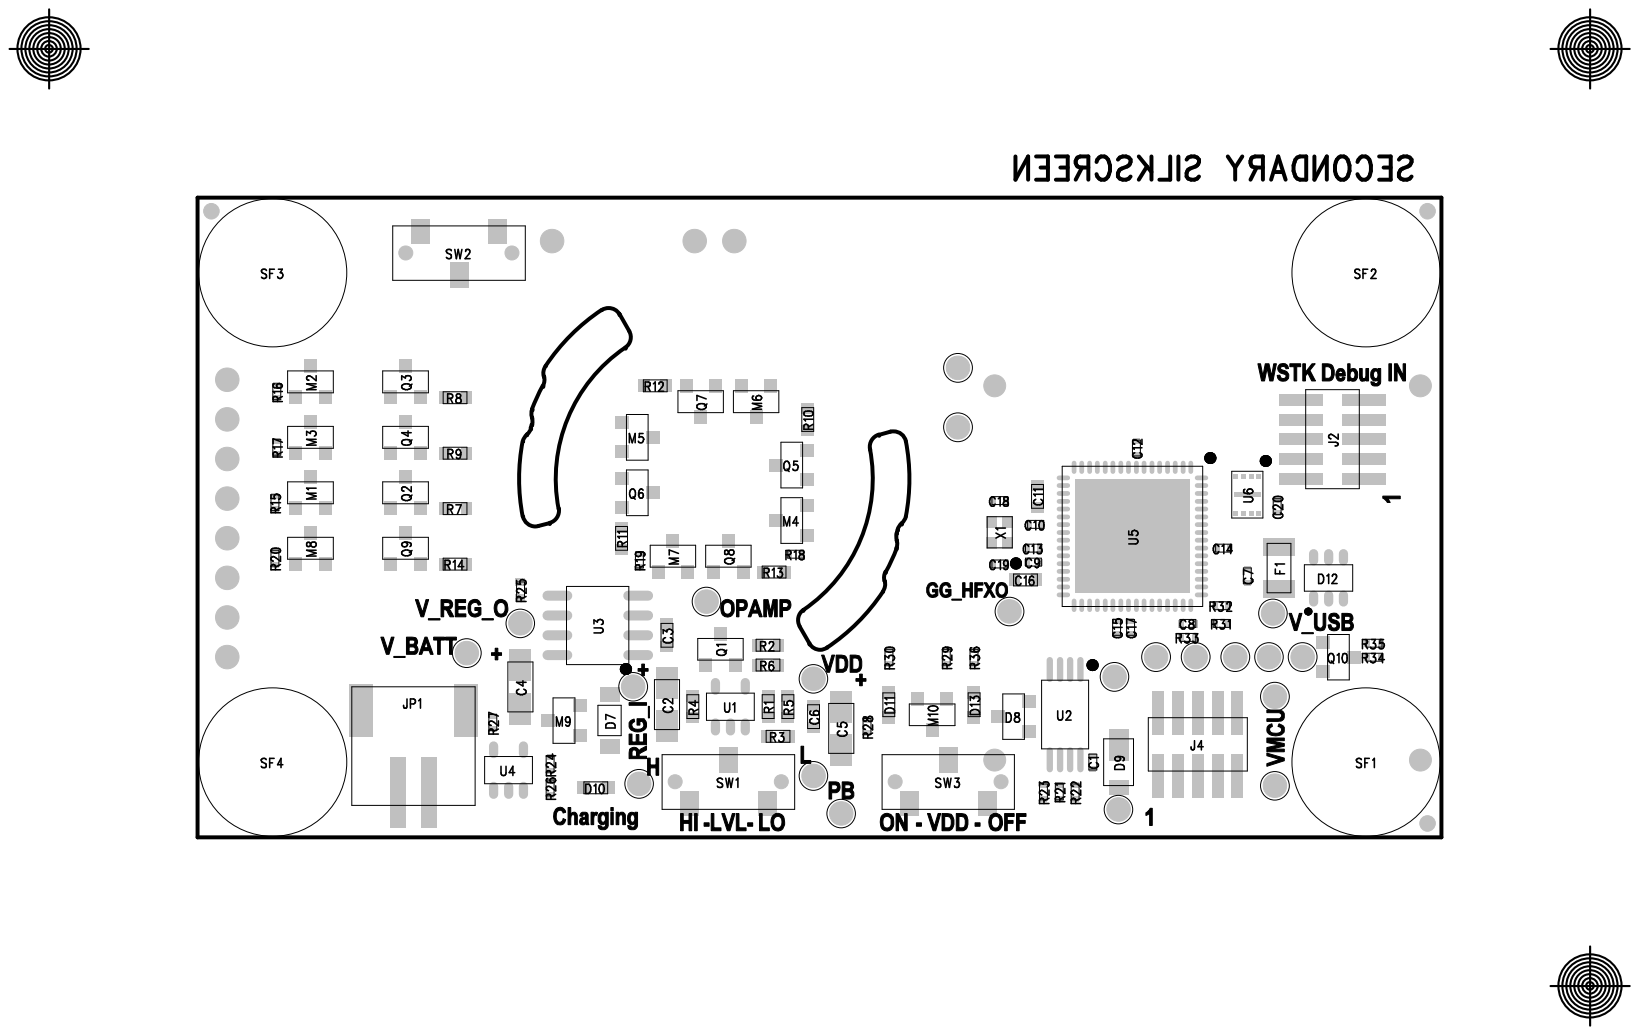
[picture p134: page 2]

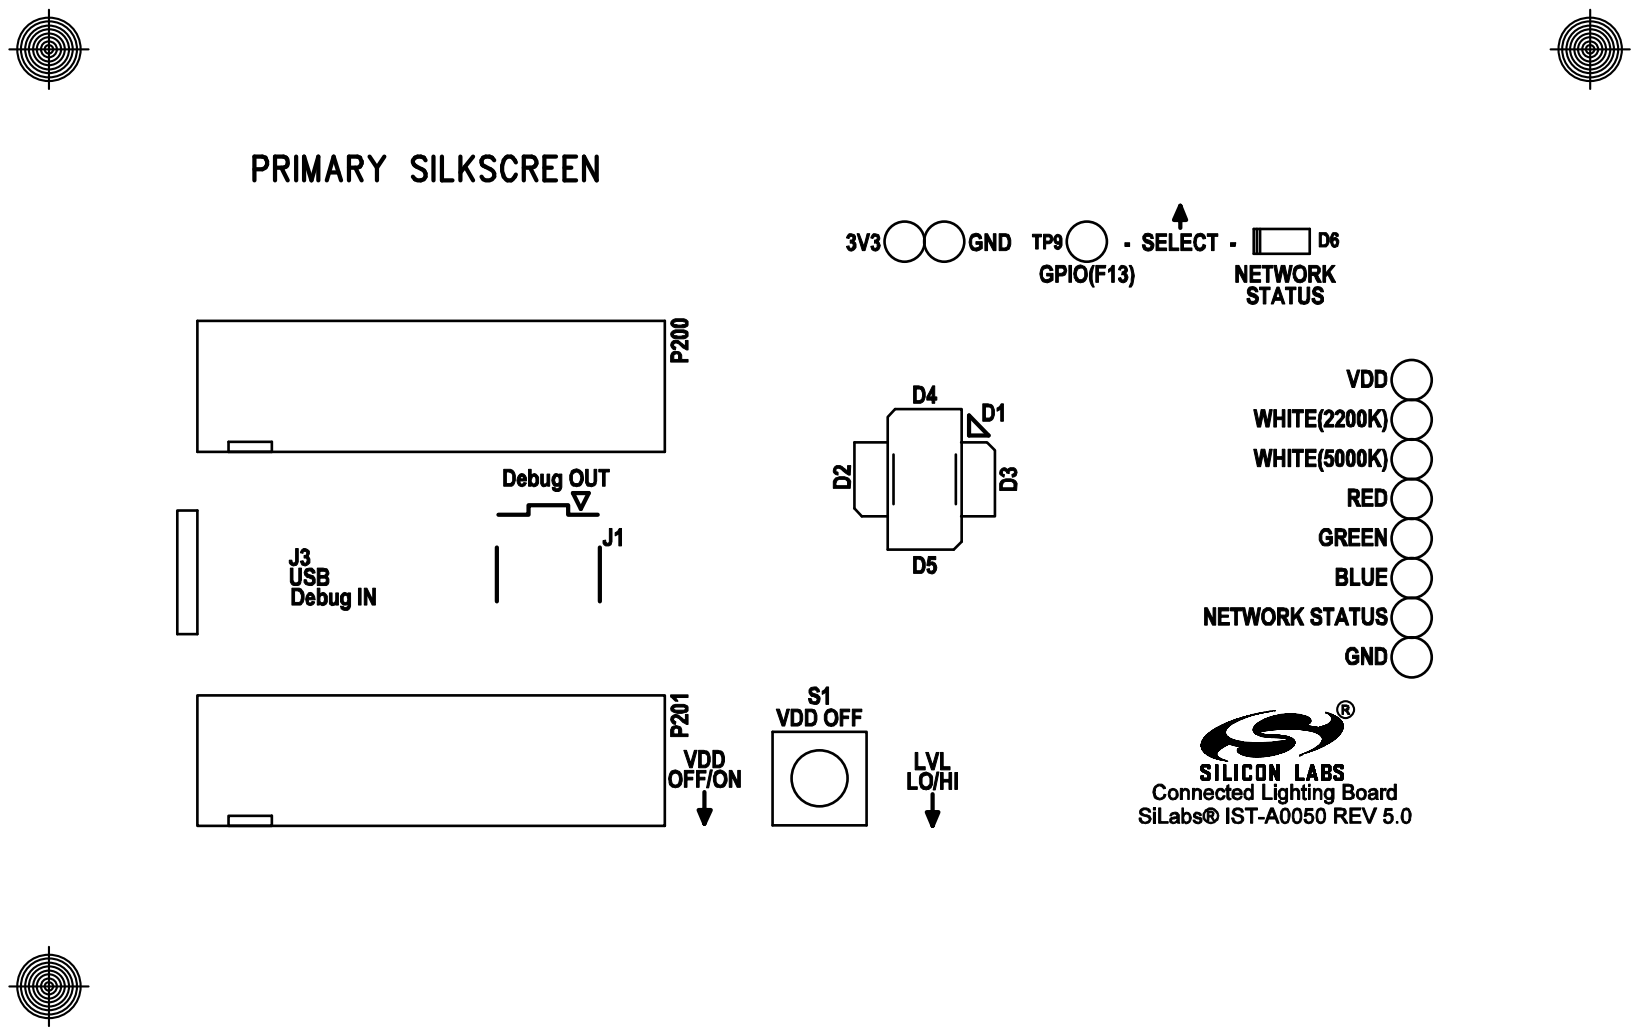
[picture p135: page 3]

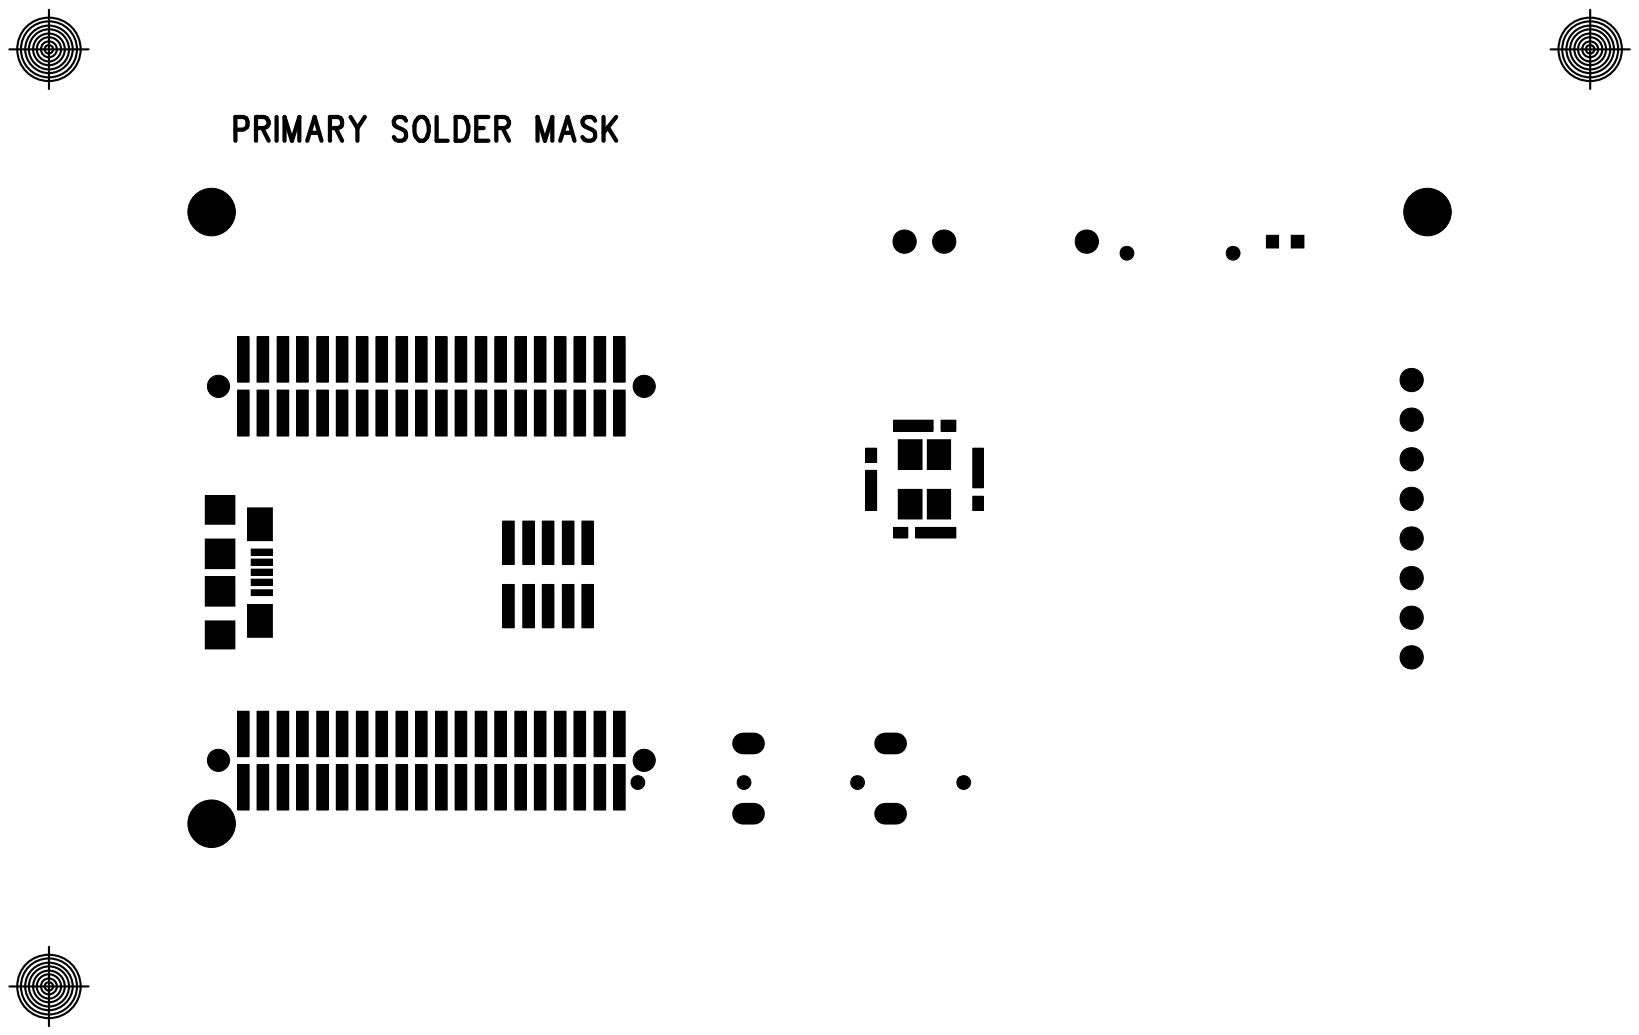
[picture p136: page 4]

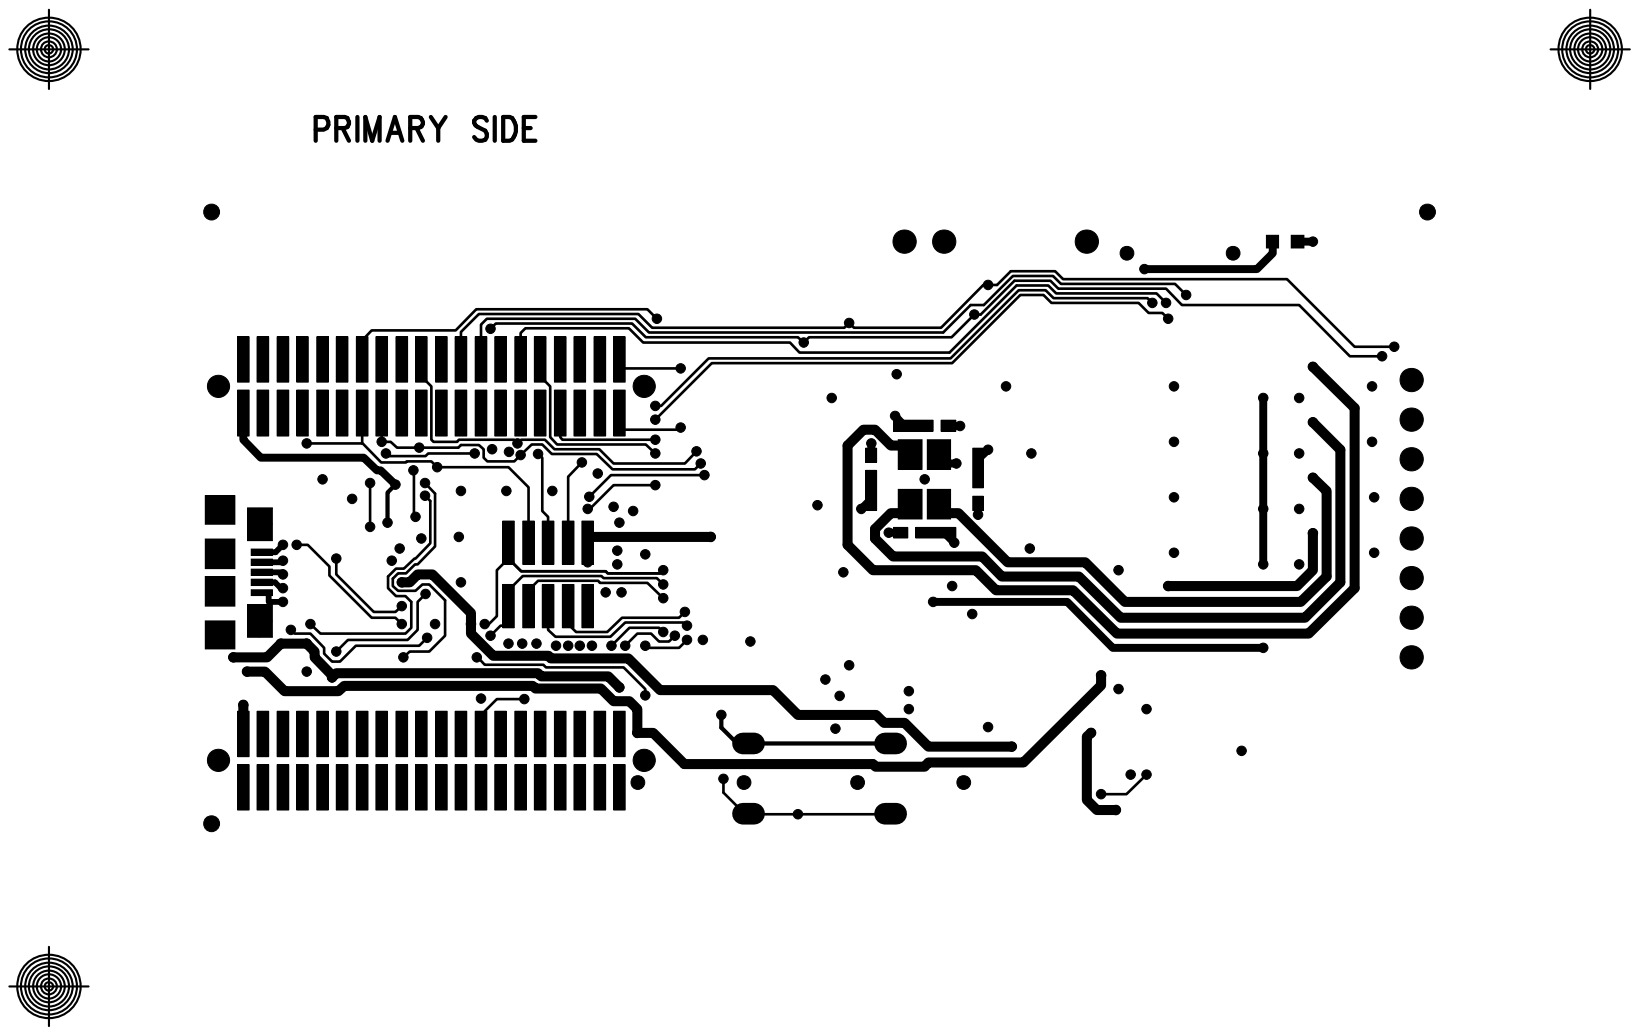
[picture p137: page 5]

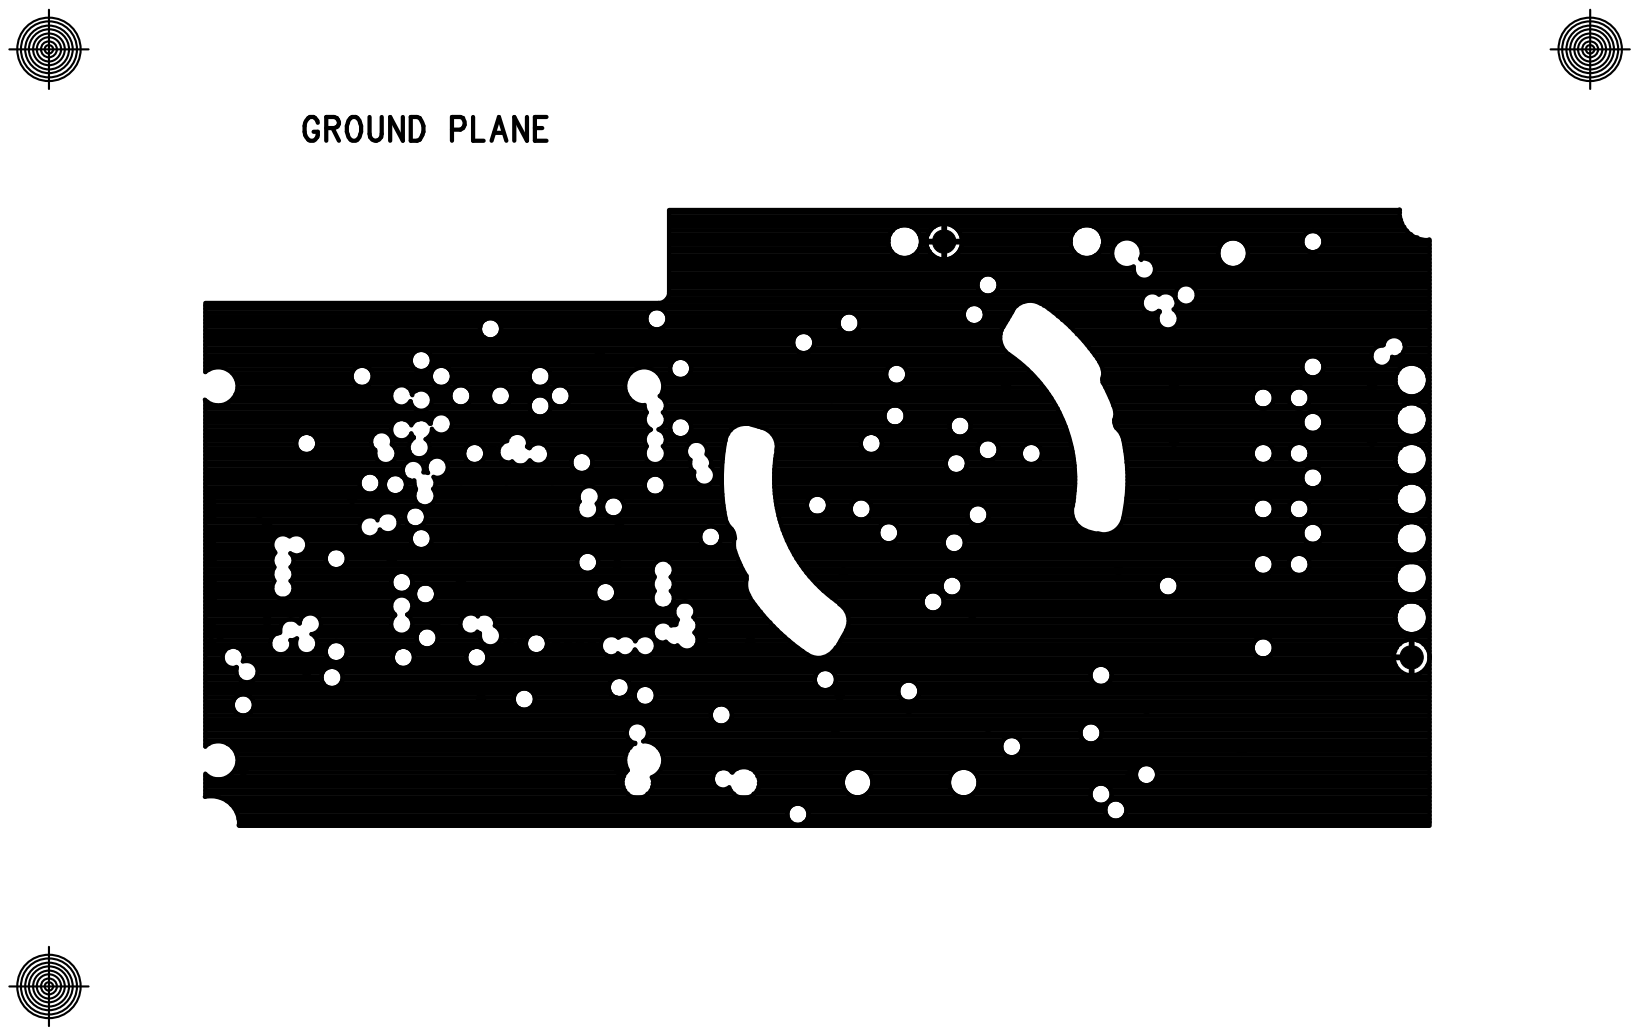
[picture p138: page 6]

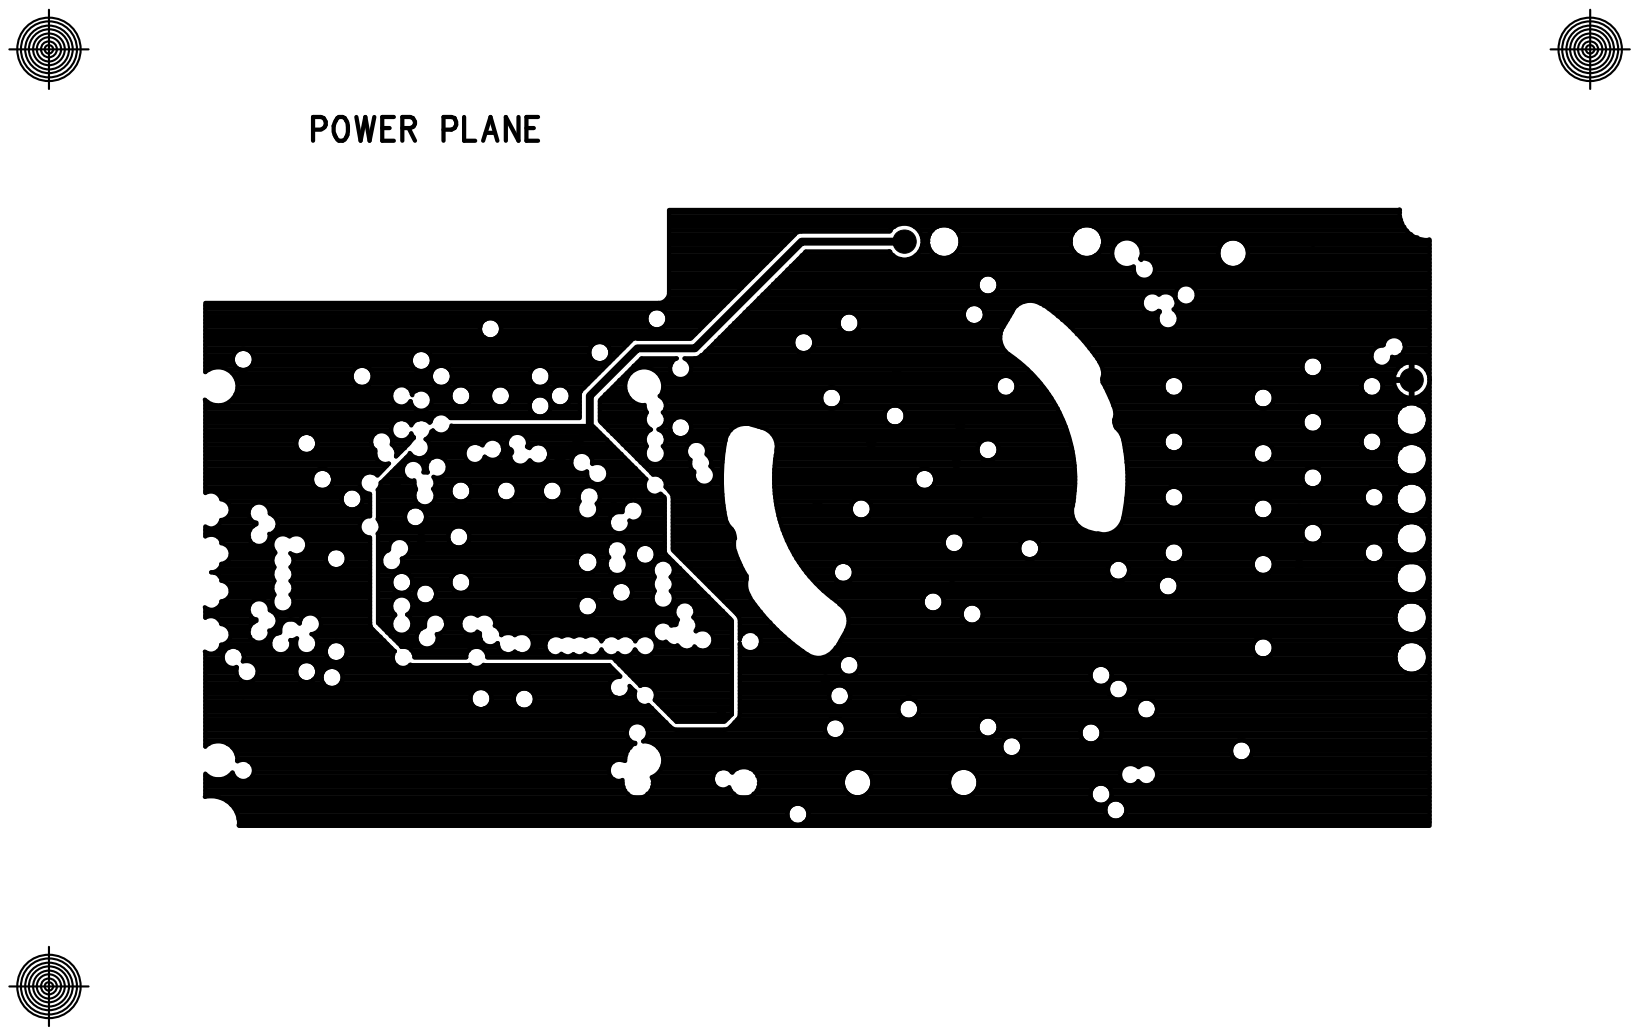
[picture p139: page 7]

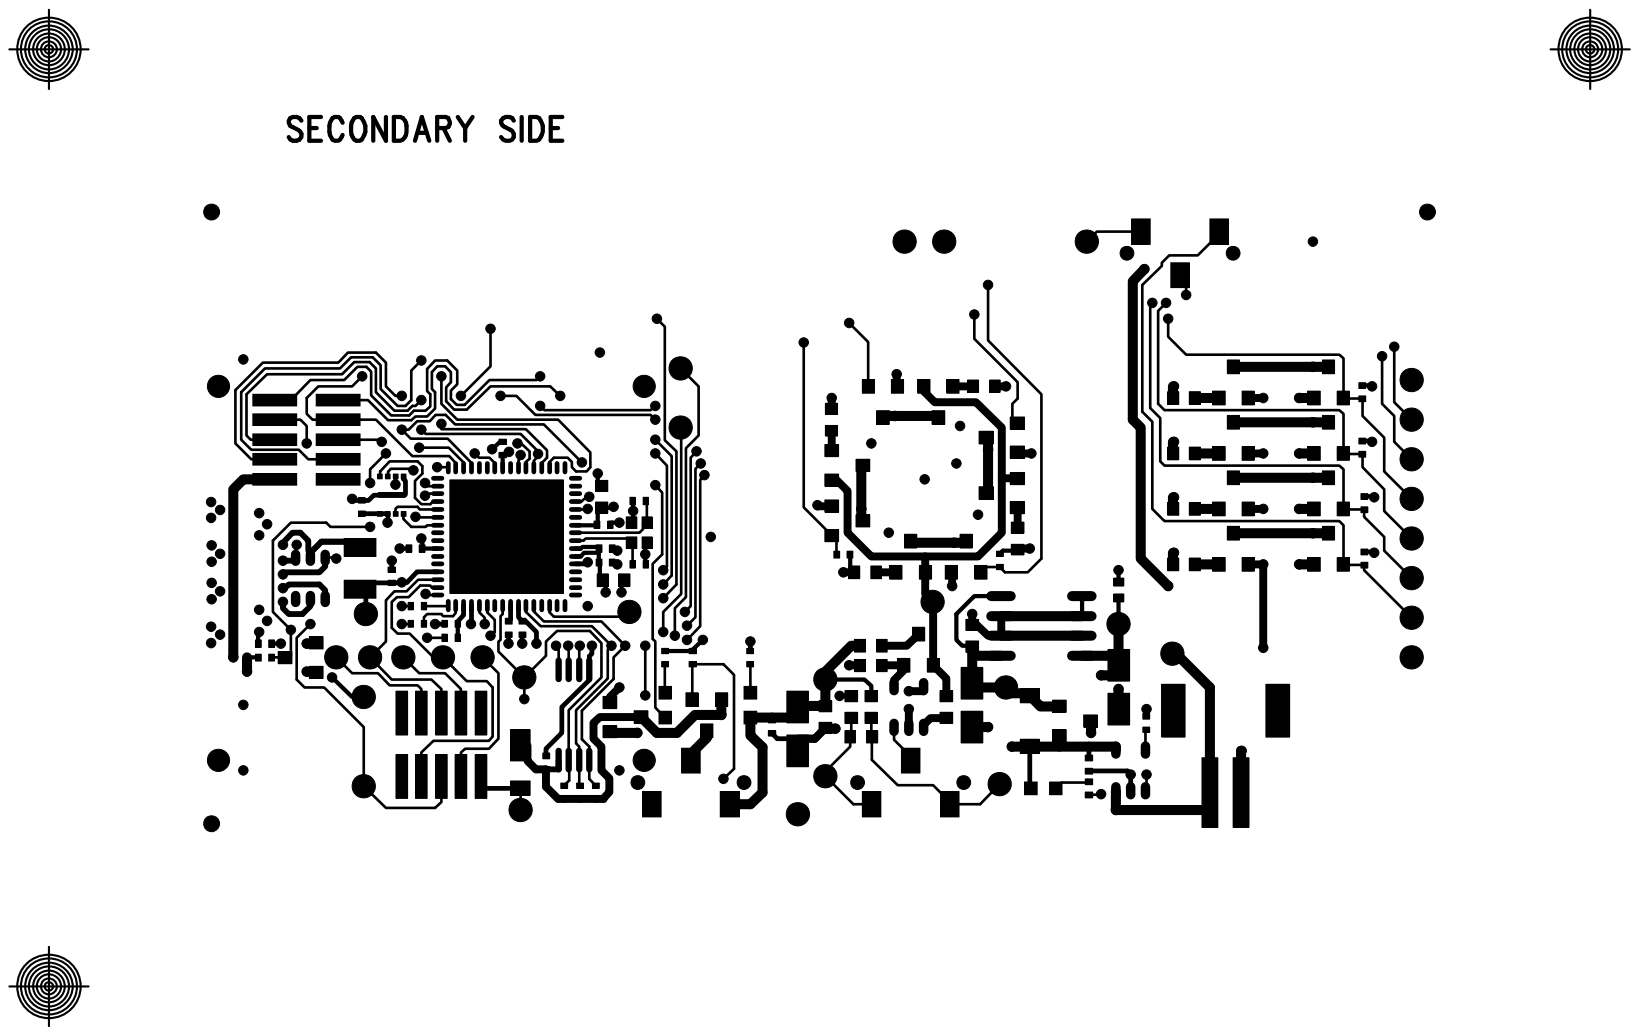
[picture p140: page 8]

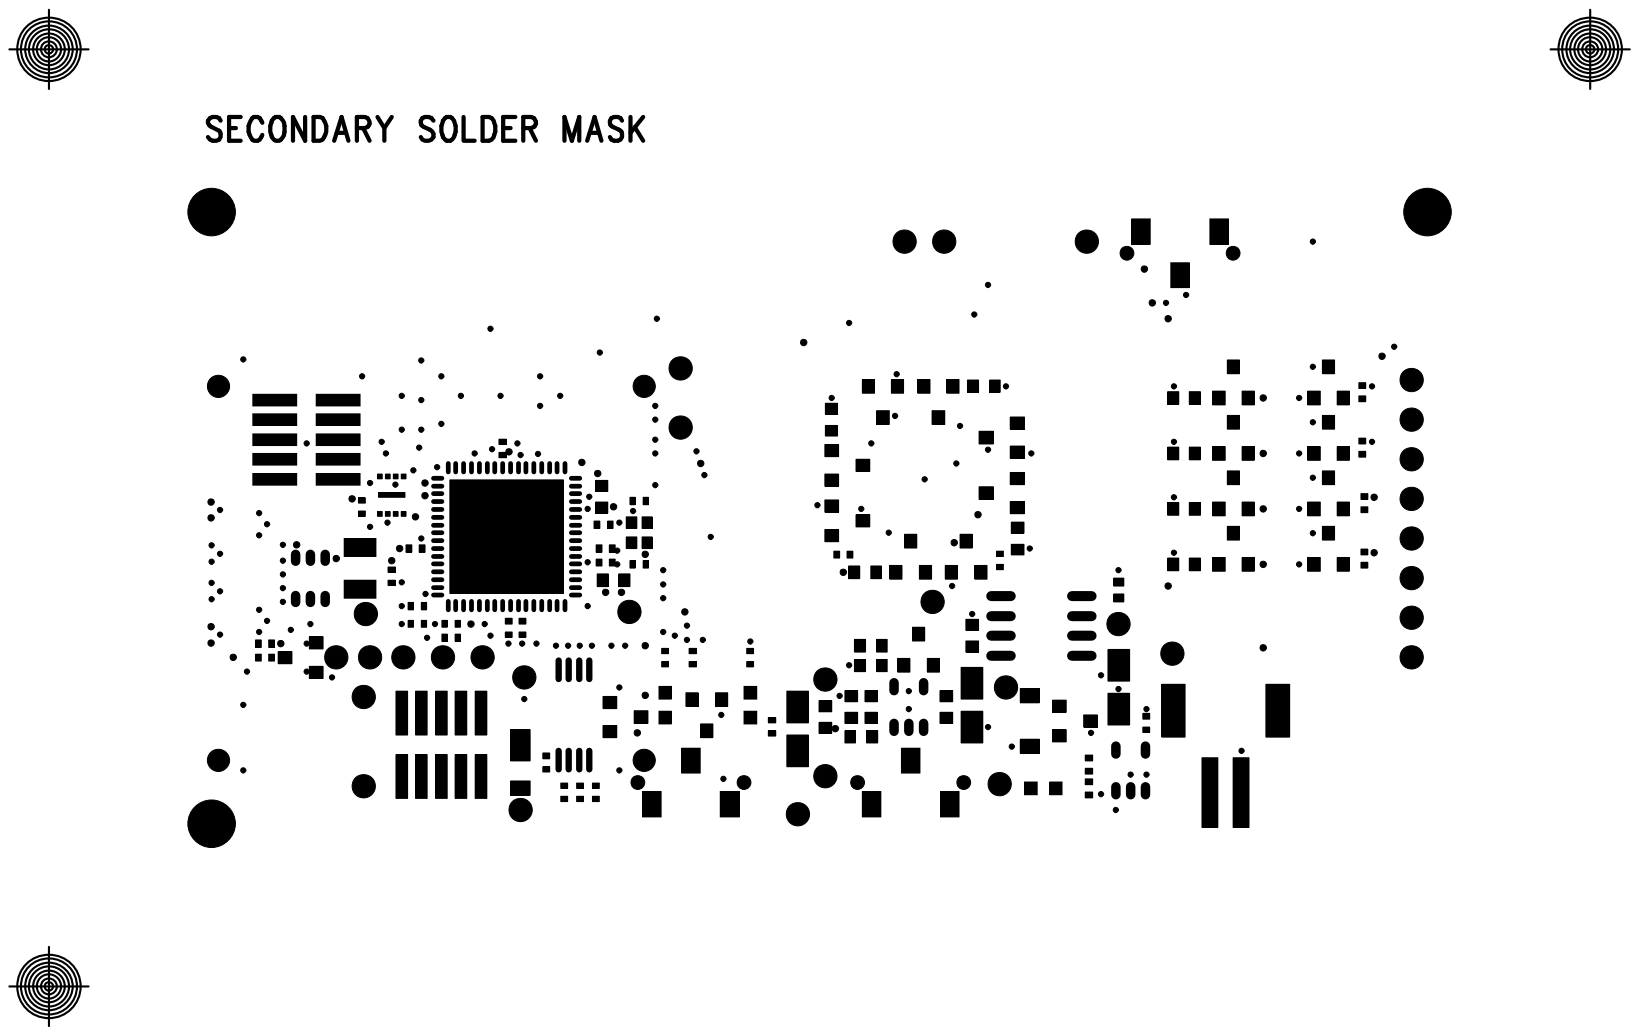
[picture p141: page 9]

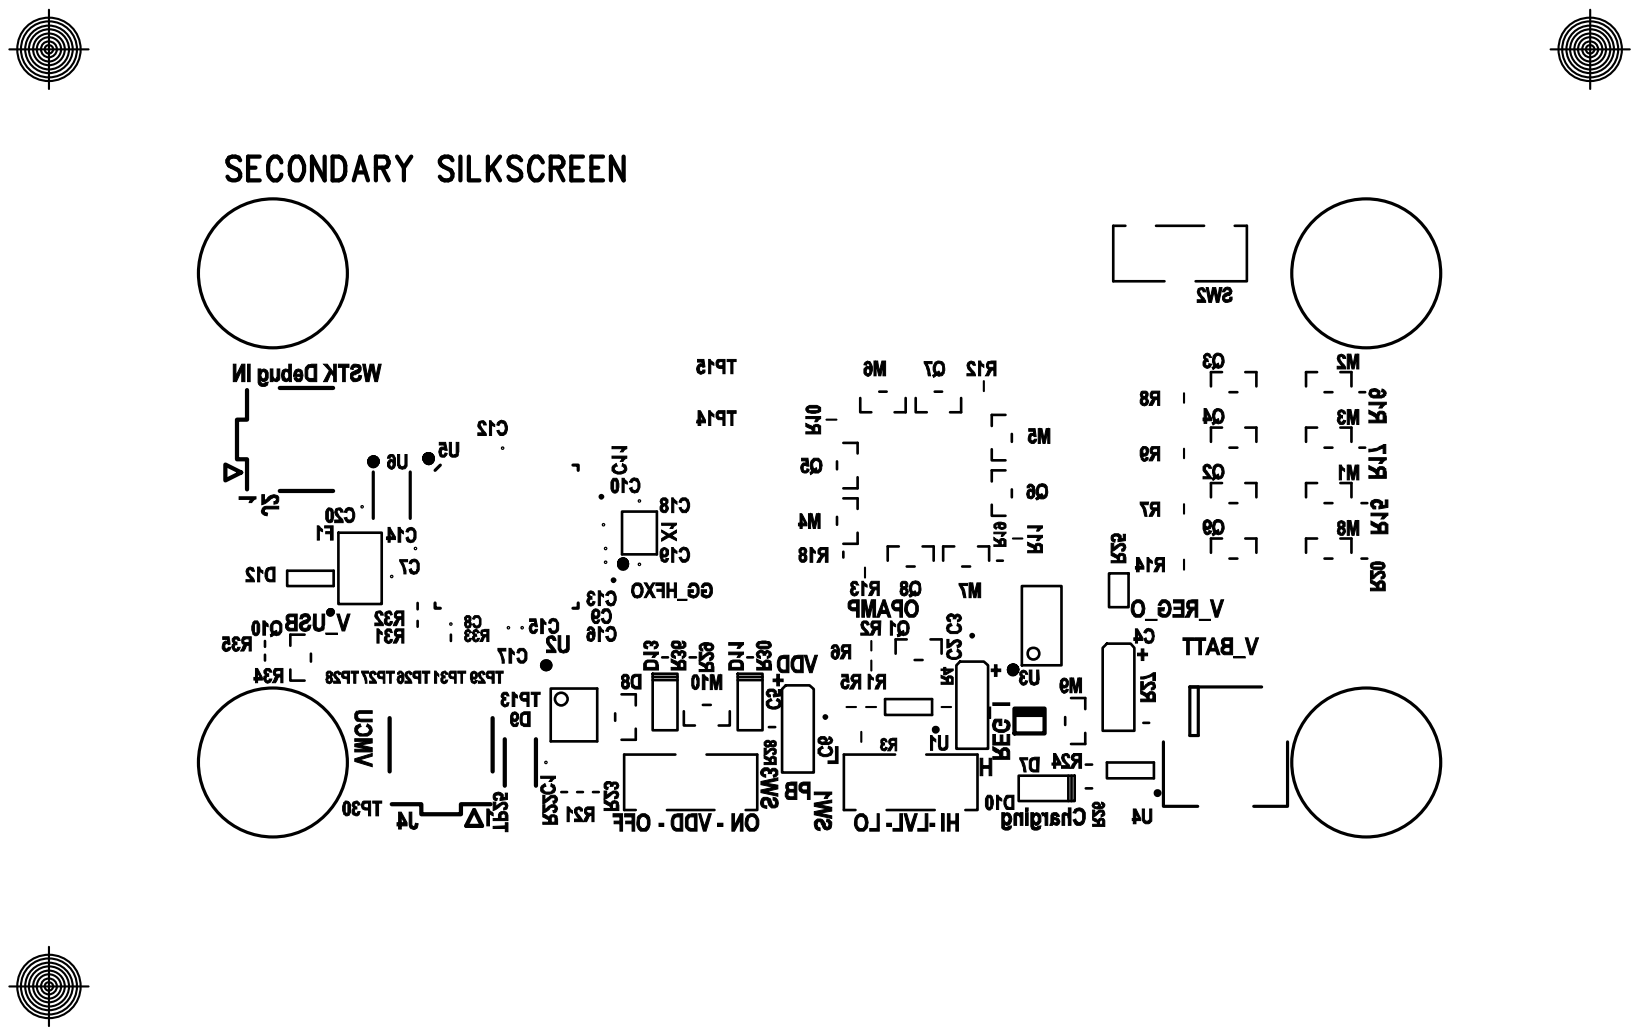
[picture p142: page 10]

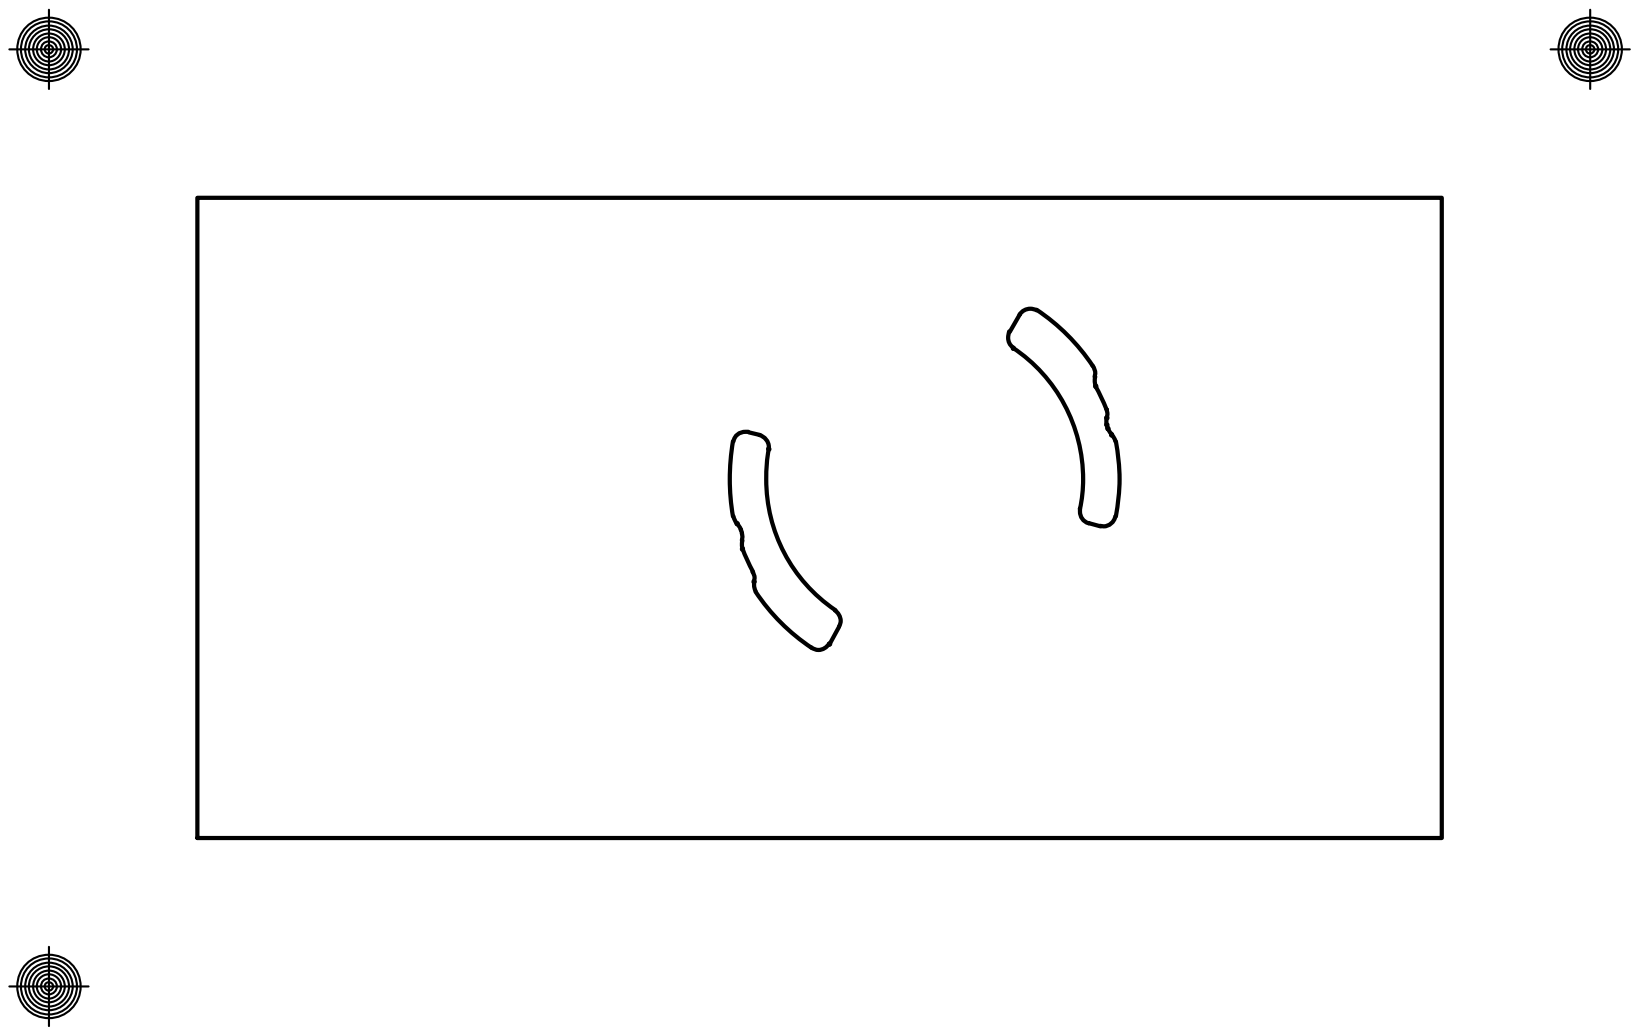
[picture p143: page 13]

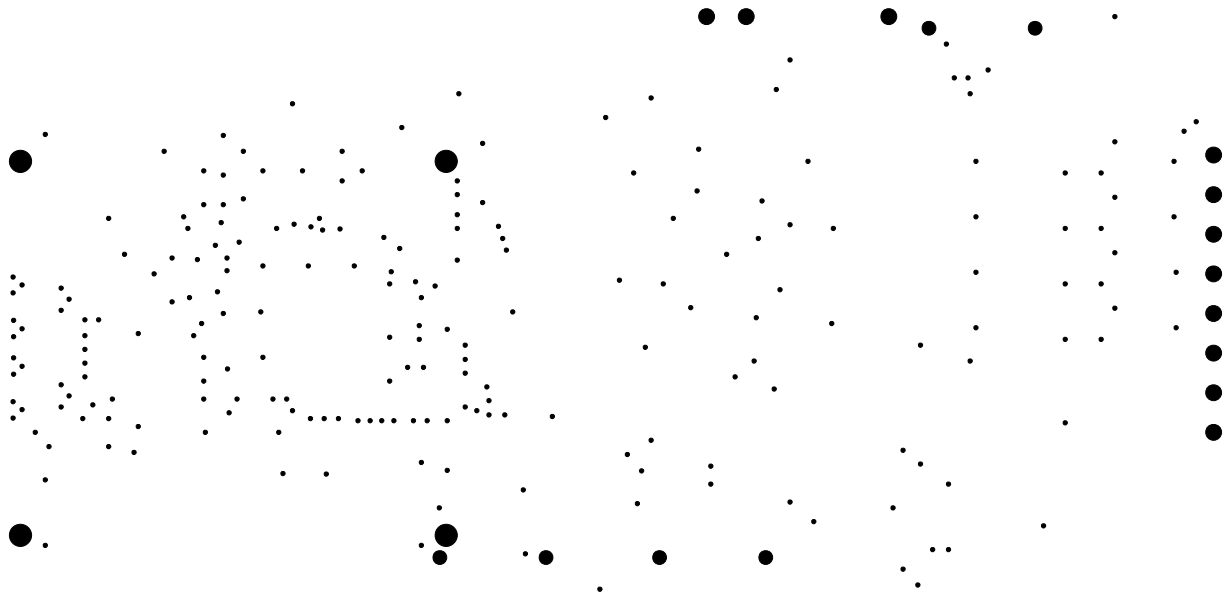
[picture p144: page 14]

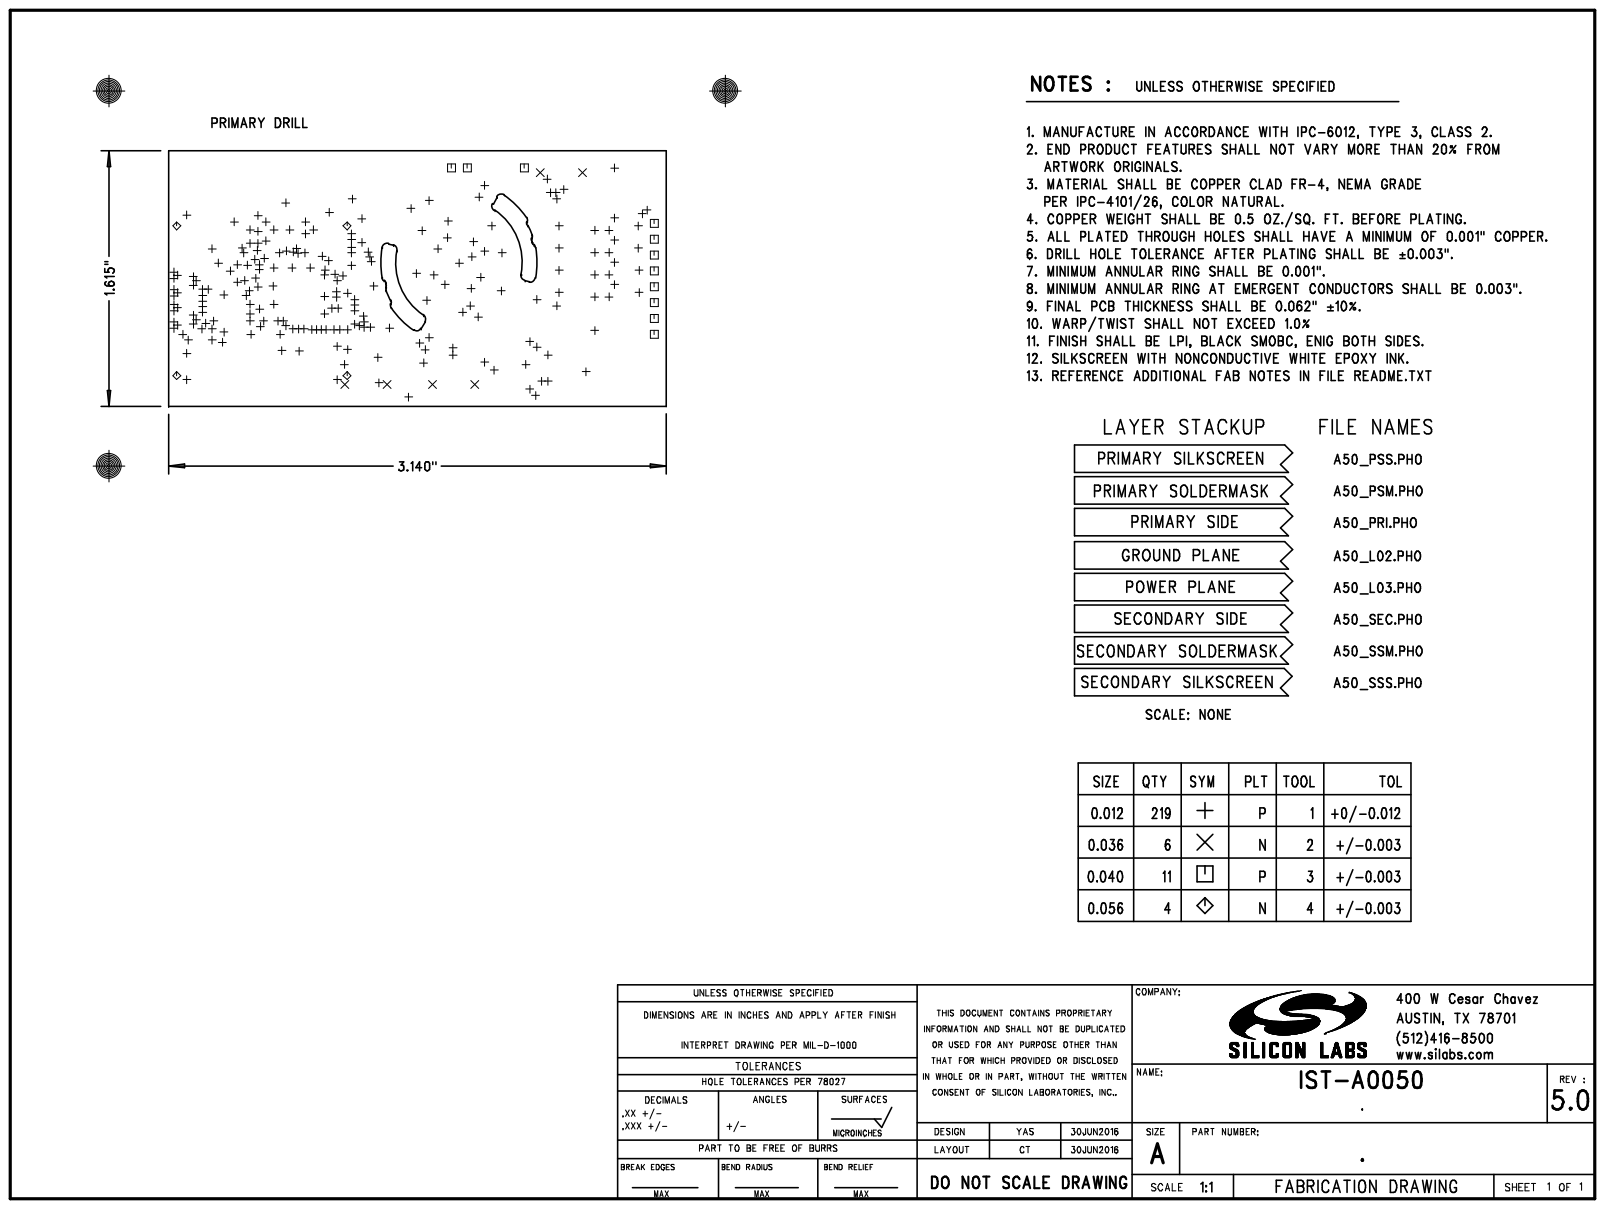
[picture p145: page 15]

IST-A50 REV 5.0
Size:
Panel: 18.0 x 24.0
Array: 5.345 x 6.28
Part: 1.615 x 3.14
Panel Yield:

### 9 Arrays of 6 Parts 54 Parts Total

69.9% Material Utilization
Matrix:
On Panel: 3 x 3, Origin: X0.8825 Y2.48 On Array: 3 x 2
Spacing:
On Panel: 0.1 x 0.1
On Array: 0.0 x 0.0
Panel Borders:
Left: 0.8825 Right: 0.8825 Top: 2.48 Bottom: 2.48
Array Borders:
Left: 0.25 Right: 0.25
Top: 0.0 Bottom: 0.0

Notes:

Please add 4, 0.125" NP tooling holes located 0.125" from tab corners and 3, 40/120 fiduials to each side of array located 0.25" from tooling holes.

Page 1 of 1
