fbradasc/RCTX/doc/EFR32M/Schematics/Lighting-IST-A0050-schematic.pdf

Debug Header, Simplicity Header, and Mini-Simplicity Header location modified.

## Rev 2.0

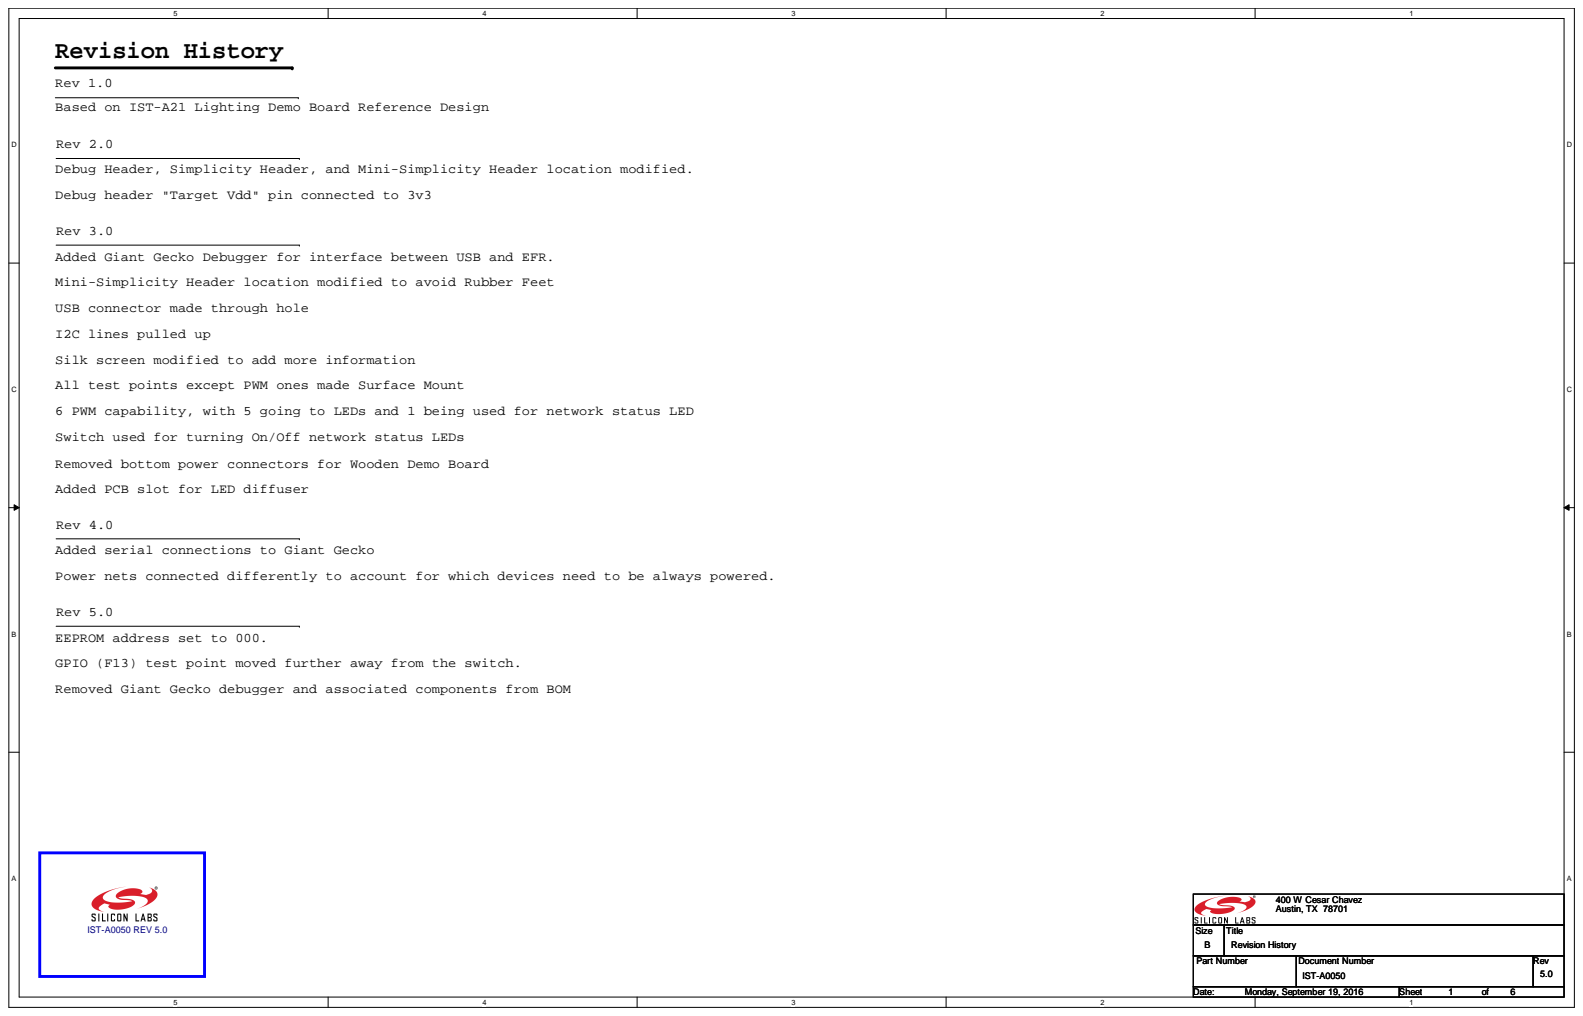
[picture p146: page 1]
Revision History; Size; Title; Document Number; Rev; Date:; Sheet; 400 W Cesar Chavez Austin, TX 78701; Part Number; IST-A0050; Monday, September 19, 2016; IST-A0050 REV 5.0

Rev 1.0
Based on IST-A21 Lighting Demo Board Reference Design

Debug header "Target Vdd" pin connected to 3v3

Rev 3.0
Added Giant Gecko Debugger for interface between USB and EFR.
Mini-Simplicity Header location modified to avoid Rubber Feet
USB connector made through hole
I2C lines pulled up
Silk screen modified to add more information
All test points except PWM ones made Surface Mount
6 PWM capability, with 5 going to LEDs and 1 being used for network status LED
Switch used for turning On/Off network status LEDs
Removed bottom power connectors for Wooden Demo Board
Added PCB slot for LED diffuser

Rev 4.0
Added serial connections to Giant Gecko
Power nets connected differently to account for which devices need to be always powered.

Rev 5.0
EEPROM address set to 000.
GPIO (F13) test point moved further away from the switch.
Removed Giant Gecko debugger and associated components from BOM

# Lighting Demo LEDs LED Brightness Selection

# Page Test Points

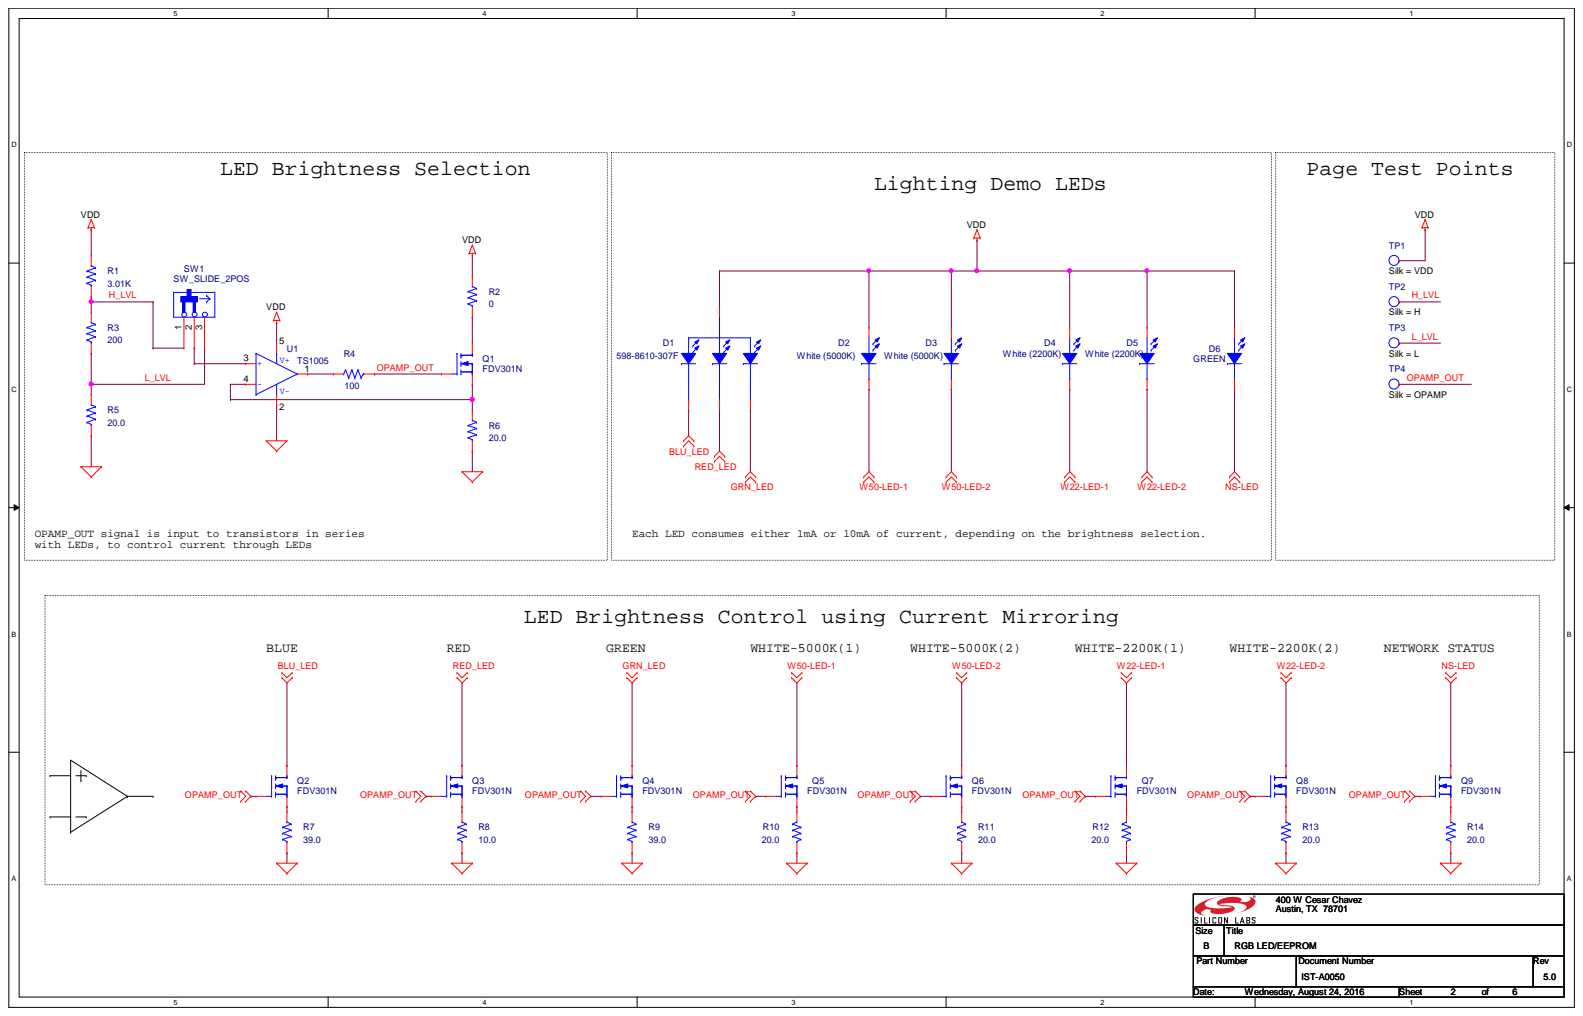
[picture p147: page 2]

OPAMP_OUT signal is input to transistors in series
with LEDs, to control current through LEDs

Each LED consumes either 1mA or 10mA of current, depending on the brightness selection.

LED Brightness Control using Current Mirroring

BLUE | RED | GREEN | WHITE-5000K | WHITE-5000K | WHITE-2200K | WHITE-2200K | NETWORK STATUS

# Lighting Demo LEDs - PWM Controls

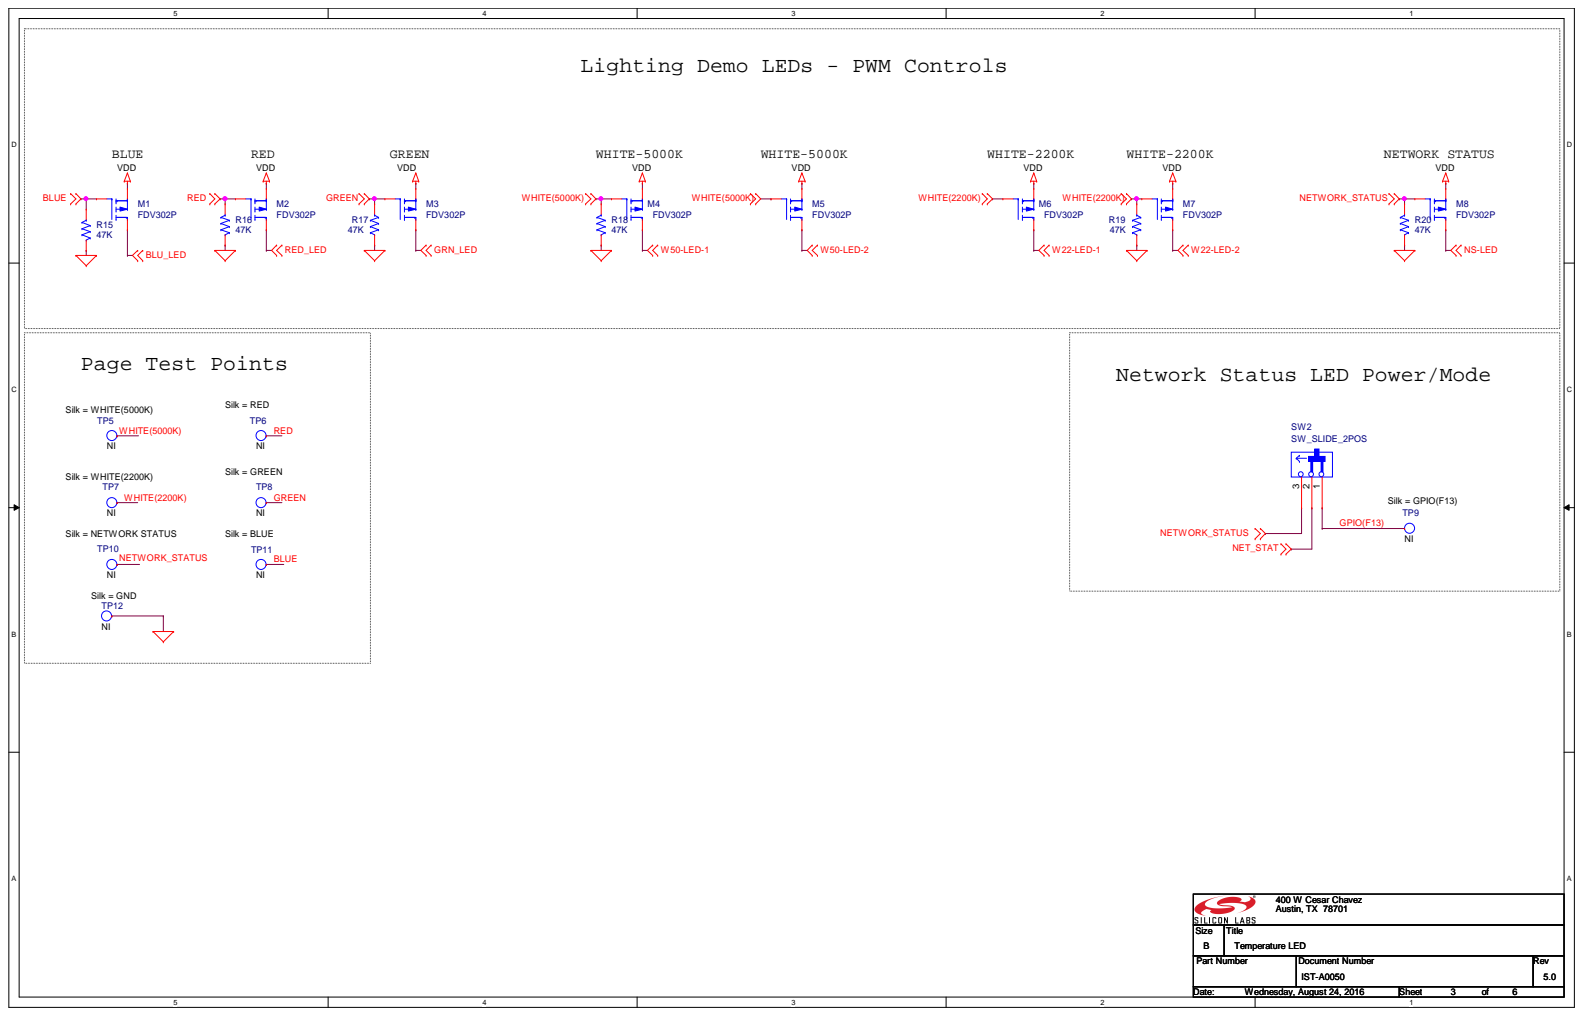
[picture p148: page 3]

Network Status LED Power/Mode Page Test Points

# Output Connectors

## Module to LDB (Header)

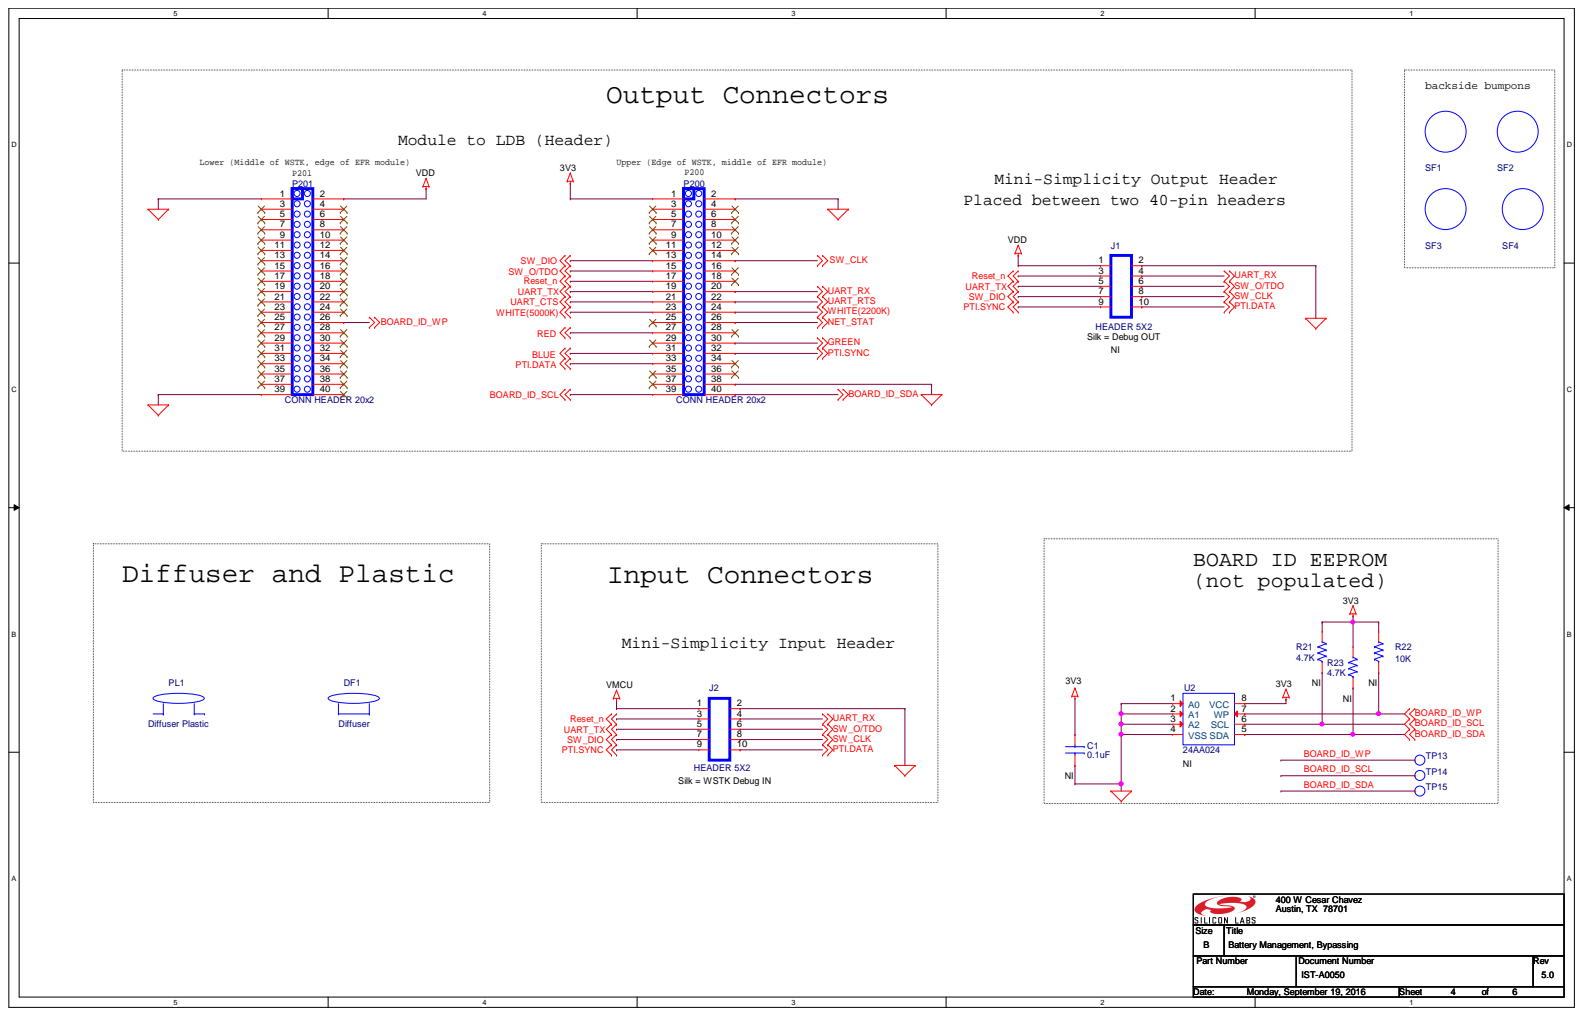
[picture p149: page 4]

Mini-Simplicity Output Header
Placed between two 40-pin headers

Mini-Simplicity Input Header

HEADER 5X2
Silk = WSTK Debug IN

# Lighting Board Input Power Options

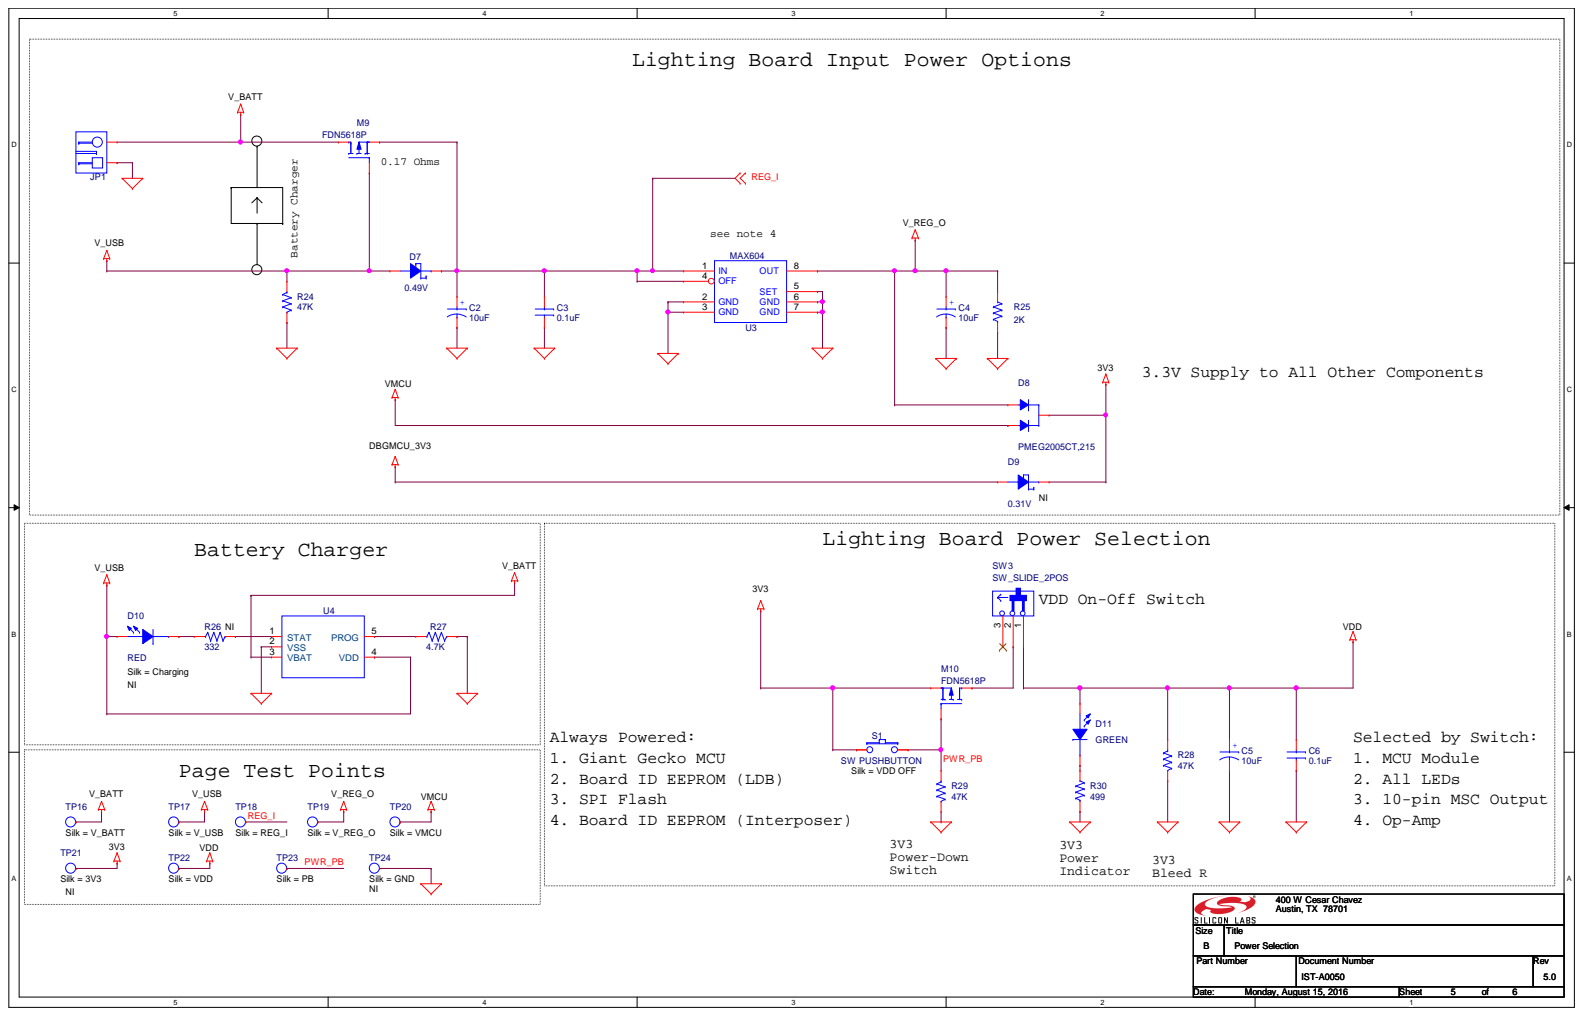
[picture p150: page 5]

3.3V Supply to All Other Components

Lighting Board Power Selection

Always Powered:
1. Giant Gecko MCU
2. Board ID EEPROM (LDB)
3. SPI Flash
4. Board ID EEPROM (Interposer)

External Connectors | Giant Gecko Debug MCU (not populated)

## micro-USB Connector

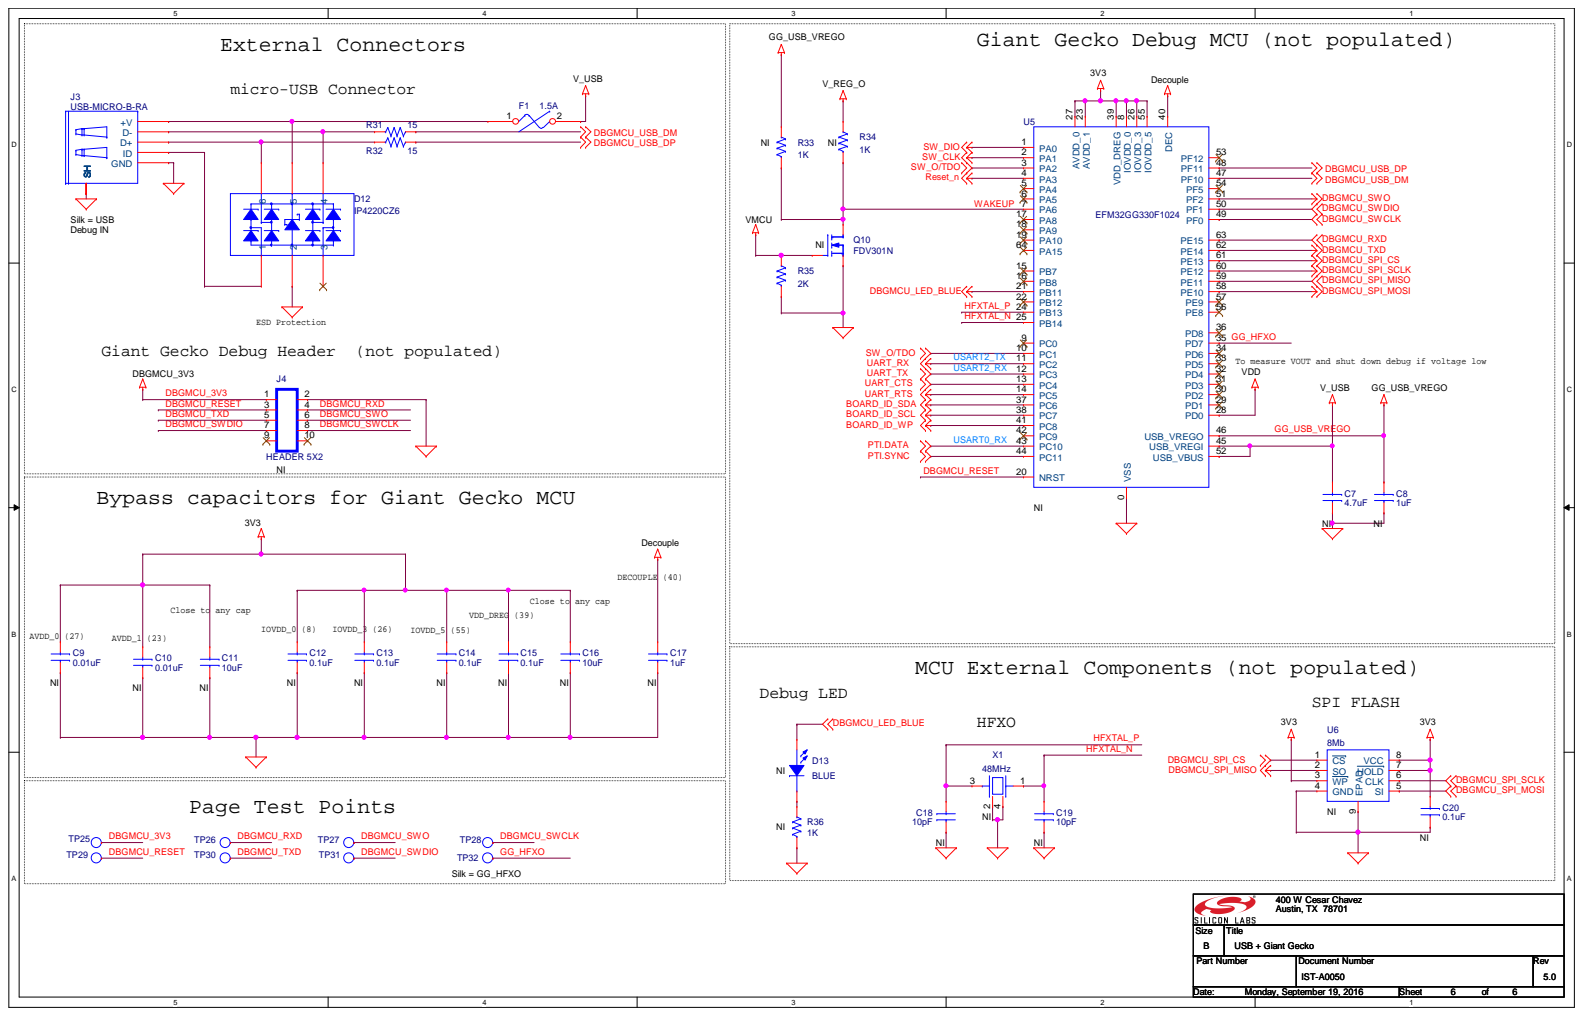
[picture p151: page 6]

Giant Gecko Debug Header (not populated)

To measure VOUT and shut down debug if voltage low
VDD

Bypass capacitors for Giant Gecko MCU

MCU External Components (not populated)
