fbradasc/RCTX/kicad/RCRX_ERF32MG12.pdf

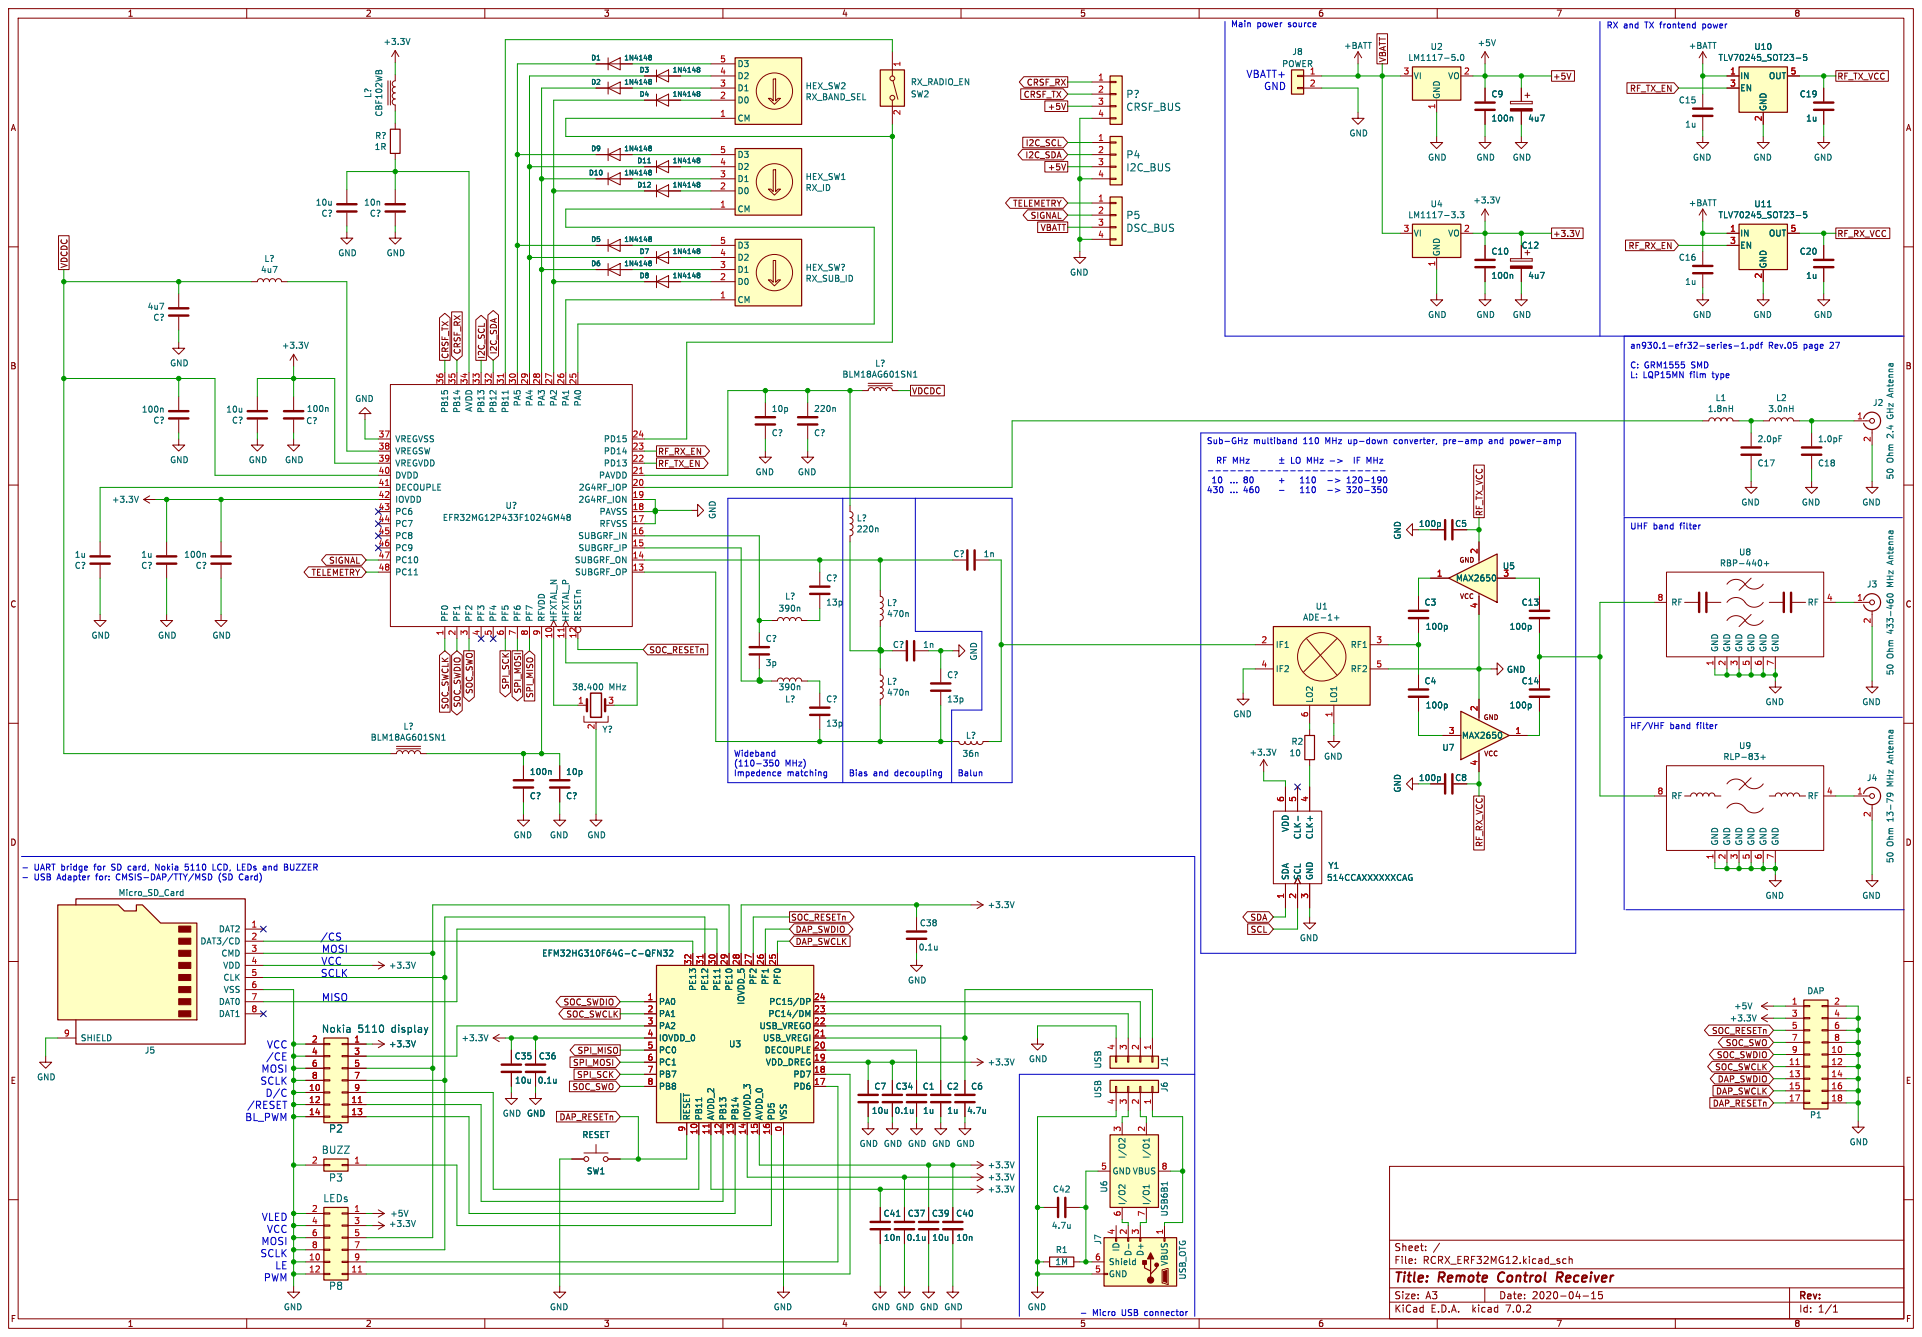
[picture p152: page 1]

2 J2 50 Ohm 2.4 GHz Antenna GND

3 PA5 30 PB11 31 PB12 32 PB13 33 AVDD 34 PB14 35 PB15 36 VREGVSS 37 VREGSW 38 VREGVDD 39 PF3

HF/VHF band filter UHF band filter VCC

J3 50 Ohm 433-460 MHz Antenna GND

J4 50 Ohm 13-79 MHz Antenna GND

- UART bridge for SD card, Nokia 5110 LCD, LEDs and BUZZER
