fbradasc/RCTX/kicad/RCTX_ERF32MG12.pdf

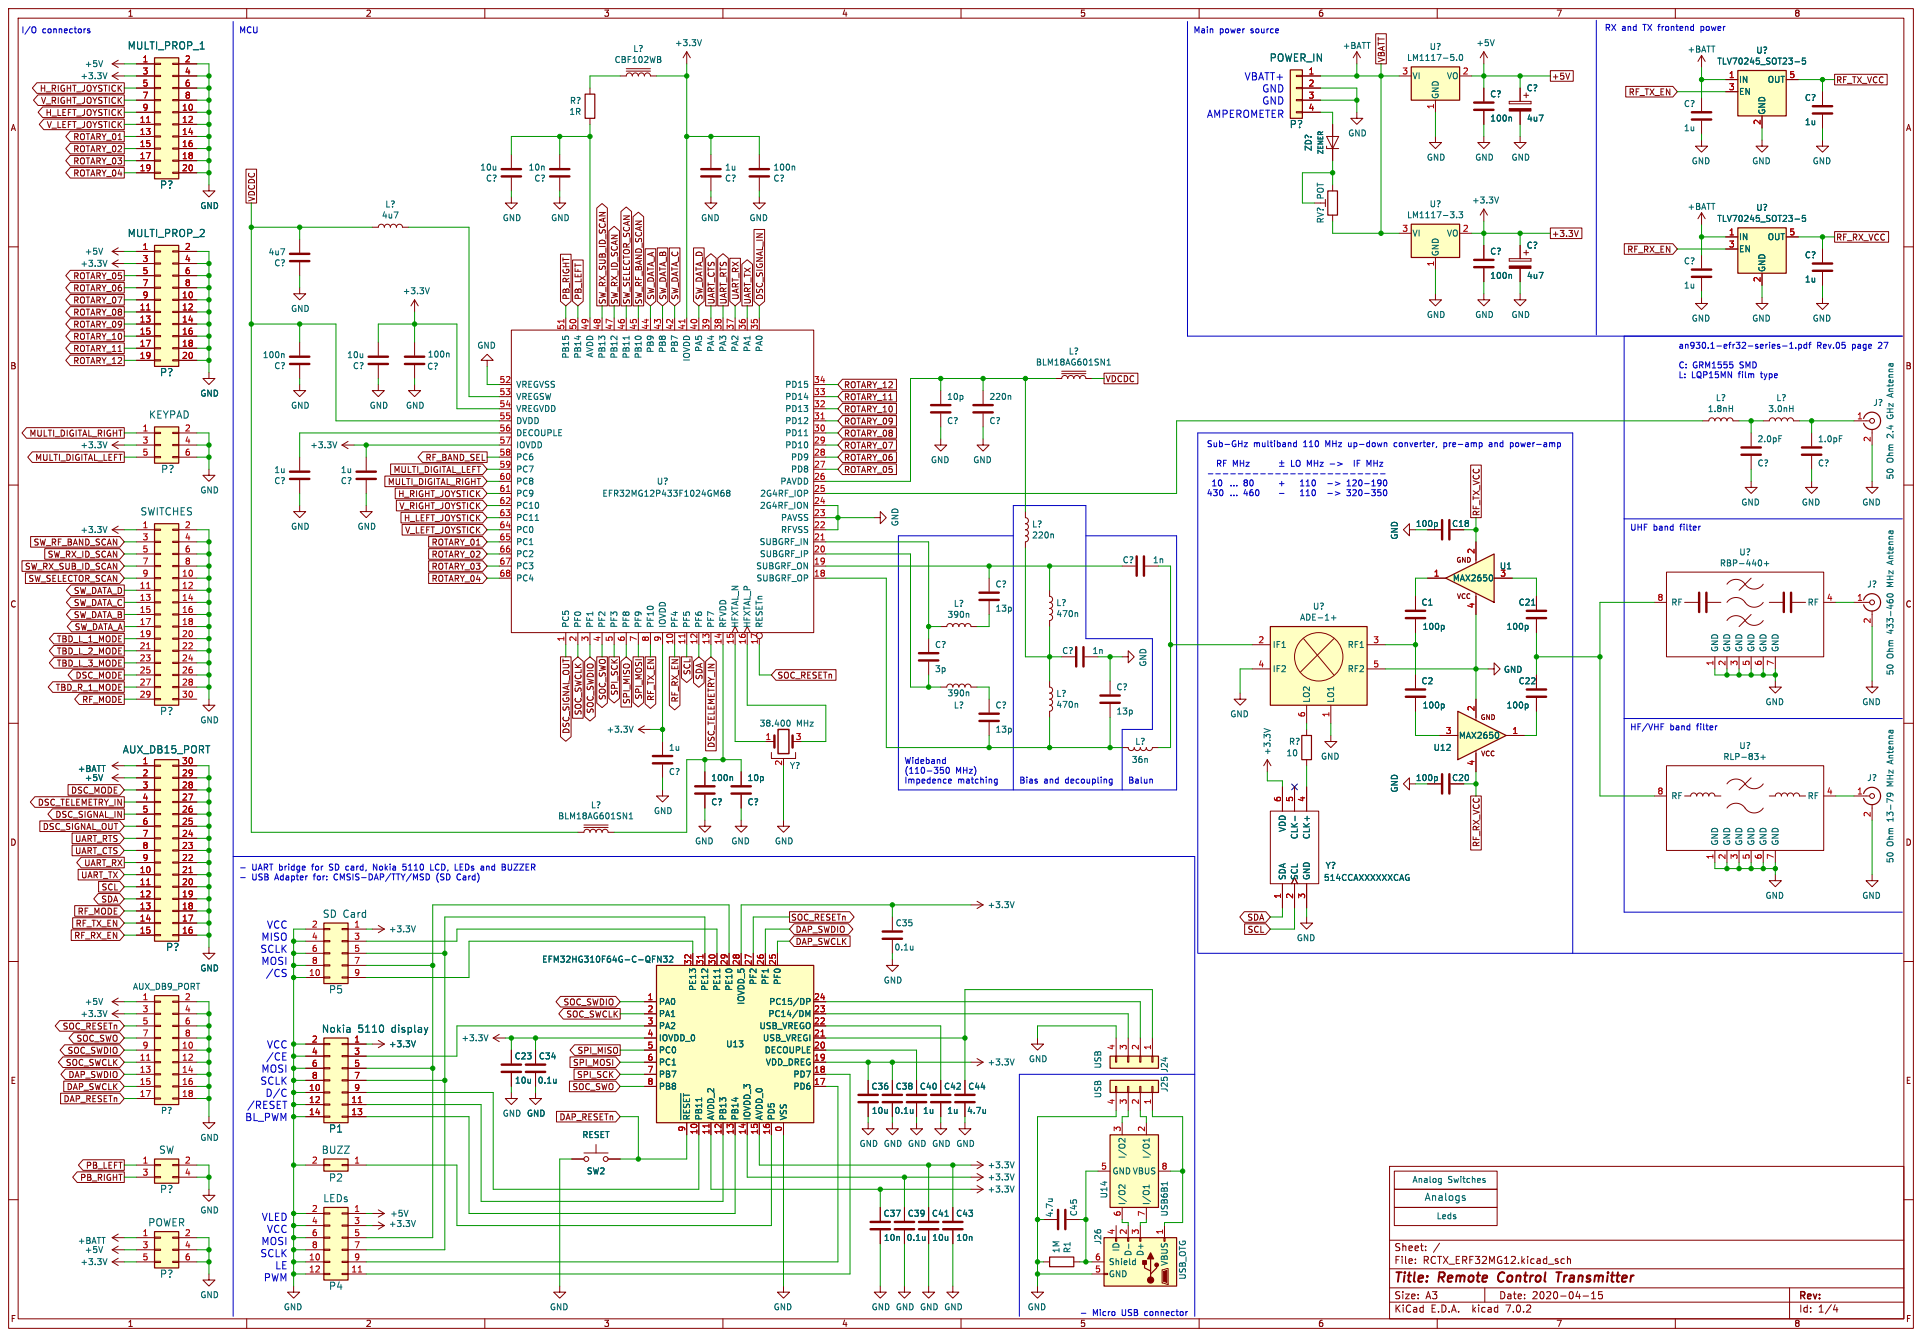
[picture p153: page 1]

Main power source VBATT+ Wideband

5 PB14 50 PB15 51 VREGVSS 52 VREGSW 53 VREGVDD 54 DVDD 55 DECOUPLE 56

UHF band filter VCC

- UART bridge for SD card, Nokia 5110 LCD, LEDs and BUZZER

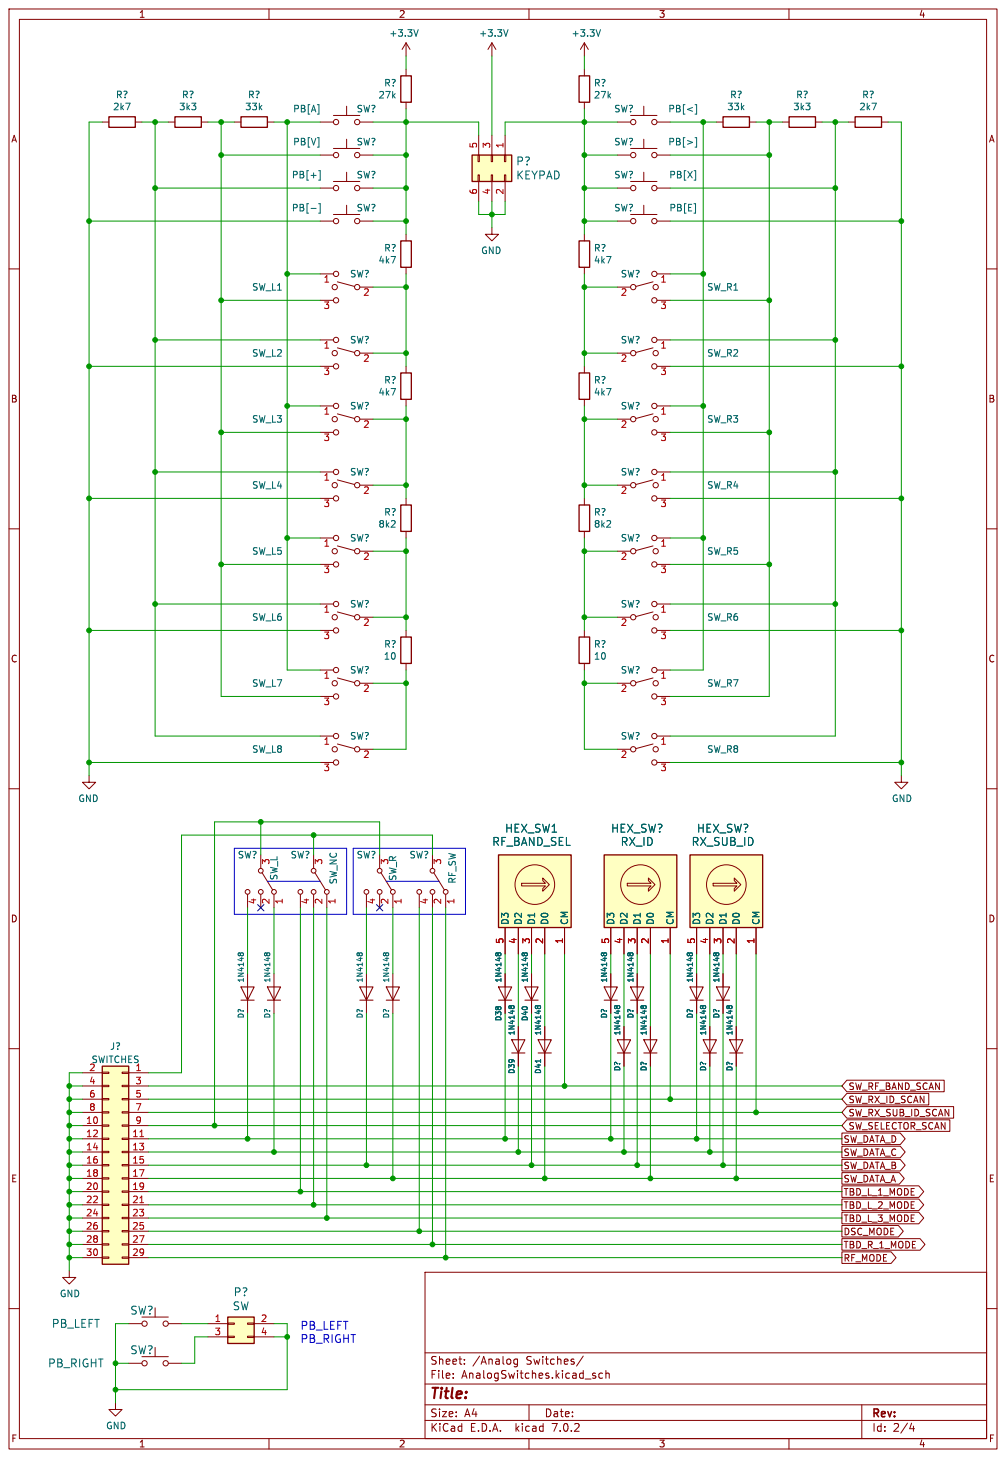
[picture p154: page 2]

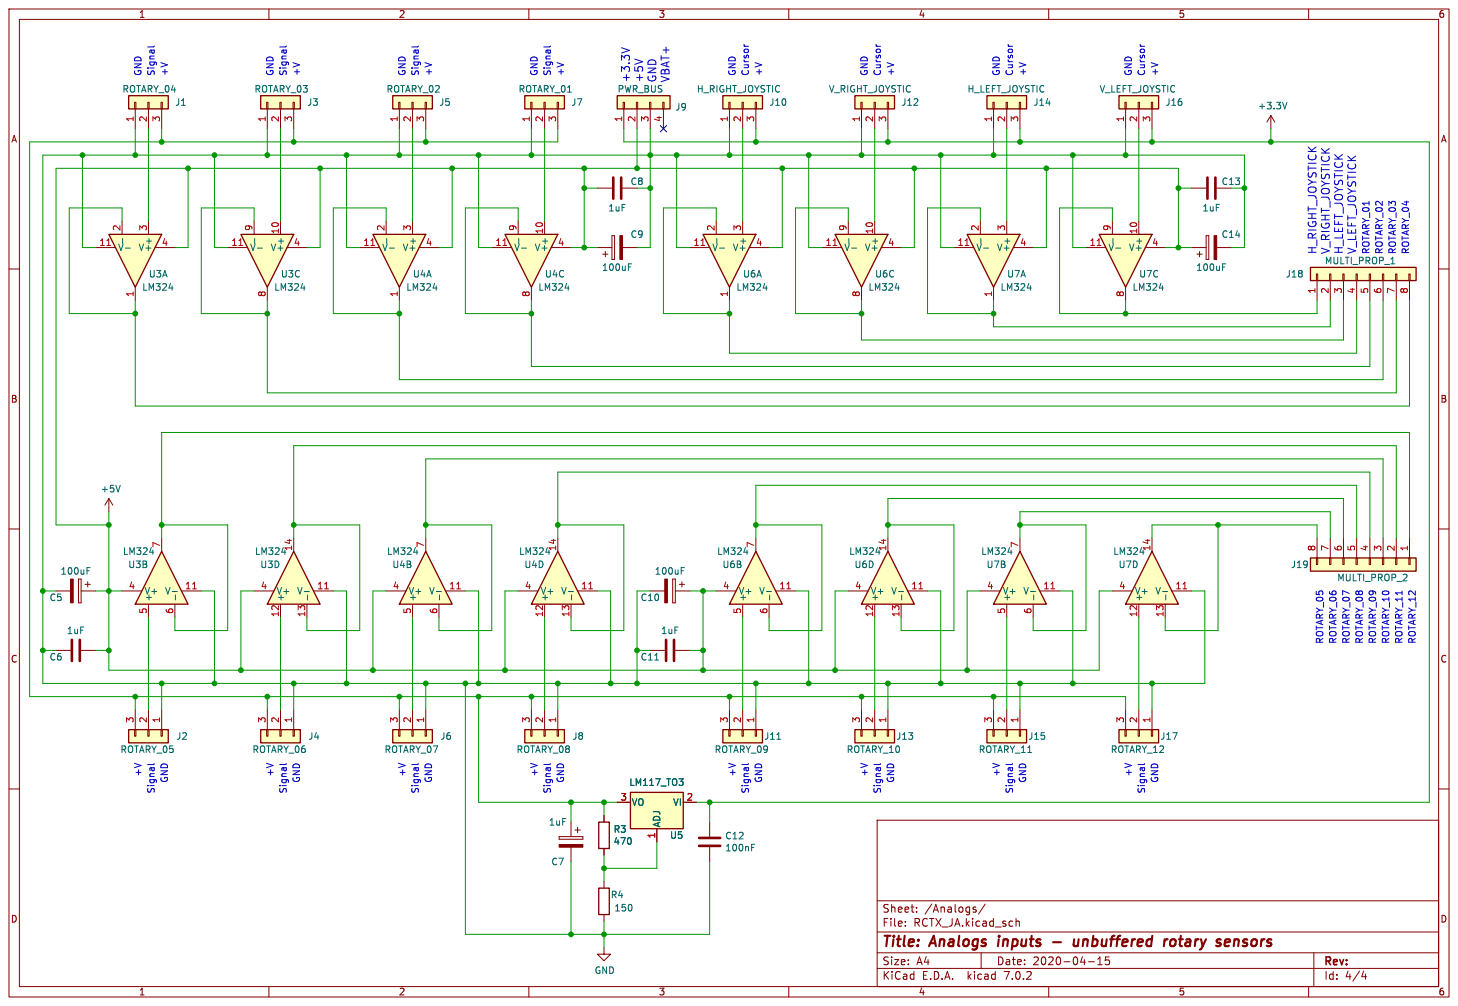
[picture p155: page 3]

Id: 4/4 Title: Analogs inputs - unbuffered rotary sensors

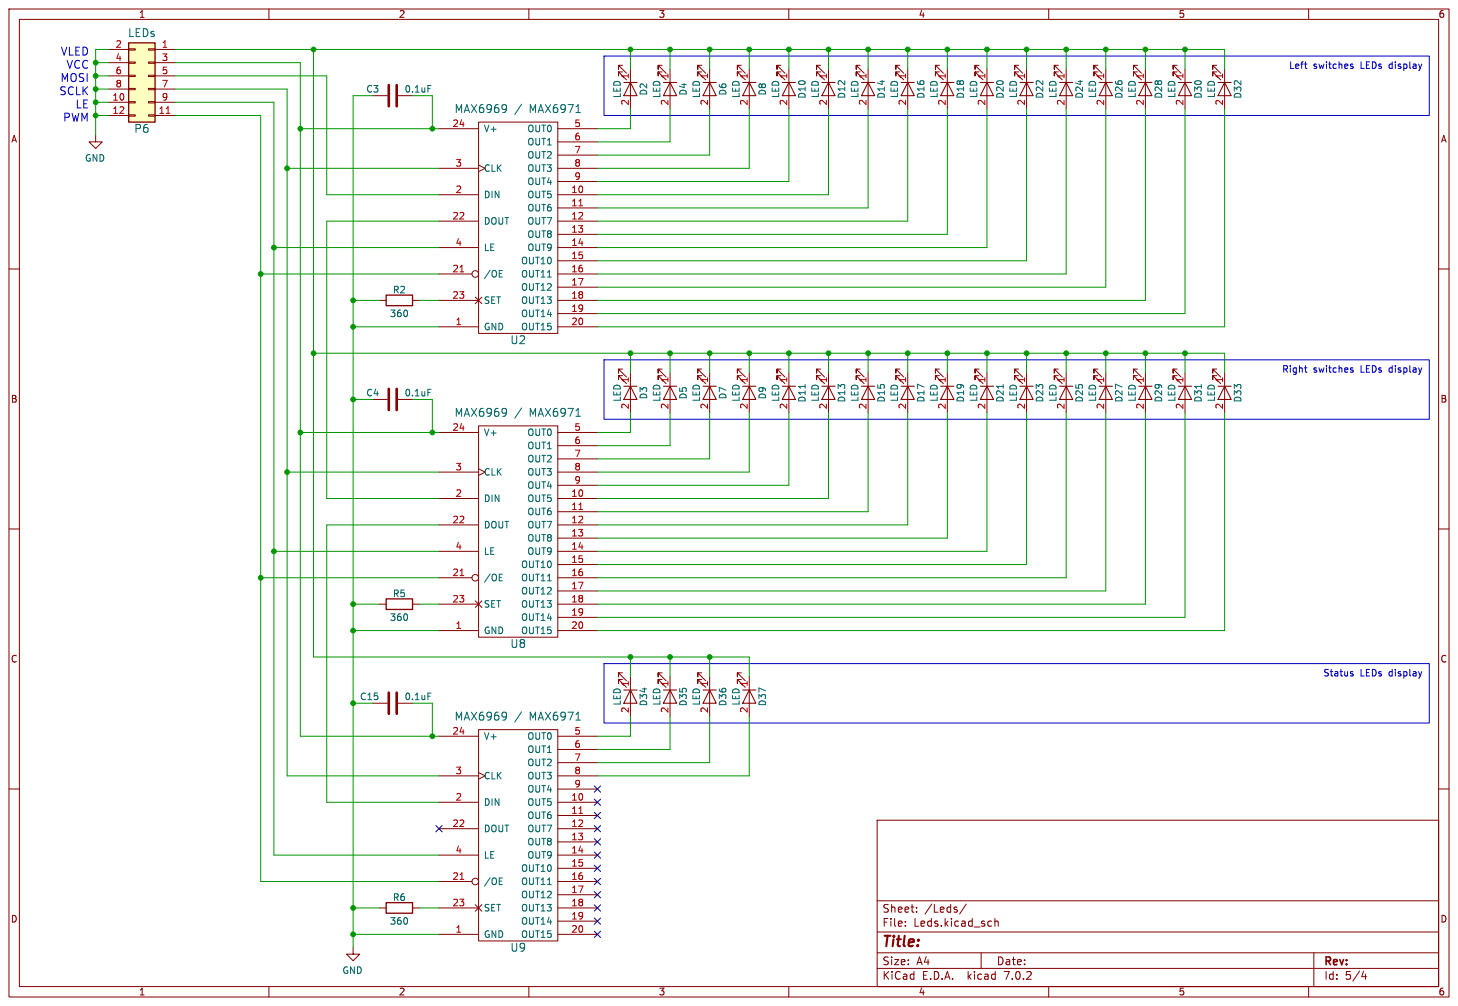
[picture p156: page 4]

Right switches LEDs display Left switches LEDs display
