fbradasc/RCTX/kicad/AnalogSwitches.kicad_sch

## KiCad design kicad/AnalogSwitches.kicad_sch (2024-01-10)

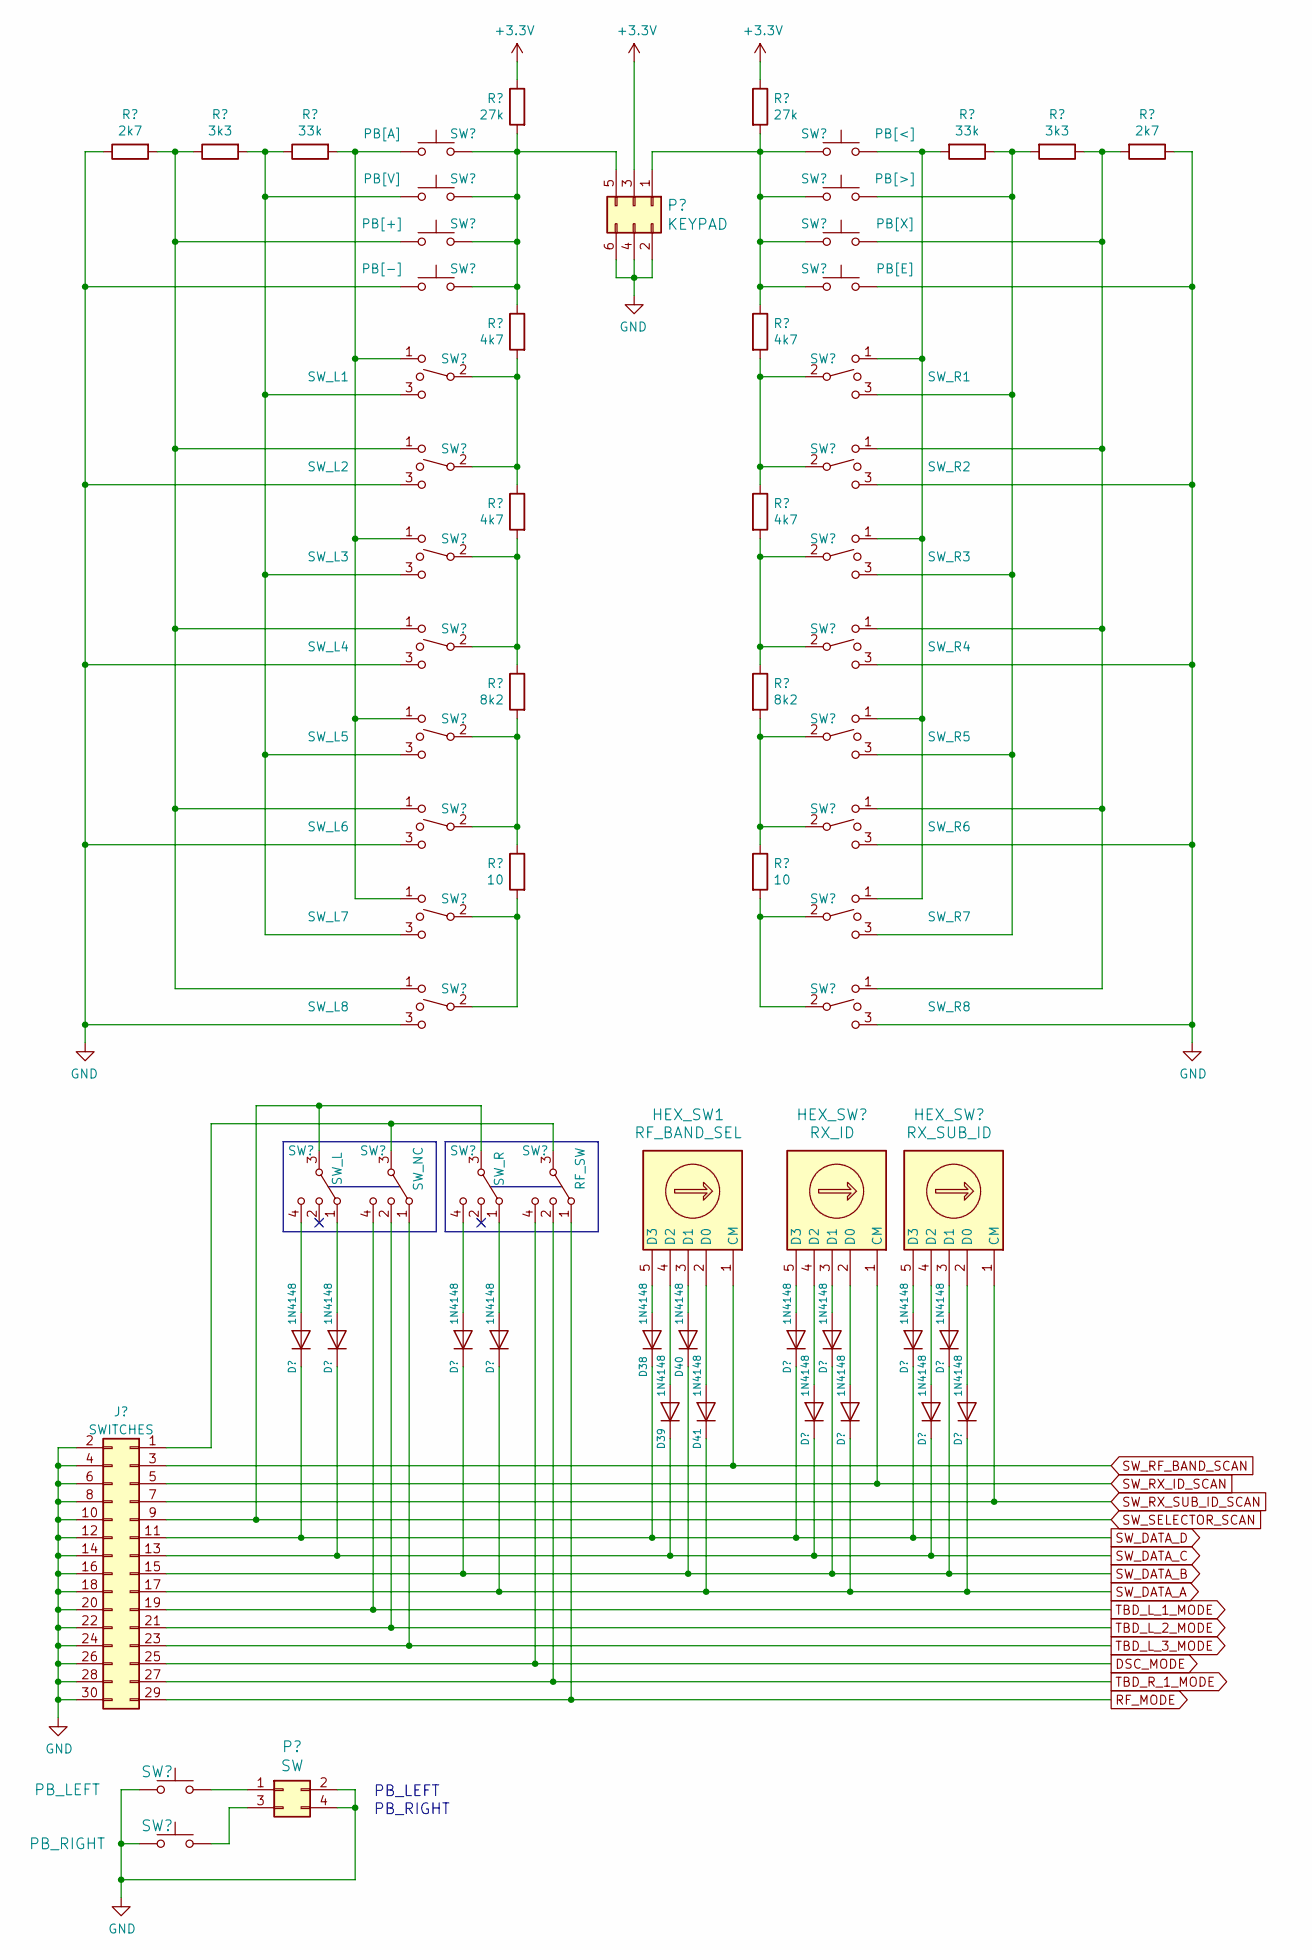
[picture p157: schematic AnalogSwitches.kicad_sch]

Parts:
D38, D39, D40, D41: 1N4148; D_5W_P5.08mm_Vertical_KathodeUp
HEX_SW1: RF_BAND_SEL; Nidec_Copal_SH-7010C

Connections:
unnamed: D38.2 (A), HEX_SW1.5 (D3)
unnamed: D39.2 (A), HEX_SW1.4 (D2)
unnamed: D40.2 (A), HEX_SW1.3 (D1)
unnamed: D41.2 (A), HEX_SW1.2 (D0)
SW_DATA_A: D41.1 (K)
SW_DATA_B: D40.1 (K)
SW_DATA_C: D39.1 (K)
SW_DATA_D: D38.1 (K)
SW_RF_BAND_SCAN: HEX_SW1.1 (CM)

Notes on the sheet:
PB_RIGHT
PB_LEFT
