fbradasc/RCTX/kicad/Leds.kicad_sch

## KiCad design kicad/Leds.kicad_sch (2024-01-10)

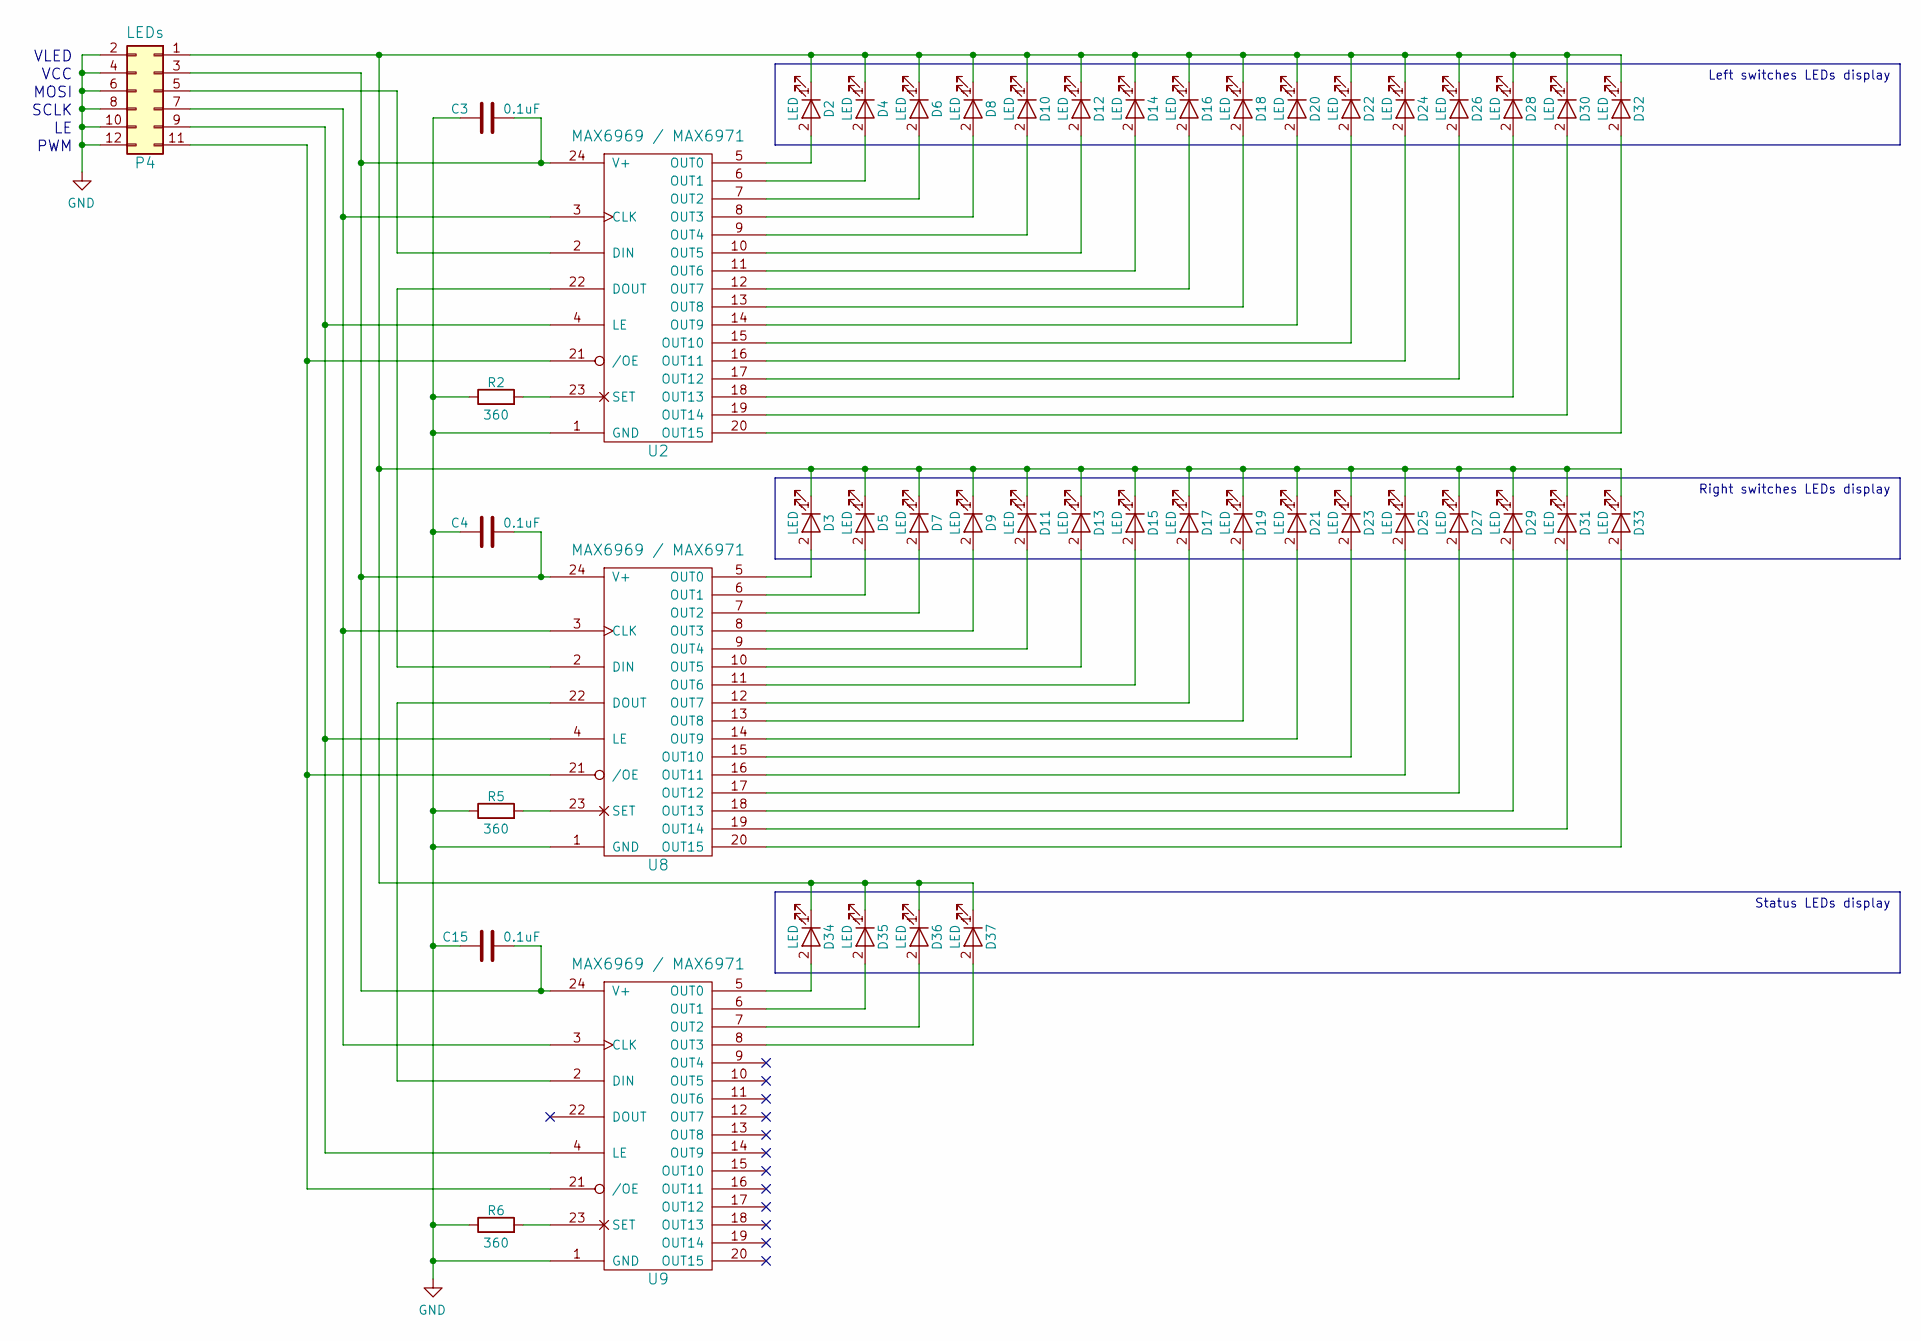
[picture p158: schematic Leds.kicad_sch]

Parts:
C3, C4, C15: 0.1uF; C_Disc_D3.0mm_W1.6mm_P2.50mm
D2, D3, D4, D5, D6, D7, D8, D9, D10, D11, D12, D13, D14, D15, D16, D17, D18, D19, D20, D21, D22, D23, D24, D25, D26, D27, D28, D29, D30, D31, D32, D33, D34, D35, D36, D37: LED; LED_D2.0mm_W4.0mm_H2.8mm_FlatTop
P4: LEDs
R2, R5, R6: 360; R_Axial_DIN0204_L3.6mm_D1.6mm_P1.90mm_Vertical
U2, U8, U9: MAX6969 / MAX6971; DIP-24_W7.62mm

Connections:
GND: C3.1, C4.1, C15.1, P4.2, P4.4, P4.6, P4.8, P4.10, P4.12, R2.1, R5.1, R6.1, U2.1 (GND), U8.1 (GND), U9.1 (GND)
unnamed: C3.2, C4.2, C15.2, P4.3, U2.24 (V+), U8.24 (V+), U9.24 (V+)
unnamed: D2.2 (A), U2.5 (OUT0)
unnamed: D3.2 (A), U8.5 (OUT0)
unnamed: D4.2 (A), U2.6 (OUT1)
unnamed: D5.2 (A), U8.6 (OUT1)
unnamed: D6.2 (A), U2.7 (OUT2)
unnamed: D7.2 (A), U8.7 (OUT2)
unnamed: D8.2 (A), U2.8 (OUT3)
unnamed: D9.2 (A), U8.8 (OUT3)
unnamed: D2.1 (K), D3.1 (K), D4.1 (K), D5.1 (K), D6.1 (K), D7.1 (K), D8.1 (K), D9.1 (K), D10.1 (K), D11.1 (K), D12.1 (K), D13.1 (K), D14.1 (K), D15.1 (K), D16.1 (K), D17.1 (K), D18.1 (K), D19.1 (K), D20.1 (K), D21.1 (K), D22.1 (K), D23.1 (K), D24.1 (K), D25.1 (K), D26.1 (K), D27.1 (K), D28.1 (K), D29.1 (K), D30.1 (K), D31.1 (K), D32.1 (K), D33.1 (K), D34.1 (K), D35.1 (K), D36.1 (K), D37.1 (K), P4.1
unnamed: D10.2 (A), U2.9 (OUT4)
unnamed: D11.2 (A), U8.9 (OUT4)
unnamed: D12.2 (A), U2.10 (OUT5)
unnamed: D13.2 (A), U8.10 (OUT5)
unnamed: D14.2 (A), U2.11 (OUT6)
unnamed: D15.2 (A), U8.11 (OUT6)
unnamed: D16.2 (A), U2.12 (OUT7)
unnamed: D17.2 (A), U8.12 (OUT7)
unnamed: D18.2 (A), U2.13 (OUT8)
unnamed: D19.2 (A), U8.13 (OUT8)
unnamed: D20.2 (A), U2.14 (OUT9)
unnamed: D21.2 (A), U8.14 (OUT9)
unnamed: D22.2 (A), U2.15 (OUT10)
unnamed: D23.2 (A), U8.15 (OUT10)
unnamed: D24.2 (A), U2.16 (OUT11)
unnamed: D25.2 (A), U8.16 (OUT11)
unnamed: D26.2 (A), U2.17 (OUT12)
unnamed: D27.2 (A), U8.17 (OUT12)
unnamed: D28.2 (A), U2.18 (OUT13)
unnamed: D29.2 (A), U8.18 (OUT13)
unnamed: D30.2 (A), U2.19 (OUT14)
unnamed: D31.2 (A), U8.19 (OUT14)
unnamed: D32.2 (A), U2.20 (OUT15)
unnamed: D33.2 (A), U8.20 (OUT15)
unnamed: D34.2 (A), U9.5 (OUT0)
unnamed: D35.2 (A), U9.6 (OUT1)
unnamed: D36.2 (A), U9.7 (OUT2)
unnamed: D37.2 (A), U9.8 (OUT3)
unnamed: P4.5, U2.2 (DIN)
unnamed: P4.7, U2.3 (CLK), U8.3 (CLK), U9.3 (CLK)
unnamed: P4.9, U2.4 (LE), U8.4 (LE), U9.4 (LE)
unnamed: P4.11, U2.21 (/OE), U8.21 (/OE), U9.21 (/OE)
unnamed: R2.2, U2.23 (SET)
unnamed: R5.2, U8.23 (SET)
unnamed: R6.2, U9.23 (SET)
unnamed: U2.22 (DOUT), U8.2 (DIN)
unnamed: U8.22 (DOUT), U9.2 (DIN)

Notes on the sheet:
MOSI
Status LEDs display
VLED
Right switches LEDs display
Left switches LEDs display
SCLK
PWM
VCC
