fbradasc/RCTX/kicad/RCRX_ERF32MG12.kicad_sch

## KiCad design kicad/RCRX_ERF32MG12.kicad_sch (2024-01-19)

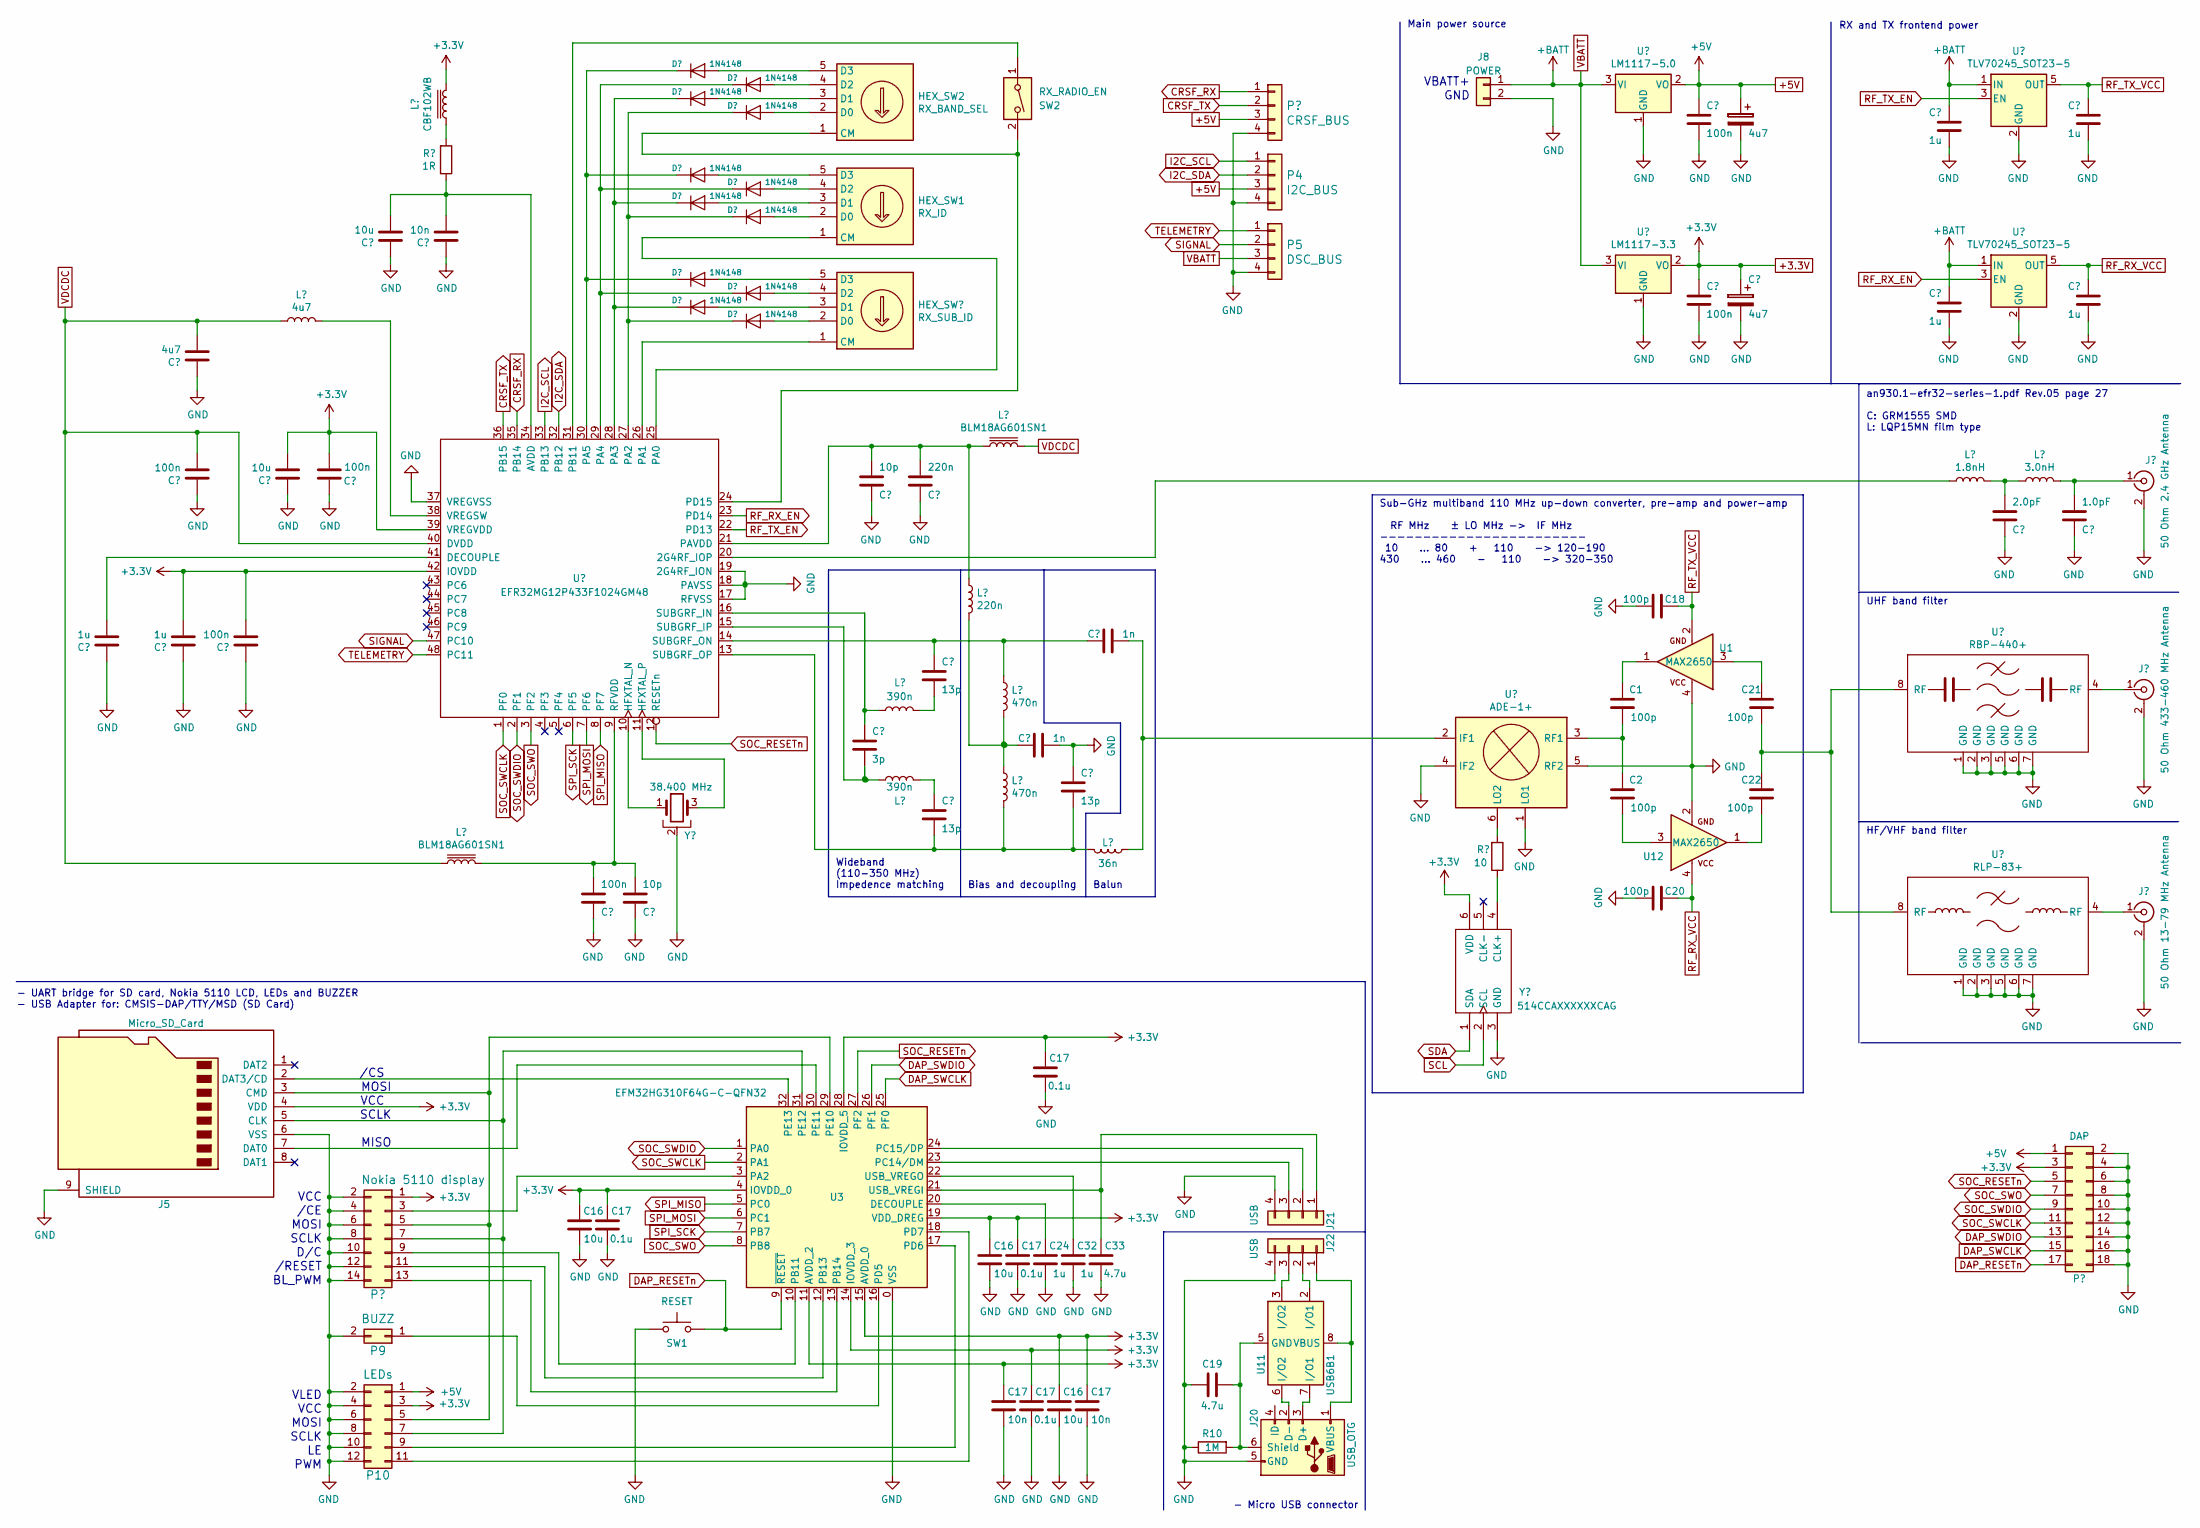
[picture p159: schematic RCRX_ERF32MG12.kicad_sch]

Parts:
C1, C2, C18, C21, C22: 100p
C9, C10: 100n
C11, C12: 4u7
C15, C16, C20, C24, C32: 1u
C17: 10n
C19, C33: 4.7u
D1, D2, D3, D4, D5, D6, D7, D8, D9, D10, D11, D12: 1N4148; D_5W_P5.08mm_Vertical_KathodeUp
HEX_SW1: RX_ID
HEX_SW2: RX_BAND_SEL
J2: 50 Ohm 2.4 GHz Antenna
J3: 50 Ohm 433-460 MHz Antenna
J4: 50 Ohm 13-79 MHz Antenna
J5: Micro_SD_Card
J8: POWER
J20: USB_OTG
J21, J22: USB
L1: 1.8nH
L2: 3.0nH
P1: DAP
P2: Nokia 5110 display
P4: I2C_BUS
P5: DSC_BUS
P9: BUZZ
P10: LEDs
R2: 10
R10: 1M
SW1: RESET
SW2: RX_RADIO_EN
U1, U12: MAX2650; SOT-143
U2: LM1117-5.0
U3: EFM32HG310F64G-C-QFN32; QFN-32-1EP_6x6mm_P0.65mm_EP4.4x4.4mm
U4: LM1117-3.3
U8: RBP-440+
U9: RLP-83+
U10: TLV70245_SOT23-5; SOT-23-5
U11: USB6B1; SOIC-8_3.9x4.9mm_P1.27mm
Y1: 514CCAXXXXXXCAG; Si500D; Manufacturer_Part_Number Si500D; Mouser Part Number N/A

Connections:
+3.3V: C10.1, C12.1, C16.2, C17.2, J5.4 (VDD), P1.3, P2.1, P10.3, U3.4 (IOVDD_0), U3.11 (AVDD_2), U3.14 (IOVDD_3), U3.15 (AVDD_0), U3.19 (VDD_DREG), U3.28 (IOVDD_5), U4.2 (VO), Y1.6 (VDD)
+5V: C9.1, C11.1, P1.1, P4.3, P10.1, U2.2 (VO)
+BATT: C15.1, C16.1, J8.1, P5.3, U2.3 (VI), U4.3 (VI), U10.1 (IN), U11.1 (IN)
DAP_RESETn: P1.17, SW1.2, U3.9 (~RESET)
DAP_SWCLK: P1.15, U3.25 (PF0)
DAP_SWDIO: P1.13, U3.26 (PF1)
GND: C9.2, C10.2, C11.2, C12.2, C15.2, C16.1, C16.2, C17.1, C18.1, C18.2, C19.1, C19.2, C20.2, C24.1, C32.1, C33.1, J2.2 (Ext), J3.2 (Ext), J4.2 (Ext), J5.6 (VSS), J5.9 (SHIELD), J8.2, J20.5 (GND), J21.4, J22.4, P1.2, P1.4, P1.6, P1.8, P1.10, P1.12, P1.14, P1.16, P1.18, P2.2, P2.4, P2.6, P2.8, P2.10, P2.12, P2.14, P9.2, P10.2, P10.4, P10.6, P10.8, P10.10, P10.12, R10.1, SW1.1, U1.1 (LO1), U1.4 (IF2), U1.5 (RF2), U2.1 (GND), U3.0 (VSS), U4.1 (GND), U8.1 (GND), U8.2 (GND), U8.3 (GND), U8.5 (GND), U8.6 (GND), U8.7 (GND), U9.1 (GND), U9.2 (GND), U9.3 (GND), U9.5 (GND), U9.6 (GND), U9.7 (GND), U10.2 (GND), U11.2 (GND), U12.2 (GND), Y1.3 (GND)
I2C_SCL: P4.1
I2C_SDA: P4.2
unnamed: C1.1, C2.2, U1.3 (RF1)
unnamed: C1.2, U1.1 (LO1)
unnamed: C2.1, U12.3 (IN)
unnamed: C17.2, L1.1, L2.2
unnamed: C18.2, J2.1 (In), L2.1
unnamed: C19.2, J20.6 (Shield), R10.2, U11.4 (NC), U11.5 (OUT)
unnamed: C21.1, U1.3 (RF1)
unnamed: C21.2, C22.1, U8.8 (RF), U9.8 (RF)
unnamed: C22.2, U12.1 (OUT)
unnamed: C24.2, U3.20 (DECOUPLE)
unnamed: C32.2, U3.22 (USB_VREGO)
unnamed: C33.2, J21.1, U3.21 (USB_VREGI)
unnamed: D1.1 (K), D5.1 (K), D9.1 (K)
unnamed: D1.2 (A), HEX_SW2.5 (D3)
unnamed: D2.2 (A), HEX_SW2.3 (D1)
unnamed: D3.2 (A), HEX_SW2.4 (D2)
unnamed: D4.2 (A), HEX_SW2.2 (D0)
unnamed: D9.2 (A), HEX_SW1.5 (D3)
unnamed: D2.1 (K), D6.1 (K), D10.1 (K)
unnamed: D10.2 (A), HEX_SW1.3 (D1)
unnamed: D3.1 (K), D7.1 (K), D11.1 (K)
unnamed: D11.2 (A), HEX_SW1.4 (D2)
unnamed: D4.1 (K), D8.1 (K), D12.1 (K)
unnamed: D12.2 (A), HEX_SW1.2 (D0)
unnamed: HEX_SW2.1 (CM), SW2.2
unnamed: J3.1 (In), U8.4 (RF)
unnamed: J4.1 (In), U9.4 (RF)
unnamed: J5.2 (DAT3/CD), U3.32 (PE13)
unnamed: J5.3 (CMD), P2.5, P10.5, U3.29 (PE10)
unnamed: J5.5 (CLK), P2.7, P10.7, U3.31 (PE12)
unnamed: J5.7 (DAT0), U3.30 (PE11)
unnamed: J20.1 (VBUS), J22.1, U11.1 (IN), U11.8 (VBUS)
unnamed: J20.2 (D-), U11.6 (I/O2)
unnamed: J20.3 (D+), U11.7 (I/O1)
unnamed: J21.2, U3.24 (PC15/DP)
unnamed: J21.3, U3.23 (PC14/DM)
unnamed: J22.2, U11.2 (GND)
unnamed: J22.3, U11.3 (EN)
unnamed: P2.3, U3.3 (PA2)
unnamed: P2.9, U3.10 (PB11)
unnamed: P2.11, U3.12 (PB13)
unnamed: P2.13, U3.13 (PB14)
unnamed: P4.4, P5.4
unnamed: P9.1, U3.16 (PD5)
unnamed: P10.9, U3.17 (PD6)
unnamed: P10.11, U3.18 (PD7)
unnamed: R2.1, Y1.4 (CLK+)
unnamed: R2.2, U1.6 (LO2)
RF_RX_EN: U11.3 (EN)
RF_RX_VCC: C20.1, U11.5 (OUT), U12.4 (VCC)
RF_TX_EN: U10.3 (EN)
RF_TX_VCC: C18.1, C19.1, U1.2 (IF1), U10.5 (OUT)
SCL: Y1.2 (SCL)
SDA: Y1.1 (SDA)
SIGNAL: P5.2
SOC_RESETn: P1.5, U3.27 (PF2)
SOC_SWCLK: P1.11, U3.2 (PA1)
SOC_SWDIO: P1.9, U3.1 (PA0)
SOC_SWO: P1.7, U3.8 (PB8)
SPI_MISO: U3.5 (PC0)
SPI_MOSI: U3.6 (PC1)
SPI_SCK: U3.7 (PB7)
TELEMETRY: P5.1

Notes on the sheet:
/CS
VCC
SCLK
Balun
MOSI
/CE
PWM
VLED
VBATT+
- Micro USB connector
MISO
Bias and decoupling
Wideband (110-350 MHz) Impedence matching
/RESET
BL_PWM
GND
D/C
RX and TX frontend power
UHF band filter
- UART bridge for SD card, Nokia 5110 LCD, LEDs and BUZZER - USB Adapter for: CMSIS-DAP/TTY/MSD (SD Card)
Sub-GHz multiband 110 MHz up-down converter, pre-amp and power-amp RF MHz ± LO MHz -> IF MHz ------------------------ 10 ... 80 + 110 -> 120-190 430 ... 460 - 110 -> 320-350
Main power source
an930.1-efr32-series-1.pdf Rev.05 page 27 C: GRM1555 SMD L: LQP15MN film type
HF/VHF band filter
