fbradasc/RCTX/kicad/RCTX_ERF32MG12.kicad_sch

## KiCad design kicad/RCTX_ERF32MG12.kicad_sch (2024-01-19)

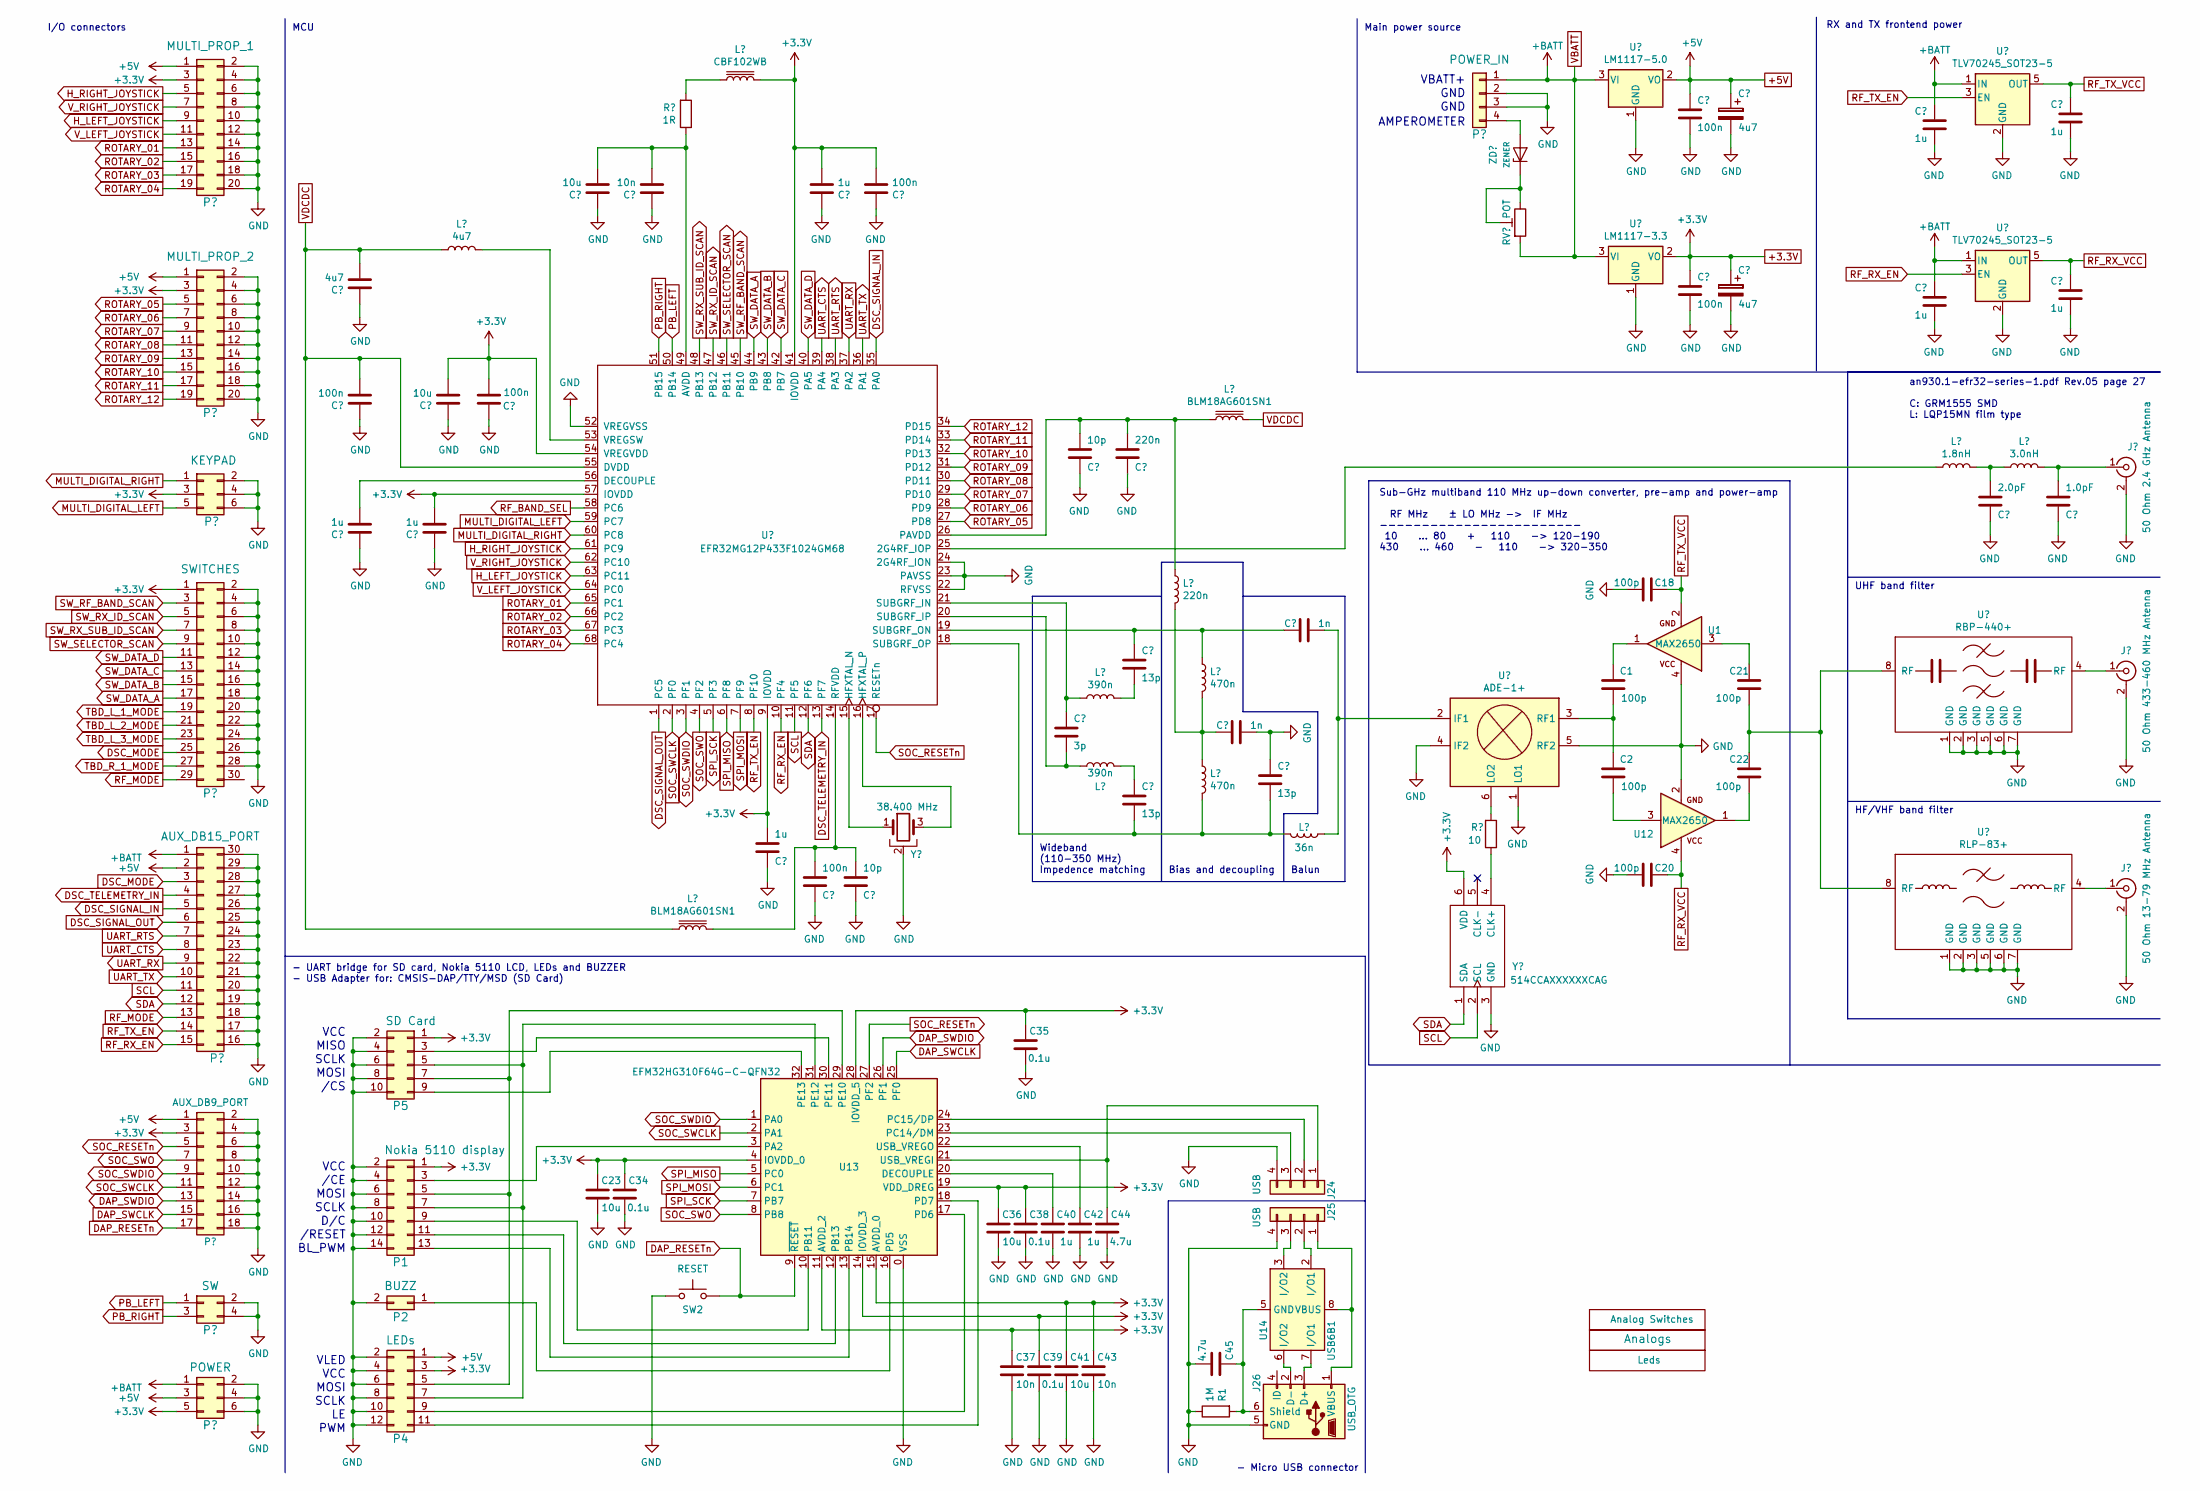
[picture p160: schematic RCTX_ERF32MG12.kicad_sch]

Parts:
C1, C2, C18, C20, C21, C22: 100p
C23, C36, C41: 10u
C34, C35, C38, C39: 0.1u
C37, C43: 10n
C40, C42: 1u
C44, C45: 4.7u
J24, J25: USB
J26: USB_OTG
P1: Nokia 5110 display
P2: BUZZ
P4: LEDs
P5: SD Card
R1: 1M
SW2: RESET
U1, U12: MAX2650; SOT-143
U13: EFM32HG310F64G-C-QFN32; QFN-32-1EP_6x6mm_P0.65mm_EP4.4x4.4mm
U14: USB6B1; SOIC-8_3.9x4.9mm_P1.27mm

Connections:
+3.3V: C23.2, C34.2, C35.2, C36.2, C37.2, C38.2, C39.2, C41.2, C43.2, P1.1, P4.3, P5.1, U13.4 (IOVDD_0), U13.11 (AVDD_2), U13.14 (IOVDD_3), U13.15 (AVDD_0), U13.19 (VDD_DREG), U13.28 (IOVDD_5)
+5V: P4.1
DAP_RESETn: SW2.2, U13.9 (~RESET)
DAP_SWCLK: U13.25 (PF0)
DAP_SWDIO: U13.26 (PF1)
GND: C18.2, C20.2, C23.1, C34.1, C35.1, C36.1, C37.1, C38.1, C39.1, C40.1, C41.1, C42.1, C43.1, C44.1, C45.1, J24.4, J25.4, J26.5 (GND), P1.2, P1.4, P1.6, P1.8, P1.10, P1.12, P1.14, P2.2, P4.2, P4.4, P4.6, P4.8, P4.10, P4.12, P5.2, P5.4, P5.6, P5.8, P5.10, R1.1, SW2.1, U1.4 (VCC), U12.2 (GND), U13.0 (VSS)
unnamed: C1.1, C2.2
unnamed: C1.2, U1.1 (OUT)
unnamed: C2.1, U12.3 (IN)
unnamed: C21.1, U1.3 (IN)
unnamed: C21.2, C22.1
unnamed: C22.2, U12.1 (OUT)
unnamed: C40.2, U13.20 (DECOUPLE)
unnamed: C42.2, U13.22 (USB_VREGO)
unnamed: C44.2, J24.1, U13.21 (USB_VREGI)
unnamed: C45.2, J26.6 (Shield), R1.2, U14.4 (GND), U14.5 (GND)
unnamed: J24.2, U13.24 (PC15/DP)
unnamed: J24.3, U13.23 (PC14/DM)
unnamed: J25.1, J26.1 (VBUS), U14.1 (VBUS), U14.8 (VBUS)
unnamed: J25.2, U14.2 (I/O1)
unnamed: J25.3, U14.3 (I/O2)
unnamed: J26.2 (D-), U14.6 (I/O2)
unnamed: J26.3 (D+), U14.7 (I/O1)
unnamed: P1.3, U13.3 (PA2)
unnamed: P1.5, P4.5, P5.7, U13.29 (PE10)
unnamed: P1.7, P4.7, P5.5, U13.31 (PE12)
unnamed: P1.9, U13.10 (PB11)
unnamed: P1.11, U13.12 (PB13)
unnamed: P1.13, U13.13 (PB14)
unnamed: P2.1, U13.16 (PD5)
unnamed: P4.9, U13.17 (PD6)
unnamed: P4.11, U13.18 (PD7)
unnamed: P5.3, U13.30 (PE11)
unnamed: P5.9, U13.32 (PE13)
RF_RX_VCC: C20.1, U12.4 (VCC)
RF_TX_VCC: C18.1, U1.2 (GND)
SOC_RESETn: U13.27 (PF2)
SOC_SWCLK: U13.2 (PA1)
SOC_SWDIO: U13.1 (PA0)
SOC_SWO: U13.8 (PB8)
SPI_MISO: U13.5 (PC0)
SPI_MOSI: U13.6 (PC1)
SPI_SCK: U13.7 (PB7)

Notes on the sheet:
PWM
Wideband (110-350 MHz) Impedence matching
SCLK
/RESET
/CE
VCC
VBATT+
MOSI
Main power source
UHF band filter
MCU
RX and TX frontend power
/CS
GND
BL_PWM
HF/VHF band filter
Sub-GHz multiband 110 MHz up-down converter, pre-amp and power-amp RF MHz ± LO MHz -> IF MHz ------------------------ 10 ... 80 + 110 -> 120-190 430 ... 460 - 110 -> 320-350
I/O connectors
MISO
AMPEROMETER
- UART bridge for SD card, Nokia 5110 LCD, LEDs and BUZZER - USB Adapter for: CMSIS-DAP/TTY/MSD (SD Card)
- Micro USB connector
VLED
D/C
Bias and decoupling
an930.1-efr32-series-1.pdf Rev.05 page 27 C: GRM1555 SMD L: LQP15MN film type
Balun
