fbradasc/RCTX/kicad/RCTX_JA.kicad_sch

## KiCad design kicad/RCTX_JA.kicad_sch (2024-01-10)

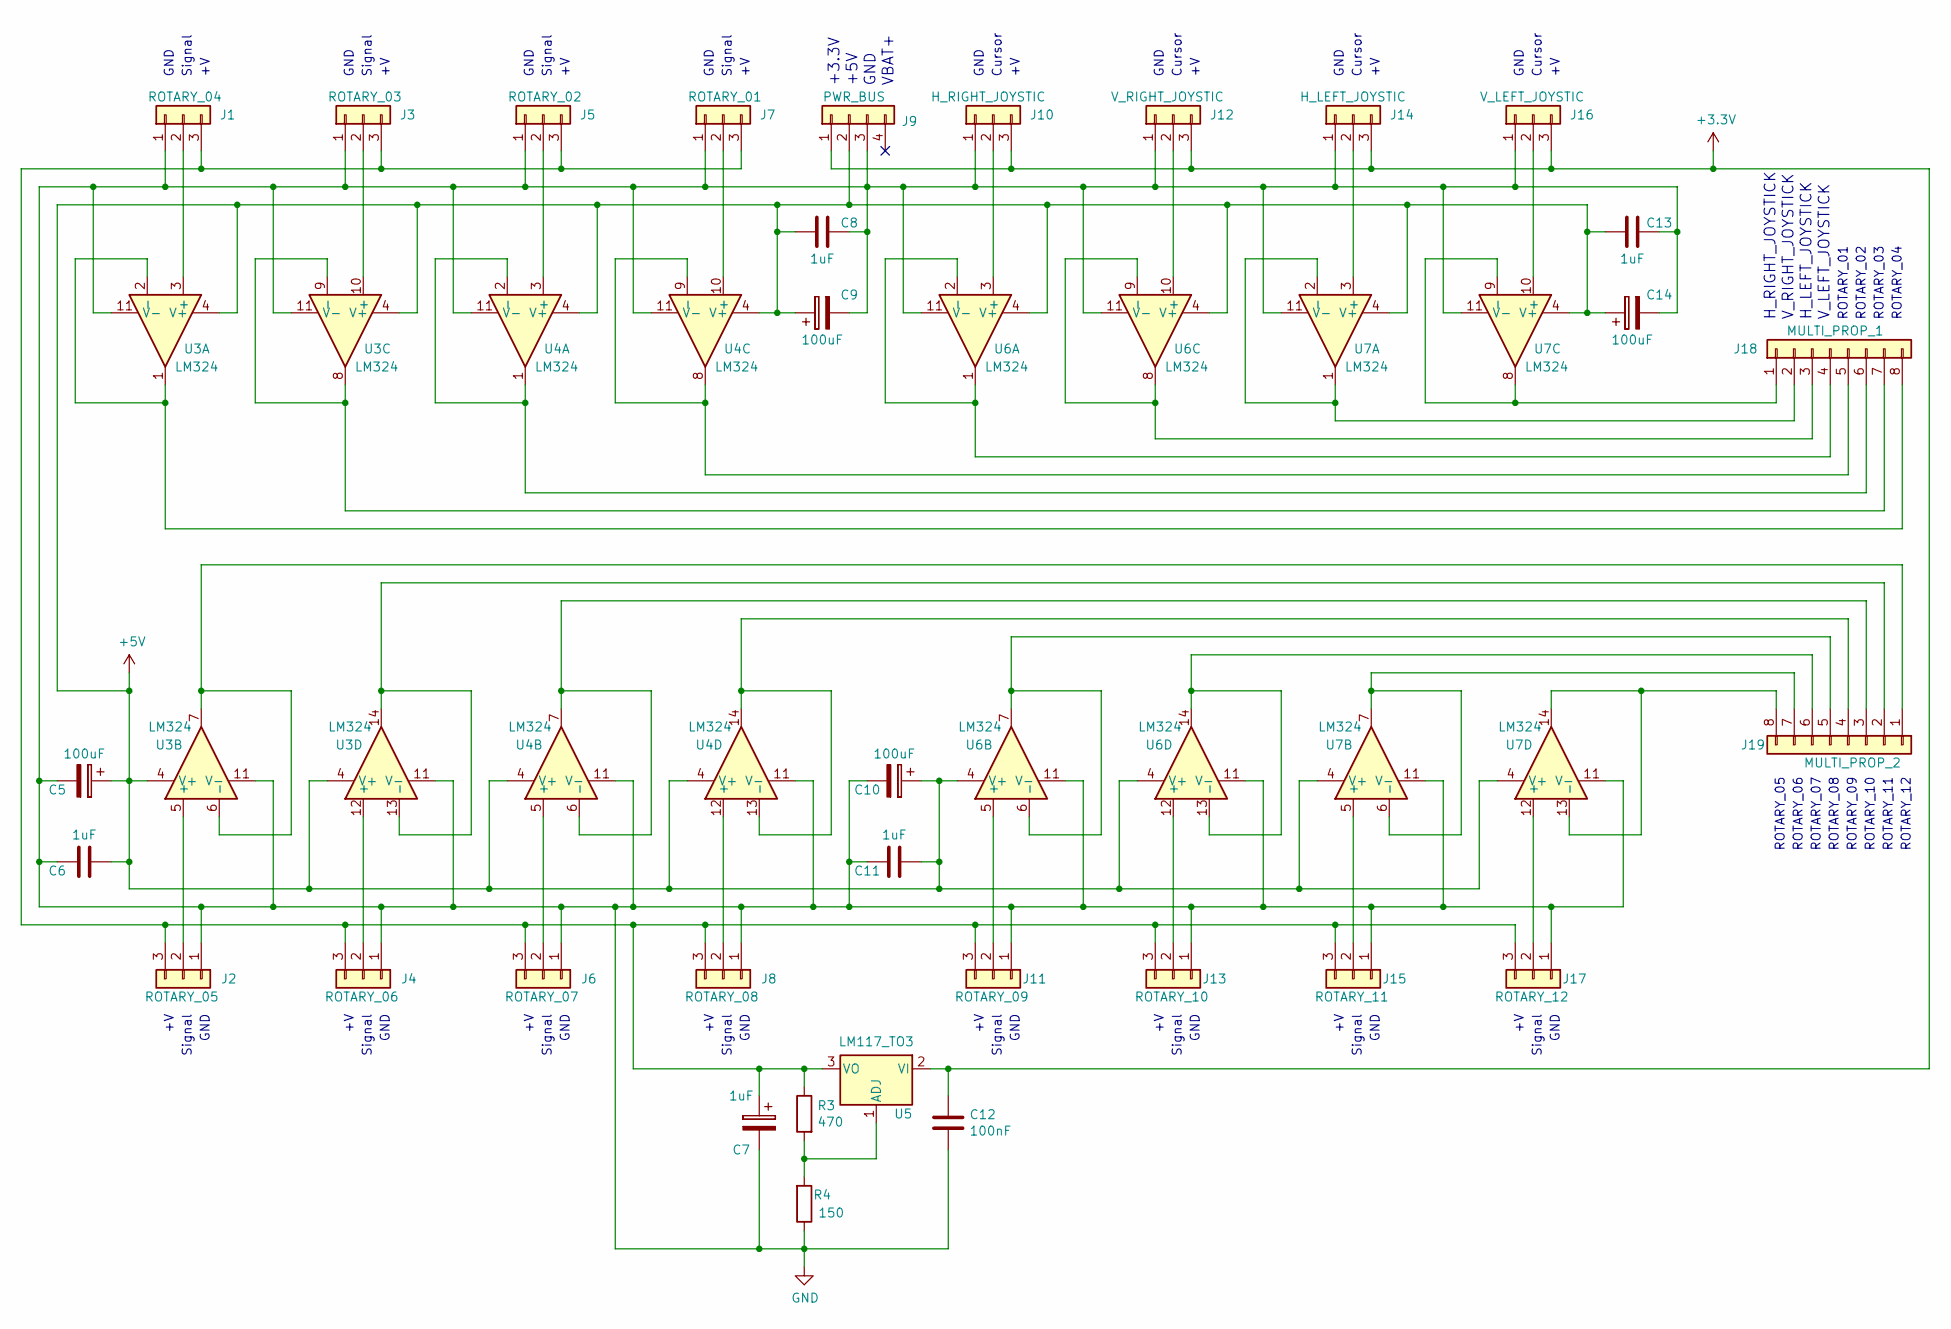
[picture p161: schematic RCTX_JA.kicad_sch]

Parts:
C5, C9, C10, C14: 100uF; CP_Radial_D5.0mm_P2.50mm
C6, C8, C11, C13: 1uF; C_Disc_D3.0mm_W1.6mm_P2.50mm
C7: 1uF; CP_Radial_D5.0mm_P2.50mm
C12: 100nF; C_Disc_D3.0mm_W1.6mm_P2.50mm
J1: ROTARY_04; SRV_1
J2: ROTARY_05; SRV_1
J3: ROTARY_03; SRV_1
J4: ROTARY_06; SRV_1
J5: ROTARY_02; SRV_1
J6: ROTARY_07; SRV_1
J7: ROTARY_01; SRV_1
J8: ROTARY_08; SRV_1
J9: PWR_BUS; SL-104-X-XX_1x04
J10: H_RIGHT_JOYSTIC; SRV_1
J11: ROTARY_09; SRV_1
J12: V_RIGHT_JOYSTIC; SRV_1
J13: ROTARY_10; SRV_1
J14: H_LEFT_JOYSTIC; SRV_1
J15: ROTARY_11; SRV_1
J16: V_LEFT_JOYSTIC; SRV_1
J17: ROTARY_12; SRV_1
J18: MULTI_PROP_1; SL-108-X-XX_1x08
J19: MULTI_PROP_2; SL-108-X-XX_1x08
R3: 470; R_Axial_DIN0204_L3.6mm_D1.6mm_P1.90mm_Vertical
R4: 150; R_Axial_DIN0204_L3.6mm_D1.6mm_P1.90mm_Vertical
U3, U4, U6, U7: LM324; DIP-14_W7.62mm
U5: LM117_TO3; TO-92_Inline_Narrow_Oval

Connections:
+3.3V: C12.1, J9.1, J10.3, J12.3, J14.3, J16.3, U5.2 (VI)
+5V: C5.1, C6.2, C8.2, C9.1, C10.1, C11.2, C13.2, C14.1, J9.2, U3.4 (V+), U4.4 (V+), U6.4 (V+), U7.4 (V+)
GND: C5.2, C6.1, C7.2, C8.1, C9.2, C10.2, C11.1, C12.2, C13.1, C14.2, J1.1, J2.1, J3.1, J4.1, J5.1, J6.1, J7.1, J8.1, J9.3, J10.1, J11.1, J12.1, J13.1, J14.1, J15.1, J16.1, J17.1, R4.1, U3.11 (V-), U4.11 (V-), U6.11 (V-), U7.11 (V-)
unnamed: C7.1, J1.3, J2.3, J3.3, J4.3, J5.3, J6.3, J7.3, J8.3, J11.3, J13.3, J15.3, J17.3, R3.1, U5.3 (VO)
unnamed: J1.2, U3.3 (+)
unnamed: J2.2, U3.5 (+)
unnamed: J3.2, U3.10 (+)
unnamed: J4.2, U3.12 (+)
unnamed: J5.2, U4.3 (+)
unnamed: J6.2, U4.5 (+)
unnamed: J7.2, U4.10 (+)
unnamed: J8.2, U4.12 (+)
unnamed: J10.2, U6.3 (+)
unnamed: J11.2, U6.5 (+)
unnamed: J12.2, U6.10 (+)
unnamed: J13.2, U6.12 (+)
unnamed: J14.2, U7.3 (+)
unnamed: J15.2, U7.5 (+)
unnamed: J16.2, U7.10 (+)
unnamed: J17.2, U7.12 (+)
unnamed: J18.1, U7.8, U7.9 (-)
unnamed: J18.2, U7.1, U7.2 (-)
unnamed: J18.3, U6.8, U6.9 (-)
unnamed: J18.4, U6.1, U6.2 (-)
unnamed: J18.5, U4.8, U4.9 (-)
unnamed: J18.6, U4.1, U4.2 (-)
unnamed: J18.7, U3.8, U3.9 (-)
unnamed: J18.8, U3.1, U3.2 (-)
unnamed: J19.1, U3.6 (-), U3.7
unnamed: J19.2, U3.13 (-), U3.14
unnamed: J19.3, U4.6 (-), U4.7
unnamed: J19.4, U4.13 (-), U4.14
unnamed: J19.5, U6.6 (-), U6.7
unnamed: J19.6, U6.13 (-), U6.14
unnamed: J19.7, U7.6 (-), U7.7
unnamed: J19.8, U7.13 (-), U7.14
unnamed: R3.2, R4.2, U5.1 (ADJ)

Notes on the sheet:
GND
Signal
ROTARY_02
ROTARY_05
H_LEFT_JOYSTICK
ROTARY_04
V_LEFT_JOYSTICK
Cursor
ROTARY_06
ROTARY_03
+3.3V
ROTARY_11
ROTARY_09
ROTARY_12
+5V
VBAT+
H_RIGHT_JOYSTICK
V_RIGHT_JOYSTICK
ROTARY_10
ROTARY_07
ROTARY_08
ROTARY_01
